taupter/msx-picoverse-public/2350/case/docs/log.md

# Change Log

## PicoVerse 2350 Case v1.0

- Updated the case README to describe the OBJ shell files, STL button file, and version 1.0 case model attribution.
- Updated the packaging Makefile to mirror `2350/case` into the public `2350/case` output, matching the existing 2040 case copy flow.
