taupter/msx-picoverse-public/2040/case/docs/log.md

# Change Log

## PicoVerse 2040 Case v1.41

- Added a case README describing the version 1.41 files, Pakoto case STL files, and Paco Baron attribution.
