taupter/msx-picoverse-public/docs/msx-picoverse-2350-features.md

# MSX PicoVerse 2350 Features

The MSX PicoVerse 2350 is a Raspberry Pi Pico 2350-based MSX-compatible cartridge that offers a variety of features to enhance the MSX experience. Below is a list of its key features:

- **Multi-ROM Support**: The cartridge can store and run multiple MSX ROMs, allowing users to run different games and applications from a single cartridge.
- **Built-in Menu System**: A user-friendly menu system allows users to select and launch ROMs easily.
- **Explorer Firmware**: Unified menu that merges ROMs from flash and microSD in a single list, with MP3/WAV playback from microSD, File Hunter browsing over ESP-01 WiFi, multi-partition microSD browsing, and on-device file deletion for selected SD files.
- **Source Labels (FL/SD)**: Each ROM entry shows whether it comes from flash or microSD.
- **High Compatibility**: Supports a wide range of MSX ROMs, including games and applications for MSX1, MSX2, and MSX2+ systems.
- **Nextor DOS Support**: Compatible with Nextor DOS, enabling advanced file management and storage options. Currently supports Nextor OS 2.1.4 on USB storage and FAT16 microSD partitions up to 4 GB. You can run DSK files using Nextor.
- **Long Name Support**: Supports ROM names up to 60 characters, making it easier to identify games and applications.
- **Support for Various Mappers**: Includes support for multiple ROM mappers, enhancing compatibility with different types of MSX software. Mapper tags supported include: PLA-16, PLA-32, KonSCC, PLN-48, PLN-64, ASC-08, ASC-16, ASC-16X, Konami, NEO-8, NEO-16, and MANBW2.
- **Space Manbow 2 Support**: Dedicated mapper (MANBW2) for Space Manbow 2 ROMs, emulating the AMD AM29F040B flash chip used by the game for save data. Auto-detected for 512 KB Manbow 2 ROMs; save data is volatile (SRAM-backed).
- **openMSX ROM Database**: The LoadROM and MultiROM tools include an embedded SHA-1 database derived from openMSX's `softwaredb.xml`, improving mapper auto-detection accuracy for titles that cannot be reliably identified by heuristic scanning alone.
- **Sunrise IDE Emulation (USB)**: The LoadROM and MultiROM tools support Sunrise IDE emulation via the `-s2` option, embedding the Nextor 2.1.4 Sunrise IDE kernel and bridging USB mass storage (flash drives, USB-to-SD adapters) through the cartridge's USB-C port. The MSX sees a standard Sunrise IDE hard disk. In MultiROM, the Sunrise options can be combined to add multiple SYSTEM entries to the menu.
- **Sunrise IDE Emulation (microSD)**: The `-s1` option provides the same Sunrise IDE emulation but uses the on-board microSD card slot instead of USB. Nextor storage uses FAT16 microSD partitions up to 4 GB. The microSD card is accessed via SPI at 31.25 MHz. Real card identification (OEM, product name, revision) is read from the SD CID register and shown during Nextor boot.
- **Explorer Sunrise Nextor Partition Selection**: Explorer Sunrise Nextor SYSTEM entries can select among compatible FAT16 microSD partitions up to 4 GB. The selected partition label is shown on the ROM detail screen and saved in that ROM's `.PVC` options file. The normal `F2` microSD browser separately supports cycling FAT16, FAT32, and exFAT browsing partitions with `P`.
- **Sunrise IDE + 1MB PSRAM Memory Mapper (USB)**: The `-m2` option combines Sunrise IDE emulation via USB with a 1MB memory mapper (64 × 16KB pages) in an expanded sub-slot architecture. The mapper RAM is backed by external PSRAM on GPIO47 / QMI CS1. Sub-slot 0 serves the Nextor ROM, sub-slot 1 provides the mapper RAM across all four 16KB pages, and mapper page registers (I/O ports FC–FF) are intercepted via PIO1.
- **Sunrise IDE + 1MB PSRAM Memory Mapper (microSD)**: The `-m1` option provides the same mapper architecture as `-m2` but uses the on-board microSD card for storage instead of USB.
- **ESP-01 WiFi Support For Sunrise IDE Modes**: Both the LoadROM and MultiROM tools accept `-w` together with `-s1`, `-m1`, `-s2`, or `-m2`, adding an embedded ESP8266P system ROM and a memory-mapped UART backend for the PicoVerse 2350 ESP-01 header. In MultiROM `-w` is applied to every selected Sunrise IDE entry and is not added to `-c1`/`-c2` Carnivore2 entries. Detailed behaviour is documented in the WiFi guide.
- **Explorer File Hunter Browser**: Press `F3` in Explorer to browse File Hunter through the ESP-01 WiFi module, search online results from the MSX, download ROMs into PSRAM, and save them as `.ROM` files directly in the microSD root.
- **Explorer WiFi Configuration**: Press `F4` in Explorer to enter the WiFi setup flow used by the ESP8266P-compatible WiFi firmware.
- **ROM Loading to PSRAM Mapper via `SROM.COM` (USB)**: The `-c2` option (LoadROM and MultiROM) exposes the cartridge as a Carnivore2-compatible RAM target on top of the 1MB PSRAM mapper, allowing `SROM.COM /D15` to upload ROM files into PSRAM and execute them from RAM while using USB mass storage as the Nextor backend. When combined with `-scc` / `-sccplus`, SROM-uploaded Konami SCC / SCC+ ROMs play through the cartridge's I2S audio path.
- **ROM Loading to PSRAM Mapper via `SROM.COM` (microSD)**: The `-c1` option (LoadROM and MultiROM) provides the same Carnivore2-compatible PSRAM loading workflow as `-c2`, but uses the on-board microSD card as the Nextor backend. SCC / SCC+ emulation is also supported via `-scc` / `-sccplus`.
- **Support for up to 1024 entries (Explorer)**: Per folder view, including ROMs and MP3s; the root view can also include flash entries.
- **Paged ROM List**: The menu loads pages on demand to keep the ROM list responsive with large libraries.
- **Search by Name (Explorer)**: Press `/`, type a query, and press Enter to jump to the first match.
- **microSD Partition Cycle (Explorer)**: Press `P` in the `F2` microSD screen to cycle supported FAT16, FAT32, and exFAT primary/logical partitions. The selected browsing partition is persisted in `/PICOVERSE.PVC`.
- **microSD File Delete (Explorer)**: Press `D` in the `F2` microSD screen to delete the selected file after confirmation. Folders cannot be deleted from Explorer.
- **Search File Hunter (Explorer)**: Press `/` inside File Hunter to run an online File Hunter query and reload the result list.
- **On-device 40/80 Column Toggle**: Press `C` to switch between compact 40-column and wide 80-column menu layouts (when supported by the MSX model).
- **MP3 Player**: MP3 files on microSD appear in the menu and open a player screen with Play/Stop, Pause/Resume, playback status, and elapsed time.
- **ROM Detail Screen**: ROM entries open a details screen with mapper detection/override, cartridge audio profile selection, optional primary PSG DAC mirroring, and WiFi enablement for supported Sunrise Nextor entries before running.
- **SYSTEM ROM Priority**: System ROM entries remain at the top of the list, separate from name sorting.
- **microSD ROM Execution up to 4 MB**: ROM files on the microSD card are streamed into the cartridge's external 8 MB PSRAM (QMI CS1, 52.5 MHz QPI) and executed directly from there. The leading window of the ROM is also mirrored into the 256 KB PSRAM ROM cache for mapper hot-loop access. The size cap per microSD ROM is 4 MB.
- **Easy ROM Management**: Users can easily add, remove, and organize ROMs using a simple tool on their PC.
- **Fast Loading Times**: Utilizes the high-speed capabilities of the Raspberry Pi Pico to ensure quick loading times for games and applications.
- **Firmware Updates**: The cartridge firmware can be updated via USB, allowing users to benefit from new features and improvements over time.
- **Compact Design**: The cartridge is designed to fit seamlessly into MSX systems without adding bulk.
- **SD Card Slot**: Equipped with an SD card slot for easy storage and transfer of ROMs and files.
- **Audio Profile Selection**: Allows users to select mutually exclusive per-ROM cartridge audio profiles: None, SCC, SCC+, external SCC/SCC+, Dual PSG, MSX-MUSIC, or YM2151/SFG when supported by the selected mapper.
- **Primary PSG Mirroring**: Explorer ROM launches include an independent **PSG** Yes/No option. When enabled, the Pico captures primary PSG writes on ports `0xA0`/`0xA1`, generates matching AY/YM audio through `emu2149`, and mixes it into the cartridge I2S DAC output alongside the selected audio profile.
- **SCC/SCC+ Emulation**: When enabled for Konami SCC or Manbow2 mapper ROMs, the cartridge can emulate the SCC and SCC+ sound chips in hardware, providing accurate audio output through an I2S DAC connected to the RP2350. Explorer also offers external SCC/SCC+ profiles for non-SYSTEM ROMs and Sunrise Nextor SYSTEM entries that expect an SCC cartridge in another slot; regular ROMs run the game mapper in subslot 0 and expose a virtual SCC/SCC+ surface in subslot 1, while Sunrise Nextor entries keep storage active and place SCC/SCC+ in a free subslot. The Explorer ROM screen pre-selects **SCC** as the default audio profile when a ROM is detected as Konami SCC (`KonSCC`) or Manbow2 (`MANBW2`). This allows games that use SCC or SCC+ sound to have their full soundtrack without requiring an original SCC cartridge. For details on supported registers and behavior, see the [SCC/SCC+ documentation](docs/msx-picoverse-2350-scc.md).
- **Dual PSG Emulation**: A secondary AY-3-8910 (PSG) engine can be enabled per ROM. In LoadROM this is selected with the `-d` flag; in Explorer it is selected from the ROM screen as **Dual PSG** for regular non-SYSTEM ROMs that are not Konami SCC or Manbow2. The Pico captures `OUT (0x10),A` (register select) and `OUT (0x11),A` (data) on the MSX I/O bus through a dedicated PIO1 write captor and mixes the synthesized output into the same I2S DAC used by the SCC engine. Dual PSG is mutually exclusive with SCC/SCC+ and MSX-MUSIC as a cartridge audio profile, but Explorer's separate **PSG** option can still mirror the primary PSG alongside it. When both are enabled, Explorer routes Dual PSG to left and the mirrored primary PSG to right for stereo separation. For implementation details, see the [Dual PSG documentation](./msx-picoverse-2350-dualpsg.md).
- **MSX-MUSIC Emulation**: A YM2413/MSX-MUSIC engine can be enabled per ROM. In Explorer it is selected from the ROM screen as **MSX-MUSIC** for regular non-SYSTEM ROMs that are not Konami SCC or Manbow2. The firmware captures writes to MSX-MUSIC ports `0x7C` and `0x7D`, routes synthesized audio through I2S, and exposes an FM-PAC-compatible BIOS from a hidden Explorer UF2 flash payload instead of embedding it in the Pico firmware binary. MSX-MUSIC is mutually exclusive with SCC/SCC+ and Dual PSG as a cartridge audio profile, and can be mixed with Explorer's separate primary PSG mirror.
- **YM2151 / Yamaha SFG Emulation**: Explorer offers **YM2151 (SFG05)** and **YM2151 (SFG01)** profiles for supported game ROMs and Sunrise Nextor SYSTEM ROMs. Game ROMs run the selected mapper in expanded subslot 0 and expose the SFG-like YM2151 surface plus the selected SFG BIOS image in subslot 1. Sunrise Nextor SYSTEM launches keep Nextor and mapper RAM in their SYSTEM layout and place the SFG cartridge in a free subslot, using subslot 2 without WiFi or subslot 3 with WiFi. The SFG 64K ROM is stored as a hidden Explorer flash payload; SFG05 uses the first 32K image and SFG01 uses the second 32K image.
