taupter/msx-picoverse-public/images/2026-05-23_17-53.png

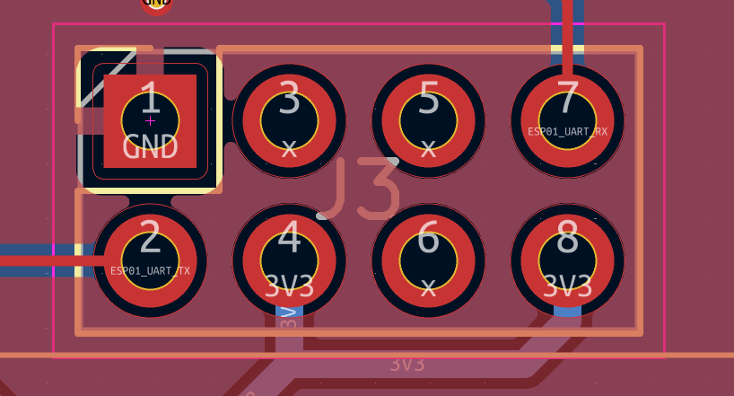
images/2026-05-23_17-53.png
