taupter/msx-picoverse-public/2040/software/loadrom.pio/pico/joystick/tusb_config.h

// MSX PICOVERSE PROJECT
// (c) 2026 Cristiano Goncalves
// The Retro Hacker
//
// tusb_config.h - TinyUSB configuration for standalone USB joystick firmware
//
// Uses HID report protocol (not boot protocol) because gamepads do not
// have a standardised boot protocol.  The firmware parses HID report
// descriptors at enumeration time to locate D-pad, analog stick, and
// button fields.
//
// Also supports XInput (Xbox 360) controllers via a custom class driver
// that claims vendor-specific interfaces (class 0xFF, subclass 0x5D).
//
// This work is licensed under a "Creative Commons Attribution-NonCommercial-ShareAlike 4.0 International
// License". https://creativecommons.org/licenses/by-nc-sa/4.0/

#ifndef _TUSB_CONFIG_H_
#define _TUSB_CONFIG_H_

#ifdef __cplusplus
 extern "C" {
#endif

//--------------------------------------------------------------------
// COMMON CONFIGURATION
//--------------------------------------------------------------------

#ifndef CFG_TUSB_MCU
  #error CFG_TUSB_MCU must be defined
#endif

#define CFG_TUSB_RHPORT0_MODE       OPT_MODE_HOST

#ifndef CFG_TUSB_OS
#define CFG_TUSB_OS                 OPT_OS_NONE
#endif

#ifndef CFG_TUSB_MEM_SECTION
#define CFG_TUSB_MEM_SECTION
#endif

#ifndef CFG_TUSB_MEM_ALIGN
#define CFG_TUSB_MEM_ALIGN          __attribute__ ((aligned(4)))
#endif

//--------------------------------------------------------------------
// HOST CONFIGURATION
//--------------------------------------------------------------------

// Use report protocol — gamepads have no standard boot protocol.
// The firmware parses HID report descriptors to find field offsets.
#define CFG_TUH_HID_DEFAULT_PROTOCOL  HID_PROTOCOL_REPORT

#define CFG_TUH_ENUMERATION_BUFSIZE 512

#define CFG_TUH_HUB                 1
#define CFG_TUH_CDC                 0
#define CFG_TUH_HID                 4
#define CFG_TUH_MIDI                0
#define CFG_TUH_MSC                 0
#define CFG_TUH_VENDOR              0

#define CFG_TUH_DEVICE_MAX          (CFG_TUH_HUB ? 4 : 1)

#define CFG_TUH_HID_EPIN_BUFSIZE    64
#define CFG_TUH_HID_EPOUT_BUFSIZE   64

#ifdef __cplusplus
 }
#endif

#endif /* _TUSB_CONFIG_H_ */
