taupter/msx-picoverse-public/2350/software/explorer.pio/pico/explorer/explorer.c

// MSX PICOVERSE PROJECT
// (c) 2025 Cristiano Goncalves
// The Retro Hacker
//
// explorer.c - PicoVerse 2350 Explorer firmware (ROM loader + SD support)
//
// This work is licensed  under a "Creative Commons Attribution-NonCommercial-ShareAlike 4.0 International
// License". https://creativecommons.org/licenses/by-nc-sa/4.0/

#include <stdio.h>
#include <string.h>
#include <ctype.h>
#include <stdlib.h>
#include <stdarg.h>
#include "ff.h"
#include "diskio.h"
#include "my_rtc.h"
#include "pico/stdlib.h"
#include "pico/multicore.h"
#include "pico/unique_id.h"
#include "hardware/clocks.h"
#include "hardware/dma.h"
#include "hardware/pio.h"
#include "hardware/structs/qmi.h"
#include "hardware/regs/qmi.h"
#include "hardware/structs/xip_ctrl.h"
#include "hardware/sync.h"
#include "hardware/uart.h"
#include "hardware/regs/uart.h"
#include "hardware/irq.h"
#include "hw_config.h"
#include "explorer.h"
#include "mapper_detect.h"
#include "mp3.h"
#include "c2_emu.h"
#include "emu2212.h"
#include "emu2149.h"
#include "emu2413.h"
#include "emu2151.h"
#include "msx_bus.pio.h"
#include "pico/audio_i2s.h"
#include "sunrise_ide.h"
#include "sunrise_sd.h"

// config area and buffer for the ROM data
#define ROM_NAME_MAX    71          // Maximum size of the ROM name on the 80-column detail screen
#define MAX_ROM_RECORDS 1024        // Maximum ROM files supported (flash + SD)
#define MAX_FLASH_RECORDS 128       // Maximum ROM files stored in flash
#define ROM_RECORD_SIZE (ROM_NAME_MAX + 1 + (sizeof(uint32_t) * 2)) // Name + mapper + size + offset
#define MENU_ROM_SIZE   (32u * 1024u) // Full menu ROM size stored before config records
#define CONFIG_AREA_SIZE (16u * 1024u)
#define ROM_SELECT_MENU 0xFEu
#define ROM_SELECT_WIFI_CONFIG 0xFFF0u
#define WIFI_CONFIG_FLASH_OFFSET (MENU_ROM_SIZE + CONFIG_AREA_SIZE)
#define WIFI_CONFIG_ROM_SIZE (8u * 1024u)
#define WIFI_BIOS_FLASH_OFFSET (WIFI_CONFIG_FLASH_OFFSET + WIFI_CONFIG_ROM_SIZE)
#define WIFI_BIOS_ROM_SIZE (16u * 1024u)
#define FMPAC_BIOS_FLASH_OFFSET (WIFI_BIOS_FLASH_OFFSET + WIFI_BIOS_ROM_SIZE)
#define FMPAC_BIOS_ROM_SIZE (64u * 1024u)
#define SFG_BIOS_FLASH_OFFSET (FMPAC_BIOS_FLASH_OFFSET + FMPAC_BIOS_ROM_SIZE)
#define SFG_BIOS_ROM_SIZE (64u * 1024u)
#define WIFI_CONFIG_RETURN_MENU 0xE0u
#define MONITOR_ADDR    (0xBF7F)    // ROM select register just below the menu control window
#define CACHE_SIZE      (256u * 1024u)     // 256KB cache size for ROM data

#define SOURCE_SD_FLAG  0x80 // Flag in the mapper byte indicating the ROM is on SD
#define FOLDER_FLAG     0x40 // Flag in the mapper byte indicating the record is a folder
#define MP3_FLAG        0x20 // Flag in the mapper byte indicating the record is an MP3 file
#define OVERRIDE_FLAG   0x10 // Flag in the mapper byte indicating manual override
#define AUDIO_TYPE_MASK 0x0F // Low bits identify audio subtypes when MP3_FLAG is set
#define AUDIO_TYPE_WAV  0x01 // Audio subtype: PCM WAV file

#define EXPLORER_MP3_DISABLED 0

#define FILES_PER_PAGE  19 // Maximum files per page on the menu
#define CTRL_BASE_ADDR  0xBFF0 // Control registers base address
#define CTRL_COUNT_L    (CTRL_BASE_ADDR + 0) // Control: total record count low byte
#define CTRL_COUNT_H    (CTRL_BASE_ADDR + 1) // Control: total record count high byte
#define CTRL_PAGE       (CTRL_BASE_ADDR + 2) // Control: current page index
#define CTRL_STATUS     (CTRL_BASE_ADDR + 3) // Control: status register
#define CTRL_CMD        (CTRL_BASE_ADDR + 4) // Control: command register
#define CTRL_MATCH_L    (CTRL_BASE_ADDR + 5) // Control: match index low byte
#define CTRL_MATCH_H    (CTRL_BASE_ADDR + 6) // Control: match index high byte
#define CTRL_MAPPER     (CTRL_BASE_ADDR + 7) // Control: mapper value
#define CTRL_ACK        (CTRL_BASE_ADDR + 8) // Control: command ack
#define CTRL_MAGIC      0xA5 // Control: magic value to indicate valid command
#define CTRL_STATUS_SD_MISSING 0x5D // Control: selected source is microSD but no card is available
#define CTRL_QUERY_BASE 0xBFC0 // Control: query string base address
#define CTRL_QUERY_SIZE 32 // Control: query string size
#define CMD_APPLY_FILTER 0x01 // Command: apply filter
#define CMD_FIND_FIRST   0x02 // Command: find first match
#define CMD_ENTER_DIR    0x03 // Command: enter directory
#define CMD_DETECT_MAPPER 0x04 // Command: detect mapper on demand
#define CMD_SET_MAPPER    0x05 // Command: set mapper override
#define CMD_SET_SOURCE    0x06 // Command: switch visible source set
#define CMD_LOAD_OPTIONS  0x07 // Command: load ROM options from microSD .PVC file
#define CMD_SAVE_OPTIONS  0x08 // Command: save ROM options to microSD .PVC file
#define CMD_PREPARE_QUICK_RUN 0x09 // Command: load saved/default launch options for quick-run
#define CMD_CYCLE_SD_PARTITION 0x0A // Command: cycle Explorer microSD browse partition
#define CMD_DELETE_SD_FILE 0x0B // Command: delete selected Explorer microSD file
#define CMD_FH_LIST_PAGE   0x40 // Command: File Hunter list page from menu ROM
#define CMD_FH_DOWNLOAD    0x41 // Command: File Hunter download/save from menu ROM
#define CMD_FH_SEARCH      0x42 // Command: File Hunter search from menu ROM
#define CMD_FH_WIFI_STATUS 0x43 // Command: File Hunter WiFi status from menu ROM
#define CMD_FH_WIFI_CONFIG 0x44 // Command: File Hunter WiFi setup from menu ROM

#define FH_CTRL_BASE    0xBFF0
#define FH_COUNT_L      (FH_CTRL_BASE + 0)
#define FH_COUNT_H      (FH_CTRL_BASE + 1)
#define FH_PAGE         (FH_CTRL_BASE + 2)
#define FH_STATUS       (FH_CTRL_BASE + 3)
#define FH_CMD          (FH_CTRL_BASE + 4)
#define FH_SELECT_L     (FH_CTRL_BASE + 5)
#define FH_SELECT_H     (FH_CTRL_BASE + 6)
#define FH_PROGRESS_L   (FH_CTRL_BASE + 7)
#define FH_PROGRESS_H   (FH_CTRL_BASE + 8)
#define FH_RESULT       (FH_CTRL_BASE + 9)
#define FH_QUERY_BASE   0xBFC0
#define FH_QUERY_SIZE   32
#define FH_STATUS_TEXT_BASE 0xBF80
#define FH_STATUS_TEXT_SIZE 64
#define CTRL_CHIP_ID_BASE (FH_STATUS_TEXT_BASE + FH_STATUS_TEXT_SIZE - 17u) // Control: Pico unique board ID string
#define CTRL_CHIP_ID_SIZE 17u // Control: 16 hex digits plus terminator
#define CTRL_SD_PARTITION_INFO_BASE FH_STATUS_TEXT_BASE
#define CTRL_SD_PARTITION_INFO_SIZE 32u
#define CTRL_VDP_FREQ   0xBFA0 // Control: per-ROM VDP 50/60Hz load read-back (Pico -> MSX)
#define VDP_FREQ_DEFAULT 0u
#define VDP_FREQ_60HZ    1u
#define VDP_FREQ_50HZ    2u
#define FH_DATA_BASE    0xB900
#define FH_RECORD_FLAG_OFFSET ROM_NAME_MAX
#define FH_RECORD_SIZE_OFFSET (FH_RECORD_FLAG_OFFSET + 1u)
#define FH_RECORD_SIZE  (ROM_NAME_MAX + 3u)
#define FH_FILES_PER_PAGE 19
#define FH_MAX_RESULTS 384
#define FH_HTTP_BUFFER_SIZE (256u * 1024u)
#define FH_HTTP_CHUNK_SIZE 2048u
#define FH_HOST "msxpico.file-hunter.com"
#define FH_ENDPOINT "/picoverse.php"
#define FH_DEFAULT_QUERY "1"
#define FH_WIFI_CONNECT_WAIT_US 30000000u
#define FH_STATUS_READY 0xA5
#define FH_STATUS_BUSY  0x5A
#define FH_RESULT_SAVING 0x02
#define FH_RECORD_FLAG_MESSAGE 0x80u
#define FH_CMD_LIST_PAGE 0x01
#define FH_CMD_DOWNLOAD  0x02
#define FH_CMD_EXIT      0x03
#define FH_CMD_SEARCH    0x04
#define FH_CMD_WIFI_STATUS 0x05

#define SOURCE_MODE_ALL   0x00
#define SOURCE_MODE_FLASH 0x01
#define SOURCE_MODE_SD    0x02
#define SOURCE_MODE_FILEHUNTER 0x03

#define CTRL_AUDIO      (CTRL_BASE_ADDR + 9) // Control: audio profile selection
#define CTRL_WIFI_SUPPORT (CTRL_BASE_ADDR + 10) // Control: Sunrise WiFi support (0=No, 1=Yes)
#define CTRL_PSG_EMULATION (CTRL_BASE_ADDR + 11) // Control: primary PSG emulation (0=No, 1=Yes)
#define CTRL_WAVEGAME_ROM (CTRL_BASE_ADDR + 12) // Control: selected SD ROM has WAVEGAME sidecar audio
#define CTRL_SD_PARTITION (CTRL_BASE_ADDR + 13) // Control: selected Sunrise SD partition number
#define CTRL_SD_BROWSE_PARTITION (CTRL_BASE_ADDR + 14) // Control: selected Explorer microSD partition number
#define CTRL_AUDIO_VOLUME (CTRL_BASE_ADDR + 15) // Control: per-ROM audio volume percent

#define AUDIO_PROFILE_NONE       0u
#define AUDIO_PROFILE_SCC        1u
#define AUDIO_PROFILE_SCC_PLUS   2u
#define AUDIO_PROFILE_DUAL_PSG 3u
#define AUDIO_PROFILE_MSX_MUSIC 4u
#define AUDIO_PROFILE_SCC_EXTERNAL 5u
#define AUDIO_PROFILE_SCC_PLUS_EXTERNAL 6u
#define AUDIO_PROFILE_YM2151_SFG05 7u
#define AUDIO_PROFILE_YM2151_SFG01 8u
#define AUDIO_PROFILE_MEGARAM_SCC 9u
#define AUDIO_PROFILE_MEGARAM_SCC_PLUS 10u

#define PSG_SAMPLE_RATE 44100
#define PSG_CLOCK       1789773
#define PSG_VOLUME_SHIFT 2
#define PSG_QUALITY_FAST 0
#define PSG_QUALITY_HIGH 1
#define PSG_PORT_REG    0x10u
#define PSG_PORT_DATA   0x11u
#define MAIN_PSG_PORT_REG  0xA0u
#define MAIN_PSG_PORT_DATA 0xA1u

#define MSX_MUSIC_SAMPLE_RATE 44100
#define MSX_MUSIC_CLOCK       3579545
#define MSX_MUSIC_VOLUME_SHIFT 2
#define MSX_MUSIC_PSG_VOLUME_SHIFT 0
/* Soft-knee limiter for the post-gain FM sample: below the knee the output is
 * a pure linear MSX_MUSIC_VOLUME_SHIFT gain (so normal games are unchanged);
 * above the knee, loud/dense OPLL content is smoothly compressed toward the
 * ceiling instead of hard-clipping (which produced a robotic, low-volume tone
 * on heavy arrangements like Aleste Gaiden). */
#define MSX_MUSIC_LIMIT_KNEE  24000
#define MSX_MUSIC_LIMIT_CEIL  32767
#define MSX_MUSIC_PORT_REG    0x7Cu
#define MSX_MUSIC_PORT_DATA   0x7Du
#define FMPAC_BIOS_SIZE       FMPAC_BIOS_ROM_SIZE
#define SFG_BIOS_SIZE         SFG_BIOS_ROM_SIZE
#define SFG_BIOS_VARIANT_SIZE (32u * 1024u)

#define AUDIO_VOLUME_DEFAULT 100u
#define AUDIO_VOLUME_MAX     200u

#define YM2151_SAMPLE_RATE    44100
#define YM2151_CLOCK          3579545u
#define YM2151_FRAME_DIVIDER  64u
#define YM2151_CYCLES_PER_FRAME 1u
#define YM2151_WRITE_APPLY_CYCLES 0u
#define YM2151_WRITE_SERVICE_BUDGET 4u
#define YM2151_WRITE_QUEUE_SIZE 512u
#define YM2151_WRITE_QUEUE_MASK (YM2151_WRITE_QUEUE_SIZE - 1u)
#define YM2151_PSG_VOLUME_SHIFT 0
#define YM2151_BASE_VOLUME_PERCENT 200u

#define WIFI_MEM_F2_ADDR      0x7F05u
#define WIFI_MEM_CMD_ADDR     0x7F06u
#define WIFI_MEM_DATA_ADDR    0x7F07u
#define WIFI_F2_FORCE_SETUP   0xF1u
#define WIFI_RX_FIFO_SIZE     2080u
#define WIFI_RX_SERVICE_BUDGET 32u
#define WIFI_QUICK_WAIT_US    25000u
#define WIFI_UART_DEFAULT_BAUD 859372u
#define WIFI_STATUS_RX_READY  0x01u
#define WIFI_STATUS_TX_BUSY   0x02u
#define WIFI_STATUS_RX_FULL   0x04u
#define WIFI_STATUS_QUICK_RX  0x08u
#define WIFI_STATUS_UNDERRUN  0x10u
#define WIFI_STATUS_FREE_BITS 0x80u
#define WIFI_UART_INSTANCE    uart1

#define DATA_BASE_ADDR   0xB900 // Data buffer base address
#define DATA_BUFFER_SIZE (FH_STATUS_TEXT_BASE - DATA_BASE_ADDR) // Data buffer size
#define DATA_MAGIC_0     'P' // Data header magic bytes
#define DATA_MAGIC_1     'V' // Data header magic bytes
#define DATA_MAGIC_2     'E' // Data header magic bytes
#define DATA_MAGIC_3     'X' // Data header magic bytes
#define DATA_VERSION     1 // Data header version
#define DATA_HEADER_SIZE 24 // Data header size in bytes
#define DATA_RECORD_TABLE_ENTRY_SIZE 4 // Size of each record table entry
#define DATA_RECORD_PAYLOAD_SIZE 13 // Minimum size of each record payload
#define TLV_NAME_OFFSET  0x01 // Type-Length-Value: Name offset
#define TLV_MAPPER       0x02 // Type-Length-Value: Mapper
#define TLV_SIZE         0x03 // Type-Length-Value: Size

#define PVC_OPTIONS_MAGIC_0 'P'
#define PVC_OPTIONS_MAGIC_1 'V'
#define PVC_OPTIONS_MAGIC_2 'C'
#define PVC_OPTIONS_MAGIC_3 '1'
#define PVC_OPTIONS_LEGACY_SIZE 6u
#define PVC_OPTIONS_MAPPER_SIZE 7u
#define PVC_OPTIONS_PARTITION_SIZE 8u
#define PVC_OPTIONS_VOLUME_SIZE 9u
#define PVC_OPTIONS_SIZE 10u

#define PV_CONFIG_MAGIC_0 'P'
#define PV_CONFIG_MAGIC_1 'V'
#define PV_CONFIG_MAGIC_2 'C'
#define PV_CONFIG_MAGIC_3 'F'
#define PV_CONFIG_SIZE 5u
#define PV_CONFIG_PATH "/PICOVERSE.PVC"


// MP3 control registers
#define MP3_CTRL_BASE      0xBFE0 // MP3 control registers base address
#define MP3_CTRL_CMD       (MP3_CTRL_BASE + 0)
#define MP3_CTRL_STATUS    (MP3_CTRL_BASE + 1)
#define MP3_CTRL_INDEX_L   (MP3_CTRL_BASE + 2)
#define MP3_CTRL_INDEX_H   (MP3_CTRL_BASE + 3)
#define MP3_CTRL_ELAPSED_L (MP3_CTRL_BASE + 4)
#define MP3_CTRL_ELAPSED_H (MP3_CTRL_BASE + 5)
#define MP3_CTRL_TOTAL_L   (MP3_CTRL_BASE + 6)
#define MP3_CTRL_TOTAL_H   (MP3_CTRL_BASE + 7)
#define MP3_CTRL_MODE      (MP3_CTRL_BASE + 8)

// MSX protocol command code for MP3 file selection (local to explorer.c)
#define MP3_CMD_SELECT      0x01

typedef struct {
    PIO pio;
    uint sm_read;
    uint sm_write;
    uint offset_read;
    uint offset_write;
} msx_pio_bus_t;

typedef struct {
    PIO pio_read;
    PIO pio_write;
    uint sm_io_read;
    uint sm_io_write;
    uint offset_io_read;
    uint offset_io_write;
} msx_pio_io_bus_t;

static msx_pio_bus_t msx_bus;
static bool msx_bus_programs_loaded = false;
static msx_pio_io_bus_t msx_io_bus;
static bool msx_io_read_program_loaded = false;
static bool msx_io_write_program_loaded = false;

typedef struct {
    uint16_t rom_index;
    bool rom_selected;
} menu_select_ctx_t;

typedef struct {
    uint8_t *bank_regs;
} bank8_ctx_t;

typedef struct {
    uint16_t *bank_regs;
} bank16_ctx_t;

typedef struct {
    uint8_t page;
    uint8_t control;
    uint8_t sram_key_5ffe;
    uint8_t sram_key_5fff;
    uint8_t sram[8192];
} fmpac_state_t;

// This symbol marks the end of the main program in flash.
// Custom data starts right after it
extern const uint8_t __flash_binary_end[];

// PSRAM-backed buffer to cache ROM data
static uint8_t *rom_sram = NULL;
static uint32_t active_rom_size = 0;
static uint32_t rom_cached_size = 0; // Added for PIO implementation
// Effective cache capacity used by prepare_rom_source(). Some mappers (e.g.
// Manbow2) reduce this so the tail of rom_sram can be repurposed (writable
// flash sector emulation), matching multirom's behaviour.
static uint32_t rom_cache_capacity = CACHE_SIZE;
static uint8_t page_buffer[DATA_BUFFER_SIZE];

// pointer to the custom data
static const uint8_t *flash_rom = (const uint8_t *)&__flash_binary_end;
static const uint8_t *rom_data = (const uint8_t *)&__flash_binary_end;
static bool rom_data_in_ram = false;

static uint8_t wifi_rx_fifo[WIFI_RX_FIFO_SIZE];
static volatile uint16_t wifi_rx_head = 0u;
static volatile uint16_t wifi_rx_tail = 0u;
static volatile uint16_t wifi_rx_count = 0u;
static uint8_t wifi_f2_state = 0xFFu;
static bool wifi_uart_ready = false;
static uint32_t wifi_uart_baud = WIFI_UART_DEFAULT_BAUD;
static uint32_t wifi_tx_busy_deadline_us = 0u;
static bool wifi_rx_underrun = false;

static void debug_trace(const char *fmt, ...)
{
#if EXPLORER_USB_STDIO_DEBUG
    va_list args;
    va_start(args, fmt);
    vprintf(fmt, args);
    va_end(args);
    printf("\r\n");
    fflush(stdout);
#else
    (void)fmt;
#endif
}

static inline void __not_in_flash_func(wifi_reset_fifo)(void)
{
    uint32_t irq_state = save_and_disable_interrupts();
    wifi_rx_head = 0u;
    wifi_rx_tail = 0u;
    wifi_rx_count = 0u;
    wifi_rx_underrun = false;
    restore_interrupts(irq_state);
}

static inline bool __not_in_flash_func(wifi_push_rx_byte_locked)(uint8_t data)
{
    if (wifi_rx_count >= WIFI_RX_FIFO_SIZE) return false;
    wifi_rx_fifo[wifi_rx_head] = data;
    wifi_rx_head = (uint16_t)((wifi_rx_head + 1u) % WIFI_RX_FIFO_SIZE);
    ++wifi_rx_count;
    return true;
}

static inline bool __not_in_flash_func(wifi_push_rx_byte)(uint8_t data)
{
    uint32_t irq_state = save_and_disable_interrupts();
    bool pushed = wifi_push_rx_byte_locked(data);
    restore_interrupts(irq_state);
    return pushed;
}

static inline bool __not_in_flash_func(wifi_pop_rx_byte)(uint8_t *data_out)
{
    uint32_t irq_state = save_and_disable_interrupts();
    if (wifi_rx_count == 0u)
    {
        restore_interrupts(irq_state);
        return false;
    }
    *data_out = wifi_rx_fifo[wifi_rx_tail];
    wifi_rx_tail = (uint16_t)((wifi_rx_tail + 1u) % WIFI_RX_FIFO_SIZE);
    --wifi_rx_count;
    restore_interrupts(irq_state);
    return true;
}

static inline uint16_t __not_in_flash_func(wifi_rx_count_snapshot)(void)
{
    uint32_t irq_state = save_and_disable_interrupts();
    uint16_t count = wifi_rx_count;
    restore_interrupts(irq_state);
    return count;
}

static inline bool __not_in_flash_func(wifi_hw_tx_busy)(void)
{
    return (uart_get_hw(WIFI_UART_INSTANCE)->fr & UART_UARTFR_BUSY_BITS) != 0u;
}

static inline void __not_in_flash_func(wifi_hw_rx_drain)(void)
{
    uint32_t irq_state = save_and_disable_interrupts();
    while (uart_is_readable(WIFI_UART_INSTANCE))
    {
        (void)uart_getc(WIFI_UART_INSTANCE);
    }
    restore_interrupts(irq_state);
}

static inline void __not_in_flash_func(wifi_pio_rx_reset)(void)
{
    wifi_hw_rx_drain();
}

static inline void __not_in_flash_func(wifi_pio_tx_reset)(void)
{
    while (wifi_hw_tx_busy()) { }
    wifi_tx_busy_deadline_us = 0u;
}

static inline void __not_in_flash_func(wifi_service_rx)(void)
{
    uint16_t budget = WIFI_RX_SERVICE_BUDGET;
    uint32_t irq_state;

    if (!wifi_uart_ready) return;
    irq_state = save_and_disable_interrupts();
    while (budget-- != 0u && uart_is_readable(WIFI_UART_INSTANCE))
    {
        if (!wifi_push_rx_byte_locked((uint8_t)uart_getc(WIFI_UART_INSTANCE))) break;
    }
    restore_interrupts(irq_state);
}

static void __not_in_flash_func(wifi_uart_rx_irq)(void)
{
    while (uart_is_readable(WIFI_UART_INSTANCE))
    {
        uint8_t data = (uint8_t)uart_getc(WIFI_UART_INSTANCE);
        (void)wifi_push_rx_byte_locked(data);
    }
}

static inline uint32_t __not_in_flash_func(wifi_uart_frame_time_us)(void)
{
    return (10000000u + (wifi_uart_baud - 1u)) / wifi_uart_baud;
}

static inline void __not_in_flash_func(wifi_uart_init_once)(void)
{
    if (wifi_uart_ready) return;

    (void)uart_init(WIFI_UART_INSTANCE, wifi_uart_baud);
    gpio_set_function(PIN_ESP_UART_TX, GPIO_FUNC_UART_AUX);
    gpio_set_function(PIN_ESP_UART_RX, GPIO_FUNC_UART_AUX);
    uart_set_format(WIFI_UART_INSTANCE, 8, 1, UART_PARITY_NONE);
    uart_set_hw_flow(WIFI_UART_INSTANCE, false, false);
    uart_set_fifo_enabled(WIFI_UART_INSTANCE, true);

    wifi_hw_rx_drain();
    wifi_f2_state = 0xFFu;
    wifi_reset_fifo();
    wifi_tx_busy_deadline_us = 0u;
    wifi_uart_ready = true;

    int uart_irq = (WIFI_UART_INSTANCE == uart0) ? UART0_IRQ : UART1_IRQ;
    irq_set_exclusive_handler(uart_irq, wifi_uart_rx_irq);
    irq_set_enabled(uart_irq, true);
    uart_set_irq_enables(WIFI_UART_INSTANCE, true, false);
}

static inline void __not_in_flash_func(wifi_handle_cmd_write)(uint8_t cmd)
{
    wifi_uart_init_once();
    if (cmd == 20u)
    {
        wifi_reset_fifo();
        wifi_pio_tx_reset();
        wifi_pio_rx_reset();
    }
}

static inline uint8_t __not_in_flash_func(wifi_status_read)(void)
{
    wifi_uart_init_once();
    wifi_service_rx();
    uint8_t status = 0u;
    uint16_t rx_count = wifi_rx_count_snapshot();
    if (rx_count != 0u) status |= WIFI_STATUS_RX_READY;
    if (rx_count >= WIFI_RX_FIFO_SIZE) status |= WIFI_STATUS_RX_FULL;
    if (wifi_hw_tx_busy() || !uart_is_writable(WIFI_UART_INSTANCE) ||
        (int32_t)(time_us_32() - wifi_tx_busy_deadline_us) < 0)
    {
        status |= WIFI_STATUS_TX_BUSY;
    }
    if (wifi_rx_underrun)
    {
        status |= WIFI_STATUS_UNDERRUN;
        wifi_rx_underrun = false;
    }
    return status;
}

static inline uint8_t __not_in_flash_func(wifi_data_read)(void)
{
    wifi_uart_init_once();

    uint8_t data;
    wifi_service_rx();
    if (wifi_pop_rx_byte(&data)) return data;

    uint32_t deadline = time_us_32() + WIFI_QUICK_WAIT_US;
    while ((int32_t)(time_us_32() - deadline) < 0)
    {
        wifi_service_rx();
        if (wifi_pop_rx_byte(&data)) return data;
    }

    wifi_rx_underrun = true;
    return 0xFFu;
}

static inline bool __not_in_flash_func(wifi_handle_mem_write)(uint16_t addr, uint8_t data)
{
    if (addr == WIFI_MEM_F2_ADDR) { wifi_f2_state = data; return true; }
    if (addr == WIFI_MEM_CMD_ADDR) { wifi_handle_cmd_write(data); return true; }
    if (addr == WIFI_MEM_DATA_ADDR)
    {
        wifi_uart_init_once();
        uart_putc_raw(WIFI_UART_INSTANCE, (char)data);
        wifi_tx_busy_deadline_us = time_us_32() + wifi_uart_frame_time_us();
        return true;
    }
    return false;
}

static inline uint8_t __not_in_flash_func(wifi_handle_mem_read)(const uint8_t *wifi_rom_base, uint32_t wifi_rom_size, uint16_t addr)
{
    if (addr == WIFI_MEM_F2_ADDR) return wifi_f2_state;
    if (addr == WIFI_MEM_CMD_ADDR) return wifi_data_read();
    if (addr == WIFI_MEM_DATA_ADDR) return wifi_status_read();
    if (addr >= 0x4000u && addr <= 0x7FFFu)
    {
        uint32_t rel = (uint32_t)(addr - 0x4000u);
        if (rel < wifi_rom_size) return wifi_rom_base[rel];
    }
    return 0xFFu;
}

// External PSRAM region used to buffer SD-loaded ROMs. Defined later
// alongside the PSRAM bring-up code; declared here for use by earlier
// functions such as load_rom_from_sd().
static psram_region_t sd_rom_region;
static psram_region_t rom_cache_region;
static psram_region_t mapper_region;
static psram_region_t c2_rom_region;
static psram_region_t megaram_region;
static psram_region_t mp3_buffer_region;
static psram_region_t fh_list_region;
static psram_region_t fh_download_region;
static bool psram_bring_up_once(void);
static bool psram_prepare_mp3_buffer(void);

uint8_t ctr_val = 0xFF;    
BYTE const pdrv = 0;  // Physical drive number
DSTATUS ds = 1; // Disk status (1 = not initialized)

// Structure to represent a ROM record
// The ROM record will contain the name of the ROM, the mapper code, the size of the ROM and the offset in the flash memory
// Name: ROM_NAME_MAX bytes
// Mapper: 1 byte
// Size: 4 bytes
// Offset: 4 bytes
typedef struct {
    char Name[ROM_NAME_MAX];
    unsigned char Mapper;
    unsigned long Size;
    unsigned long Offset;
} ROMRecord;

ROMRecord records[MAX_ROM_RECORDS]; // Array to store the ROM records

#define SD_PATH_MAX        256
#define SD_PATH_BUFFER_SIZE 19000
#define MIN_ROM_SIZE       8192
#define MAX_ROM_SIZE       (15u * 1024u * 1024u)
#define SD_ROM_MAX_SIZE    (4u * 1024u * 1024u) // PSRAM region capacity for SD-loaded ROMs
#define SD_BROWSE_PARTITION_MAX 20u
#define MP3_PSRAM_BUFFER_SIZE 65536u
#define MAPPER_SUNRISE_USB        10
#define MAPPER_SUNRISE_MAPPER_USB 11
#define MAPPER_SYSTEM             MAPPER_SUNRISE_USB
#define MAPPER_SUNRISE_SD         15
#define MAPPER_SUNRISE_MAPPER_SD  16
#define MAPPER_C2_SD              17
#define MAPPER_C2_USB             18
#define MAPPER_MEGARAM_SD         19
#define MAPPER_MEGARAM_USB        20
#define MAPPER_MEGARAM            21

static const char *MAPPER_DESCRIPTIONS[] = {
    "PLA-16", "PLA-32", "KonSCC", "PLN-48", "ASC-08",
    "ASC-16", "Konami", "NEO-8", "NEO-16", "SYSTEM",
    "SYSTEM", "ASC16X", "PLN-64", "MANBW2"
};

#define MAPPER_DESCRIPTION_COUNT (sizeof(MAPPER_DESCRIPTIONS) / sizeof(MAPPER_DESCRIPTIONS[0]))

static char sd_path_buffer[SD_PATH_BUFFER_SIZE];
static uint16_t sd_path_offsets[MAX_ROM_RECORDS];
static uint16_t sd_path_buffer_used = 0;
static uint16_t sd_record_count = 0;
static bool sd_mounted = false;
static uint8_t sd_mounted_partition = 0;
static uint8_t sd_browse_partition = 0;
static bool sd_config_loaded = false;
static sd_card_t *sd_card = NULL;
static uint16_t total_record_count = 0;
static uint16_t full_record_count = 0;
static uint8_t current_page = 0;
static uint16_t filtered_indices[MAX_ROM_RECORDS];
static char filter_query[CTRL_QUERY_SIZE];
static volatile uint8_t ctrl_cmd_state = 0;
static volatile uint8_t ctrl_mapper_value = 0;
static volatile uint8_t ctrl_ack_value = 0;
static uint16_t match_index = 0xFFFF;
static ROMRecord flash_records[MAX_FLASH_RECORDS];
static uint16_t flash_record_count = 0;
static char sd_current_path[SD_PATH_MAX] = "/";
static uint8_t browse_source_mode = SOURCE_MODE_FLASH;
static uint8_t ctrl_status_value = CTRL_MAGIC;
static volatile bool refresh_requested = false;
static volatile bool refresh_in_progress = false;
static bool refresh_worker_started = false;
static volatile bool detect_mapper_pending = false;

// Chunked directory scan state machine (yields back to MP3 loop between chunks)
#define REFRESH_CHUNK_SIZE 8
typedef enum {
    REFRESH_IDLE = 0,
    REFRESH_INIT,
    REFRESH_SCAN_FOLDERS,
    REFRESH_SORT_FOLDERS,
    REFRESH_SCAN_FILES,
    REFRESH_FINALIZE
} refresh_state_t;
static refresh_state_t refresh_state = REFRESH_IDLE;
static DIR refresh_dir;
static uint16_t refresh_record_index = 0;
static uint16_t refresh_folder_count = 0;
static bool refresh_has_parent = false;
static volatile uint16_t detect_mapper_index = 0;
static volatile uint16_t mp3_selected_index = 0;
static volatile bool mp3_pending_select = false;
static volatile uint16_t mp3_pending_index = 0;
static volatile uint8_t mp3_pending_cmd = 0;
static volatile uint8_t mp3_play_mode = MP3_PLAY_MODE_SINGLE;
static uint16_t mp3_playing_filtered_index = 0xFFFF;
static volatile uint8_t ctrl_audio_selection = AUDIO_PROFILE_NONE;
static volatile uint8_t ctrl_wifi_support = 0; // 0=disabled, 1=enabled for Sunrise Nextor launches
static volatile uint8_t ctrl_psg_emulation = 0; // 0=disabled, 1=primary PSG over I2S
static volatile uint8_t ctrl_wavegame_rom = 0; // 0=normal ROM, 1=WAVEGAME sidecars detected
static volatile uint8_t ctrl_sd_partition = 0; // 0=auto/default, 1-4=MBR primary partition
static volatile uint8_t ctrl_audio_volume = AUDIO_VOLUME_DEFAULT; // per-ROM audio volume percent
static volatile uint8_t ctrl_vdp_frequency = VDP_FREQ_DEFAULT; // per-ROM VDP 50/60Hz option (0=default,1=60,2=50)
static volatile uint8_t vdp_freq_launch = VDP_FREQ_DEFAULT; // 50/60Hz to inject into the launched game's INIT (regular game mappers only)
static uint8_t ctrl_sd_partition_info[CTRL_SD_PARTITION_INFO_SIZE];
static char pico_chip_id[CTRL_CHIP_ID_SIZE] = "0000000000000000";
static bool wavegame_active = false;
static bool wavegame_psg_mirror_active = false;
static char wavegame_dir[SD_PATH_MAX];
static bool wavegame_defer_next = false;
static bool wavegame_deferred_valid = false;
static uint8_t wavegame_deferred_data = 0;

static uint8_t fh_page_index = 0;
static uint8_t fh_status = FH_STATUS_READY;
static uint8_t fh_result = 0;
static uint16_t fh_progress_percent = 0;
static uint8_t fh_query[FH_QUERY_SIZE];
static uint16_t fh_selected_index = 0;
static char fh_wifi_status_text[FH_STATUS_TEXT_SIZE];
static uint8_t fh_tcp_last_error = 0;
static uint32_t fh_download_size = 0;
static char fh_download_name[ROM_NAME_MAX + 1];

#define FH_SAVE_IDLE 0u
#define FH_SAVE_RUNNING 1u
#define FH_SAVE_DONE 2u
#define FH_SAVE_FAILED 3u

static uint8_t fh_sd_save_chunk[1024];
static volatile uint8_t fh_save_state = FH_SAVE_IDLE;
static FIL fh_save_file;
static uint32_t fh_save_offset = 0;
static bool fh_save_file_open = false;
static bool fh_save_close_pending = false;
static FILINFO fh_download_timestamp;
static volatile bool fh_menu_window_active = false;
static volatile bool fh_service_menu_window = false;

typedef struct {
    char name[ROM_NAME_MAX + 1];
    uint16_t size_kb;
} fh_catalog_record_t;

static fh_catalog_record_t fh_catalog[FH_MAX_RESULTS];
static uint16_t fh_catalog_count = 0;
static bool fh_catalog_loaded = false;
static bool fh_catalog_message = false;
static bool fh_network_verified = false;
static uint8_t fh_tcp_buffer[FH_HTTP_CHUNK_SIZE + 2u];
static char fh_active_query[FH_QUERY_SIZE];

// SCC emulation state + I2S audio
#define SCC_VOLUME_SHIFT 2  // Left-shift SCC output for volume boost (4x)
#define SCC_AUDIO_BUFFER_SAMPLES 256
static SCC scc_instance;
static struct audio_buffer_pool *scc_audio_pool;
static bool scc_audio_started = false;
static struct audio_buffer_pool *rom_audio_handoff_pool;

static PSG psg_instance;
static spin_lock_t *dual_psg_lock = NULL;
static struct audio_buffer_pool *dual_psg_audio_pool;
static bool dual_psg_ready = false;
static bool dual_psg_audio_started = false;
static bool dual_psg_core1_services_io = true;

static PSG main_psg_instance;
static spin_lock_t *main_psg_lock = NULL;
static struct audio_buffer_pool *main_psg_audio_pool;
static bool main_psg_ready = false;
static bool main_psg_audio_started = false;
static bool main_psg_core1_services_io = true;

// Lock-free single-producer/single-consumer ring used when core0 owns the MSX
// I/O write FIFO (Sunrise mapper mode). core0 pushes primary-PSG port writes
// here without taking main_psg_lock so it can never stall and drop the mapper
// segment-register writes (0xFC-0xFF) that share the lossy I/O capture FIFO.
// core1 drains the ring and applies the PSG writes while producing audio.
#define MAIN_PSG_WRITE_RING_SIZE 256u
#define MAIN_PSG_WRITE_RING_MASK (MAIN_PSG_WRITE_RING_SIZE - 1u)
static volatile uint16_t main_psg_write_ring[MAIN_PSG_WRITE_RING_SIZE];
static volatile uint32_t main_psg_write_ring_head; // written by producer (core0)
static volatile uint32_t main_psg_write_ring_tail; // written by consumer (core1)

// Same decoupling for the secondary (Dual PSG) and MSX-MUSIC (YM2413) audio
// register writes: in Sunrise mapper mode core0 must never block on an audio
// spinlock while it owns the lossy MSX I/O write FIFO, otherwise queued mapper
// segment writes (0xFC-0xFF) get dropped. core0 enqueues these chip writes and
// core1 applies them next to audio generation.
#define DUAL_PSG_WRITE_RING_SIZE 256u
#define DUAL_PSG_WRITE_RING_MASK (DUAL_PSG_WRITE_RING_SIZE - 1u)
static volatile uint16_t dual_psg_write_ring[DUAL_PSG_WRITE_RING_SIZE];
static volatile uint32_t dual_psg_write_ring_head; // written by producer (core0)
static volatile uint32_t dual_psg_write_ring_tail; // written by consumer (core1)

#define MSX_MUSIC_WRITE_RING_SIZE 256u
#define MSX_MUSIC_WRITE_RING_MASK (MSX_MUSIC_WRITE_RING_SIZE - 1u)
static volatile uint16_t msx_music_write_ring[MSX_MUSIC_WRITE_RING_SIZE];
static volatile uint32_t msx_music_write_ring_head; // written by producer (core0)
static volatile uint32_t msx_music_write_ring_tail; // written by consumer (core1)

typedef enum {
    SYSTEM_AUDIO_PROFILE_NONE = 0,
    SYSTEM_AUDIO_PROFILE_MAIN_PSG,
    SYSTEM_AUDIO_PROFILE_DUAL_PSG,
    SYSTEM_AUDIO_PROFILE_MSX_MUSIC,
    SYSTEM_AUDIO_PROFILE_YM2151_SFG05,
    SYSTEM_AUDIO_PROFILE_YM2151_SFG01,
    SYSTEM_AUDIO_PROFILE_SCC_EXTERNAL,
    SYSTEM_AUDIO_PROFILE_SCC_PLUS_EXTERNAL,
} system_audio_profile_t;

static system_audio_profile_t system_audio_profile = SYSTEM_AUDIO_PROFILE_NONE;

static OPLL *msx_music_instance = NULL;
static spin_lock_t *msx_music_lock = NULL;
static struct audio_buffer_pool *msx_music_audio_pool;
static bool msx_music_ready = false;
static bool msx_music_audio_started = false;
static bool msx_music_core1_services_io = true;

typedef enum {
    YM2151_SFG05 = 0,
    YM2151_SFG01 = 1,
} ym2151_sfg_variant_t;

static opm_t ym2151_instance;
static spin_lock_t *ym2151_lock = NULL;
static struct audio_buffer_pool *ym2151_audio_pool;
static bool ym2151_ready = false;
static bool ym2151_audio_started = false;
static uint32_t ym2151_clock_accum = 0;
static int32_t ym2151_last_output[2] = {0, 0};
static volatile uint8_t ym2151_status_latch = 0;
static uint8_t ym2151_address_latch = 0;
static uint8_t ym2151_write_queue_reg[YM2151_WRITE_QUEUE_SIZE];
static uint8_t ym2151_write_queue_data[YM2151_WRITE_QUEUE_SIZE];
static uint16_t ym2151_write_queue_head = 0;
static uint16_t ym2151_write_queue_tail = 0;
static bool ym2151_write_queue_overflow = false;
static uint8_t ym2151_irq_vector = 0xFFu;
static uint8_t ym2151_midi_irq_vector = 0xFFu;
static uint8_t ym2151_midi_status = 0x03u;

static void msx_music_init(void);
static void msx_music_audio_init(void);
static inline void __not_in_flash_func(msx_music_write_io)(uint8_t port, uint8_t data);
static void i2s_audio_init_scc(void);
static void scc_audio_init_for_type(uint32_t scc_type);
static inline void __not_in_flash_func(scc_audio_service_buffer)(void);
static inline void __not_in_flash_func(msx_music_service_io)(void);
static inline void __not_in_flash_func(msx_music_write_stereo_sample)(int16_t *samples, int index);
static inline void __not_in_flash_func(msx_music_audio_service_buffer)(void);
static void ym2151_init(ym2151_sfg_variant_t variant);
static void ym2151_audio_init(void);
static inline void __not_in_flash_func(ym2151_audio_service_buffer)(bool service_psg_io);
static void start_ym2151_audio_output(void);
static inline bool __not_in_flash_func(pio_try_get_io_write)(uint16_t *addr_out, uint8_t *data_out);
static inline bool __not_in_flash_func(external_scc_read)(uint16_t addr, uint8_t *data);
static inline bool __not_in_flash_func(megaram_scc_audio_selected)(void);
static inline uint32_t __not_in_flash_func(megaram_scc_type_selected)(void);
static inline bool __not_in_flash_func(megaram_scc_write)(uint16_t addr, uint8_t data);
static inline bool __not_in_flash_func(megaram_scc_read)(uint16_t addr, uint8_t *data);
static inline void __not_in_flash_func(sfg_write)(uint16_t addr, uint8_t data);
static inline bool __not_in_flash_func(sfg_read)(const uint8_t *bios_base, uint16_t addr, uint8_t *data);

static struct audio_buffer_pool *claim_rom_audio_handoff_pool(void)
{
    struct audio_buffer_pool *pool = rom_audio_handoff_pool;
    rom_audio_handoff_pool = NULL;
    debug_trace("DBG claim_pool pool=%p", (void *)pool);
    if (pool)
    {
        debug_trace("DBG claim_pool i2s off/on");
        audio_i2s_set_enabled(false);
        audio_i2s_set_enabled(true);
        gpio_put(I2S_MUTE_PIN, 0);
    }
    return pool;
}

typedef enum {
    AUDIO_MODE_NONE = 0,
    AUDIO_MODE_SCC,
    AUDIO_MODE_SCC_PLUS,
    AUDIO_MODE_SCC_EXTERNAL,
    AUDIO_MODE_SCC_PLUS_EXTERNAL,
    AUDIO_MODE_MEGARAM_SCC,
    AUDIO_MODE_MEGARAM_SCC_PLUS,
    AUDIO_MODE_DUAL_PSG,
    AUDIO_MODE_MSX_MUSIC,
    AUDIO_MODE_YM2151_SFG05,
    AUDIO_MODE_YM2151_SFG01,
} audio_mode_t;

static const char *EXCLUDED_SD_FOLDERS[] = {
    "System Volume Information"
};
static const size_t EXCLUDED_SD_FOLDER_COUNT = sizeof(EXCLUDED_SD_FOLDERS) / sizeof(EXCLUDED_SD_FOLDERS[0]);

static void write_u32_le(uint8_t *ptr, uint32_t value);
static void write_u16_le(uint8_t *ptr, uint16_t value);
static void build_page_buffer(uint8_t page_index);
static void refresh_records_for_current_path(void);
static bool sd_mount_card(void);
static void sd_unmount_card(void);
static void cancel_refresh_work(void);
static void process_cycle_sd_partition_request(void);
static void process_delete_sd_file_request(void);
static void process_detect_mapper_request(uint16_t filtered_index);
static void quiesce_mp3_core1_before_sd_work(void);

static bool is_system_mapper(uint8_t mapper) {
    return mapper == MAPPER_SUNRISE_USB ||
           mapper == MAPPER_SUNRISE_MAPPER_USB ||
           mapper == MAPPER_SUNRISE_SD ||
           mapper == MAPPER_SUNRISE_MAPPER_SD ||
           mapper == MAPPER_C2_SD ||
           mapper == MAPPER_C2_USB ||
           mapper == MAPPER_MEGARAM_SD ||
           mapper == MAPPER_MEGARAM_USB ||
           mapper == MAPPER_MEGARAM;
}

static bool is_sunrise_sd_mapper(uint8_t mapper) {
    return mapper == MAPPER_SUNRISE_SD || mapper == MAPPER_SUNRISE_MAPPER_SD ||
           mapper == MAPPER_C2_SD || mapper == MAPPER_MEGARAM_SD;
}

static bool is_megaram_mapper(uint8_t mapper) {
    return mapper == MAPPER_MEGARAM_SD || mapper == MAPPER_MEGARAM_USB || mapper == MAPPER_MEGARAM;
}

static bool is_audio_system_mapper(uint8_t mapper) {
    return mapper == 9u || is_system_mapper(mapper);
}

static bool mapper_supports_scc_audio(uint8_t mapper) {
    return mapper == 3u || mapper == 14u;
}

static audio_mode_t resolve_audio_mode(uint8_t mapper, uint8_t requested_profile) {
    if (is_system_mapper(mapper)) {
        if (is_megaram_mapper(mapper)) {
            if (requested_profile == AUDIO_PROFILE_MEGARAM_SCC_PLUS)
                return AUDIO_MODE_MEGARAM_SCC_PLUS;
            if (requested_profile == AUDIO_PROFILE_MEGARAM_SCC)
                return AUDIO_MODE_MEGARAM_SCC;
            return AUDIO_MODE_NONE;
        }
        if (requested_profile == AUDIO_PROFILE_SCC_PLUS_EXTERNAL)
            return AUDIO_MODE_SCC_PLUS_EXTERNAL;
        if (requested_profile == AUDIO_PROFILE_SCC_EXTERNAL)
            return AUDIO_MODE_SCC_EXTERNAL;
        if (requested_profile == AUDIO_PROFILE_DUAL_PSG)
            return AUDIO_MODE_DUAL_PSG;
        if (requested_profile == AUDIO_PROFILE_MSX_MUSIC &&
            mapper != MAPPER_SUNRISE_MAPPER_USB && mapper != MAPPER_SUNRISE_MAPPER_SD &&
            mapper != MAPPER_C2_SD && mapper != MAPPER_C2_USB &&
            mapper != MAPPER_MEGARAM_SD && mapper != MAPPER_MEGARAM_USB)
            return AUDIO_MODE_MSX_MUSIC; // YM2413/FM-PAC only for non-mapper Sunrise Nextor options
        if (requested_profile == AUDIO_PROFILE_YM2151_SFG05)
            return AUDIO_MODE_YM2151_SFG05;
        if (requested_profile == AUDIO_PROFILE_YM2151_SFG01)
            return AUDIO_MODE_YM2151_SFG01;
        return AUDIO_MODE_NONE;
    }
    if (requested_profile == AUDIO_PROFILE_SCC_PLUS_EXTERNAL) {
        return AUDIO_MODE_SCC_PLUS_EXTERNAL;
    }
    if (requested_profile == AUDIO_PROFILE_SCC_EXTERNAL) {
        return AUDIO_MODE_SCC_EXTERNAL;
    }
    if (requested_profile == AUDIO_PROFILE_YM2151_SFG05) {
        return AUDIO_MODE_YM2151_SFG05;
    }
    if (requested_profile == AUDIO_PROFILE_YM2151_SFG01) {
        return AUDIO_MODE_YM2151_SFG01;
    }
    if (is_audio_system_mapper(mapper)) {
        return AUDIO_MODE_NONE;
    }
    if (requested_profile == AUDIO_PROFILE_MSX_MUSIC) {
        return AUDIO_MODE_MSX_MUSIC;
    }
    if (mapper_supports_scc_audio(mapper)) {
        if (requested_profile == AUDIO_PROFILE_SCC_PLUS) {
            return AUDIO_MODE_SCC_PLUS;
        }
        if (requested_profile == AUDIO_PROFILE_SCC) {
            return AUDIO_MODE_SCC;
        }
        return AUDIO_MODE_NONE;
    }
    if (requested_profile == AUDIO_PROFILE_DUAL_PSG) {
        return AUDIO_MODE_DUAL_PSG;
    }
    return AUDIO_MODE_NONE;
}

static uint8_t mapper_code_from_record_byte(uint8_t mapper) {
    return (uint8_t)(mapper & ~(SOURCE_SD_FLAG | FOLDER_FLAG | MP3_FLAG));
}

static int compare_record_names(const ROMRecord *a, const ROMRecord *b) {
    return strncmp(a->Name, b->Name, ROM_NAME_MAX);
}

static bool is_system_record(const ROMRecord *record) {
    return is_system_mapper(mapper_code_from_record_byte(record->Mapper));
}

static bool is_folder_record(const ROMRecord *record) {
    return (record->Mapper & FOLDER_FLAG) != 0;
}

static bool record_matches_source_mode(const ROMRecord *record) {
    switch (browse_source_mode) {
        case SOURCE_MODE_FLASH:
            return !is_folder_record(record) && ((record->Mapper & SOURCE_SD_FLAG) == 0);
        case SOURCE_MODE_SD:
            return is_folder_record(record) || ((record->Mapper & SOURCE_SD_FLAG) != 0);
        default:
            return true;
    }
}

static size_t trim_name_copy(char *dest, const char *src) {
    size_t len = 0;
    for (size_t i = 0; i < ROM_NAME_MAX; i++) {
        dest[i] = src[i];
    }
    dest[ROM_NAME_MAX] = '\0';
    len = ROM_NAME_MAX;
    while (len > 0 && dest[len - 1] == ' ') {
        dest[len - 1] = '\0';
        len--;
    }
    return len;
}

static bool contains_ignore_case(const char *text, const char *query) {
    if (!query || query[0] == '\0') {
        return true;
    }
    size_t text_len = strlen(text);
    size_t query_len = strlen(query);
    if (query_len == 0 || query_len > text_len) {
        return false;
    }
    for (size_t i = 0; i + query_len <= text_len; i++) {
        size_t j = 0;
        while (j < query_len) {
            char a = text[i + j];
            char b = query[j];
            if (toupper((unsigned char)a) != toupper((unsigned char)b)) {
                break;
            }
            j++;
        }
        if (j == query_len) {
            return true;
        }
    }
    return false;
}

static void apply_filter(void) {
    total_record_count = 0;
    if (filter_query[0] == '\0') {
        for (uint16_t i = 0; i < full_record_count; i++) {
            if (record_matches_source_mode(&records[i])) {
                filtered_indices[total_record_count++] = i;
            }
        }
        return;
    }

    char name_buf[ROM_NAME_MAX + 1];
    for (uint16_t i = 0; i < full_record_count; i++) {
        if (!record_matches_source_mode(&records[i])) {
            continue;
        }
        trim_name_copy(name_buf, records[i].Name);
        if (contains_ignore_case(name_buf, filter_query)) {
            filtered_indices[total_record_count++] = i;
        }
    }
}

static void find_first_match(void) {
    match_index = 0xFFFF;
    if (filter_query[0] == '\0') {
        return;
    }

    char name_buf[ROM_NAME_MAX + 1];
    for (uint16_t i = 0; i < total_record_count; i++) {
        uint16_t record_index = filtered_indices[i];
        if (record_index >= full_record_count) {
            continue;
        }
        trim_name_copy(name_buf, records[record_index].Name);
        if (contains_ignore_case(name_buf, filter_query)) {
            match_index = i;
            return;
        }
    }
}

static void swap_records(uint16_t a, uint16_t b) {
    if (a == b) {
        return;
    }
    ROMRecord temp = records[a];
    records[a] = records[b];
    records[b] = temp;
    uint16_t path_temp = sd_path_offsets[a];
    sd_path_offsets[a] = sd_path_offsets[b];
    sd_path_offsets[b] = path_temp;
}

static void sort_records_range(uint16_t start, uint16_t count) {
    if (count < 2) {
        return;
    }
    uint16_t end = (uint16_t)(start + count);
    for (uint16_t i = start; i + 1 < end; i++) {
        for (uint16_t j = i + 1; j < end; j++) {
            if (compare_record_names(&records[i], &records[j]) > 0) {
                swap_records(i, j);
            }
        }
    }
}

static void write_config_area(uint8_t *config_area, const ROMRecord *list, uint16_t count) {
    for (uint16_t i = 0; i < count; i++) {
        uint8_t *entry = config_area + (i * ROM_RECORD_SIZE);
        memset(entry, 0xFF, ROM_RECORD_SIZE);
        memset(entry, ' ', ROM_NAME_MAX);
        size_t name_len = strlen(list[i].Name);
        if (name_len > ROM_NAME_MAX) {
            name_len = ROM_NAME_MAX;
        }
        memcpy(entry, list[i].Name, name_len);
        entry[ROM_NAME_MAX] = list[i].Mapper;
        write_u32_le(entry + ROM_NAME_MAX + 1, (uint32_t)list[i].Size);
        write_u32_le(entry + ROM_NAME_MAX + 1 + sizeof(uint32_t), (uint32_t)list[i].Offset);
    }

    if (count < MAX_ROM_RECORDS) {
        memset(config_area + (count * ROM_RECORD_SIZE), 0xFF,
               (MAX_ROM_RECORDS - count) * ROM_RECORD_SIZE);
    }
}

static void build_page_buffer(uint8_t page_index) {
    uint8_t *buffer = page_buffer;
    const uint16_t buffer_size = DATA_BUFFER_SIZE;
    uint16_t start_index = (uint16_t)page_index * FILES_PER_PAGE;
    uint16_t record_count = 0;

    if (start_index < total_record_count) {
        uint16_t remaining = (uint16_t)(total_record_count - start_index);
        record_count = (remaining > FILES_PER_PAGE) ? FILES_PER_PAGE : remaining;
    }

    memset(buffer, 0xFF, buffer_size);

    uint16_t table_offset = DATA_HEADER_SIZE;
    uint16_t table_size = (uint16_t)(record_count * DATA_RECORD_TABLE_ENTRY_SIZE);
    uint16_t payload_size = (uint16_t)(record_count * DATA_RECORD_PAYLOAD_SIZE);
    uint16_t string_pool_offset = (uint16_t)(table_offset + table_size);
    uint16_t max_string_pool = 0;
    if ((uint32_t)string_pool_offset + payload_size <= buffer_size) {
        max_string_pool = (uint16_t)(buffer_size - (string_pool_offset + payload_size));
    }

    uint16_t name_offsets[FILES_PER_PAGE];
    uint16_t string_cursor = 0;
    uint16_t max_name_bytes = record_count ? (uint16_t)(max_string_pool / record_count) : 0;
    for (uint16_t i = 0; i < record_count; i++) {
        uint16_t filtered_index = (uint16_t)(start_index + i);
        uint16_t record_index = filtered_indices[filtered_index];
        char name_buf[ROM_NAME_MAX + 1];
        size_t name_len = trim_name_copy(name_buf, records[record_index].Name);
        if (max_name_bytes != 0u && name_len + 1u > max_name_bytes) {
            name_len = max_name_bytes - 1u;
            name_buf[name_len] = '\0';
        }
        if (name_len + 1 <= (size_t)(max_string_pool - string_cursor)) {
            name_offsets[i] = string_cursor;
            memcpy(buffer + string_pool_offset + string_cursor, name_buf, name_len);
            buffer[string_pool_offset + string_cursor + name_len] = '\0';
            string_cursor = (uint16_t)(string_cursor + name_len + 1);
        } else {
            name_offsets[i] = 0xFFFF;
        }
    }

    uint16_t string_pool_size = string_cursor;
    uint16_t payload_offset = (uint16_t)(string_pool_offset + string_pool_size);
    uint16_t payload_cursor = 0;

    for (uint16_t i = 0; i < record_count; i++) {
        uint16_t filtered_index = (uint16_t)(start_index + i);
        uint16_t record_index = filtered_indices[filtered_index];
        uint8_t *entry = buffer + table_offset + (i * DATA_RECORD_TABLE_ENTRY_SIZE);
        uint16_t record_offset = (uint16_t)(payload_offset + payload_cursor);
        uint16_t record_length = DATA_RECORD_PAYLOAD_SIZE;

        write_u16_le(entry, record_offset);
        write_u16_le(entry + 2, record_length);

        uint8_t *rec = buffer + record_offset;
        rec[0] = TLV_NAME_OFFSET;
        rec[1] = 2;
        write_u16_le(rec + 2, name_offsets[i]);
        rec[4] = TLV_MAPPER;
        rec[5] = 1;
        rec[6] = records[record_index].Mapper;
        rec[7] = TLV_SIZE;
        rec[8] = 4;
        write_u32_le(rec + 9, (uint32_t)records[record_index].Size);

        payload_cursor = (uint16_t)(payload_cursor + record_length);
    }

    buffer[0] = DATA_MAGIC_0;
    buffer[1] = DATA_MAGIC_1;
    buffer[2] = DATA_MAGIC_2;
    buffer[3] = DATA_MAGIC_3;
    buffer[4] = DATA_VERSION;
    buffer[5] = 0;
    write_u16_le(buffer + 6, DATA_HEADER_SIZE);
    write_u16_le(buffer + 8, total_record_count);
    write_u16_le(buffer + 10, page_index);
    write_u16_le(buffer + 12, record_count);
    write_u16_le(buffer + 14, table_offset);
    write_u16_le(buffer + 16, table_size);
    write_u16_le(buffer + 18, string_pool_offset);
    write_u16_le(buffer + 20, string_pool_size);
    write_u16_le(buffer + 22, payload_offset);
}

static bool equals_ignore_case(const char *a, const char *b) {
    if (!a || !b) {
        return false;
    }
    while (*a && *b) {
        if (toupper((unsigned char)*a) != toupper((unsigned char)*b)) {
            return false;
        }
        ++a;
        ++b;
    }
    return *a == '\0' && *b == '\0';
}

static bool is_excluded_folder(const char *name) {
    if (!name || name[0] == '\0') {
        return true;
    }
    if (equals_ignore_case(name, ".") || equals_ignore_case(name, "..")) {
        return true;
    }
    for (size_t i = 0; i < EXCLUDED_SD_FOLDER_COUNT; i++) {
        if (equals_ignore_case(name, EXCLUDED_SD_FOLDERS[i])) {
            return true;
        }
    }
    return false;
}

static bool is_root_path(const char *path) {
    if (!path || path[0] == '\0') {
        return true;
    }
    if (path[0] == '/' && path[1] == '\0') {
        return true;
    }
    return false;
}

static void set_root_path(void) {
    sd_current_path[0] = '/';
    sd_current_path[1] = '\0';
}

static void go_up_one_level(void) {
    if (is_root_path(sd_current_path)) {
        set_root_path();
        return;
    }

    size_t len = strlen(sd_current_path);
    if (len == 0) {
        set_root_path();
        return;
    }

    while (len > 1 && sd_current_path[len - 1] == '/') {
        sd_current_path[len - 1] = '\0';
        len--;
    }

    char *slash = strrchr(sd_current_path, '/');
    if (!slash || slash == sd_current_path) {
        set_root_path();
    } else {
        *slash = '\0';
    }
}

static void append_folder_to_path(const char *folder) {
    if (!folder || folder[0] == '\0') {
        return;
    }
    if (equals_ignore_case(folder, "..")) {
        go_up_one_level();
        return;
    }

    size_t base_len = strlen(sd_current_path);
    size_t folder_len = strlen(folder);
    if (base_len + folder_len + 2 >= sizeof(sd_current_path)) {
        return;
    }

    if (!is_root_path(sd_current_path)) {
        sd_current_path[base_len] = '/';
        base_len++;
    }
    memcpy(sd_current_path + base_len, folder, folder_len + 1);
}

static void write_u32_le(uint8_t *ptr, uint32_t value) {
    ptr[0] = (uint8_t)(value & 0xFFu);
    ptr[1] = (uint8_t)((value >> 8) & 0xFFu);
    ptr[2] = (uint8_t)((value >> 16) & 0xFFu);
    ptr[3] = (uint8_t)((value >> 24) & 0xFFu);
}

static void write_u16_le(uint8_t *ptr, uint16_t value) {
    ptr[0] = (uint8_t)(value & 0xFFu);
    ptr[1] = (uint8_t)((value >> 8) & 0xFFu);
}

static const char *basename_from_path(const char *path) {
    if (!path) {
        return "";
    }
    const char *slash = strrchr(path, '/');
    return slash ? (slash + 1) : path;
}

static uint8_t mapper_number_from_filename(const char *filename) {
    char name_copy[SD_PATH_MAX];
    strncpy(name_copy, filename, sizeof(name_copy));
    name_copy[sizeof(name_copy) - 1] = '\0';

    char *dot = strrchr(name_copy, '.');
    if (dot) {
        *dot = '\0';
    }

    size_t name_len = strlen(name_copy);
    for (size_t i = 0; i + 1 < MAPPER_DESCRIPTION_COUNT; ++i) {
        const char *tag = MAPPER_DESCRIPTIONS[i];
        size_t tag_len = strlen(tag);
        if (name_len > tag_len + 1 && name_copy[name_len - tag_len - 1] == '.') {
            if (equals_ignore_case(name_copy + name_len - tag_len, tag)) {
                return (uint8_t)(i + 1);
            }
        }
    }
    return 0;
}

static void build_display_name(const char *filename, char *out, size_t out_size) {
    char name_copy[SD_PATH_MAX];
    strncpy(name_copy, filename, sizeof(name_copy));
    name_copy[sizeof(name_copy) - 1] = '\0';

    char *dot = strrchr(name_copy, '.');
    if (dot) {
        *dot = '\0';
    }

    size_t name_len = strlen(name_copy);
    for (size_t i = 0; i + 1 < MAPPER_DESCRIPTION_COUNT; ++i) {
        const char *tag = MAPPER_DESCRIPTIONS[i];
        size_t tag_len = strlen(tag);
        if (name_len > tag_len + 1 && name_copy[name_len - tag_len - 1] == '.') {
            if (equals_ignore_case(name_copy + name_len - tag_len, tag)) {
                name_copy[name_len - tag_len - 1] = '\0';
                break;
            }
        }
    }

    strncpy(out, name_copy, out_size);
    out[out_size - 1] = '\0';
}

static bool has_rom_extension(const char *filename) {
    const char *dot = strrchr(filename, '.');
    if (!dot || dot[1] == '\0') {
        return false;
    }
    return equals_ignore_case(dot + 1, "ROM");
}

static bool has_mp3_extension(const char *filename) {
    const char *dot = strrchr(filename, '.');
    if (!dot || dot[1] == '\0') {
        return false;
    }
    return equals_ignore_case(dot + 1, "MP3");
}

static bool has_wav_extension(const char *filename) {
    const char *dot = strrchr(filename, '.');
    if (!dot || dot[1] == '\0') {
        return false;
    }
    return equals_ignore_case(dot + 1, "WAV");
}

static bool build_pvc_options_path(uint16_t record_index, char *out, size_t out_size) {
    if (!out || out_size == 0 || record_index >= full_record_count) {
        return false;
    }
    ROMRecord *rec = &records[record_index];
    if ((rec->Mapper & (FOLDER_FLAG | MP3_FLAG)) != 0) {
        return false;
    }

    if (mapper_code_from_record_byte(rec->Mapper) == MAPPER_MEGARAM) {
        int written = snprintf(out, out_size, "/%s.flash.PVC", rec->Name);
        return written > 0 && (size_t)written < out_size;
    }

    if ((rec->Mapper & SOURCE_SD_FLAG) != 0) {
        if (sd_path_offsets[record_index] == 0xFFFF) {
            return false;
        }
        const char *rom_path = sd_path_buffer + sd_path_offsets[record_index];
        size_t len = strlen(rom_path);
        if (len + 1 > out_size) {
            return false;
        }
        memcpy(out, rom_path, len + 1);
        char *slash = strrchr(out, '/');
        char *dot = strrchr(out, '.');
        if (!dot || (slash && dot < slash)) {
            dot = out + len;
        }
        if ((size_t)(dot - out) + 5u > out_size) {
            return false;
        }
        memcpy(dot, ".PVC", 5u);
        return true;
    }

    int written = snprintf(out, out_size, "/%s.flash.PVC", rec->Name);
    return written > 0 && (size_t)written < out_size;
}

static uint16_t query_filtered_index(void) {
    return (uint16_t)((uint8_t)filter_query[0]) |
           (uint16_t)(((uint8_t)filter_query[1]) << 8);
}

static void process_enter_dir_request(void) {
    filter_query[CTRL_QUERY_SIZE - 1] = '\0';
    if ((uint8_t)filter_query[2] == CTRL_MAGIC) {
        uint16_t filtered_index = query_filtered_index();
        if (filtered_index < total_record_count) {
            uint16_t record_index = filtered_indices[filtered_index];
            if (record_index < full_record_count && (records[record_index].Mapper & FOLDER_FLAG)) {
                append_folder_to_path(records[record_index].Name);
            }
        }
    } else if (filter_query[0] == '\0') {
        go_up_one_level();
    } else {
        append_folder_to_path(filter_query);
    }
    refresh_requested = true;
}

static void cancel_refresh_work(void) {
    if (refresh_state == REFRESH_SCAN_FOLDERS || refresh_state == REFRESH_SCAN_FILES) {
        f_closedir(&refresh_dir);
    }
    refresh_state = REFRESH_IDLE;
    refresh_in_progress = false;
    refresh_requested = false;
}

static bool wavegame_assets_detected_for_record(uint16_t record_index);

static void set_sunrise_partition_text(const char *text) {
    size_t len = text ? strlen(text) : 0;
    if (len > CTRL_SD_PARTITION_INFO_SIZE - 3u) {
        len = CTRL_SD_PARTITION_INFO_SIZE - 3u;
    }
    memset(ctrl_sd_partition_info + 2, 0, CTRL_SD_PARTITION_INFO_SIZE - 2u);
    if (len) memcpy(ctrl_sd_partition_info + 2, text, len);
}

static void update_sunrise_partition_text(const sunrise_sd_partition_t *parts, uint8_t part_count) {
    if (part_count == 0) {
        set_sunrise_partition_text("NO FAT16 PARTITION AVAILABLE");
        return;
    }
    for (uint8_t i = 0; i < part_count; i++) {
        if (parts[i].number == ctrl_sd_partition) {
            if (parts[i].label[0]) {
                set_sunrise_partition_text(parts[i].label);
            } else {
                char fallback[16];
                snprintf(fallback, sizeof(fallback), "PARTITION%u", parts[i].number);
                set_sunrise_partition_text(fallback);
            }
            return;
        }
    }
    set_sunrise_partition_text("PARTITION");
}

static bool read_mounted_partition_free_mb(uint8_t selected_partition, uint32_t *free_mb) {
    if (!free_mb || !sd_mounted || sd_mounted_partition != selected_partition) {
        return false;
    }

    DWORD free_clusters = 0;
    FATFS *fatfs = NULL;
    if (f_getfree("", &free_clusters, &fatfs) != FR_OK || !fatfs || fatfs->csize == 0) {
        return false;
    }

    uint64_t mb = ((uint64_t)free_clusters * (uint64_t)fatfs->csize) / 2048u;
    *free_mb = (mb > UINT32_MAX) ? UINT32_MAX : (uint32_t)mb;
    return true;
}

static void set_browse_partition_status_text(const char *label, uint8_t selected_partition) {
    uint32_t free_mb = 0;
    if (!read_mounted_partition_free_mb(selected_partition, &free_mb)) {
        set_sunrise_partition_text(label);
        return;
    }

    char suffix[24];
    char text[CTRL_SD_PARTITION_INFO_SIZE - 2u];
    snprintf(suffix, sizeof(suffix), " (%luMB FREE)", (unsigned long)free_mb);

    size_t max_len = CTRL_SD_PARTITION_INFO_SIZE - 3u;
    size_t label_len = strlen(label);
    size_t suffix_len = strlen(suffix);
    if (suffix_len < max_len && label_len > max_len - suffix_len) {
        label_len = max_len - suffix_len;
    }

    memcpy(text, label, label_len);
    memcpy(text + label_len, suffix, suffix_len + 1u);
    set_sunrise_partition_text(text);
}

static void update_browse_partition_text(const sunrise_sd_partition_t *parts, uint8_t part_count, uint8_t selected_partition) {
    if (part_count == 0) {
        set_sunrise_partition_text("");
        return;
    }
    for (uint8_t i = 0; i < part_count; i++) {
        if (parts[i].number == selected_partition) {
            if (parts[i].label[0]) {
                set_browse_partition_status_text(parts[i].label, selected_partition);
            } else {
                char fallback[16];
                snprintf(fallback, sizeof(fallback), "PARTITION%u", parts[i].number);
                set_browse_partition_status_text(fallback, selected_partition);
            }
            return;
        }
    }
    set_sunrise_partition_text("PARTITION");
}

static void refresh_browse_partition_text(void) {
    sunrise_sd_partition_t parts[SD_BROWSE_PARTITION_MAX];
    uint8_t count = sunrise_sd_list_supported_partitions(parts, SD_BROWSE_PARTITION_MAX);
    if (count) {
        update_browse_partition_text(parts, count, sd_browse_partition ? sd_browse_partition : sd_mounted_partition);
    }
}

static void refresh_sunrise_partition_info(uint8_t selected_partition) {
    memset(ctrl_sd_partition_info, 0, sizeof(ctrl_sd_partition_info));
    ctrl_sd_partition = 0;

    sunrise_sd_partition_t parts[4];
    uint8_t part_count = sunrise_sd_list_fat16_partitions(parts, 4);
    ctrl_sd_partition_info[0] = part_count;

    for (uint8_t i = 0; i < part_count; i++) {
        ctrl_sd_partition_info[1] |= (uint8_t)(1u << (parts[i].number - 1u));
        if (selected_partition == parts[i].number) {
            ctrl_sd_partition = selected_partition;
        }
    }

    if (ctrl_sd_partition == 0 && part_count != 0) {
        ctrl_sd_partition = parts[0].number;
    }
    update_sunrise_partition_text(parts, part_count);
}

static void process_load_options_request(void) {
    ctrl_ack_value = 0;
    ctrl_mapper_value = 0;
    ctrl_wavegame_rom = 0;
    ctrl_audio_selection = AUDIO_PROFILE_NONE;
    ctrl_psg_emulation = 1;
    ctrl_sd_partition = 0;
    ctrl_audio_volume = AUDIO_VOLUME_DEFAULT;
    ctrl_vdp_frequency = VDP_FREQ_DEFAULT;
    memset(ctrl_sd_partition_info, 0, sizeof(ctrl_sd_partition_info));
    quiesce_mp3_core1_before_sd_work();
    if (!sd_mount_card()) {
        return;
    }

    uint16_t index = query_filtered_index();
    if (index >= total_record_count) {
        return;
    }
    uint16_t record_index = filtered_indices[index];
    ROMRecord *rec = &records[record_index];
    bool sunrise_sd_options = is_sunrise_sd_mapper(mapper_code_from_record_byte(rec->Mapper));
    ctrl_wavegame_rom = wavegame_assets_detected_for_record(record_index) ? 1u : 0u;
    if (sunrise_sd_options) {
        refresh_sunrise_partition_info(0);
    }
    char path[SD_PATH_MAX];
    if (!build_pvc_options_path(record_index, path, sizeof(path))) {
        if (sunrise_sd_options) {
            ctrl_ack_value = 1;
        }
        return;
    }

    FIL fil;
    if (f_open(&fil, path, FA_READ) != FR_OK) {
        if (sunrise_sd_options) {
            ctrl_ack_value = 1;
        }
        return;
    }
    uint8_t data[PVC_OPTIONS_SIZE];
    UINT br = 0;
    FRESULT fr = f_read(&fil, data, sizeof(data), &br);
    f_close(&fil);
    if (fr != FR_OK || br < PVC_OPTIONS_LEGACY_SIZE) {
        return;
    }
    if (data[0] != PVC_OPTIONS_MAGIC_0 || data[1] != PVC_OPTIONS_MAGIC_1 ||
        data[2] != PVC_OPTIONS_MAGIC_2 || data[3] != PVC_OPTIONS_MAGIC_3) {
        return;
    }

    ctrl_audio_selection = data[4];
    ctrl_psg_emulation = data[5] ? 1u : 0u;
    if (ctrl_wavegame_rom) {
        ctrl_audio_selection = AUDIO_PROFILE_NONE;
    }
    if (br >= PVC_OPTIONS_MAPPER_SIZE && data[6] != 0 && !is_system_mapper(data[6]) && data[6] < MAPPER_DESCRIPTION_COUNT) {
        uint8_t flags = rec->Mapper & (SOURCE_SD_FLAG | FOLDER_FLAG | MP3_FLAG);
        if ((flags & (FOLDER_FLAG | MP3_FLAG)) == 0) {
            rec->Mapper = (uint8_t)(flags | data[6]);
            ctrl_mapper_value = data[6];
        }
    }
    if (sunrise_sd_options && br >= PVC_OPTIONS_PARTITION_SIZE) {
        refresh_sunrise_partition_info(data[7]);
    }
    if (br >= PVC_OPTIONS_VOLUME_SIZE) {
        ctrl_audio_volume = data[8] <= AUDIO_VOLUME_MAX ? data[8] : AUDIO_VOLUME_DEFAULT;
    }
    if (br >= PVC_OPTIONS_SIZE) {
        ctrl_vdp_frequency = data[9] <= VDP_FREQ_50HZ ? data[9] : VDP_FREQ_DEFAULT;
    }
    ctrl_ack_value = 1;
}

static void process_save_options_request(void) {
    ctrl_ack_value = 0;
    quiesce_mp3_core1_before_sd_work();
    if (!sd_mount_card()) {
        return;
    }

    uint16_t index = query_filtered_index();
    if (index >= total_record_count) {
        return;
    }
    uint16_t record_index = filtered_indices[index];
    uint8_t audio_selection = wavegame_assets_detected_for_record(record_index) ? AUDIO_PROFILE_NONE : (uint8_t)filter_query[2];
    uint8_t sd_partition = (uint8_t)filter_query[5];
    uint8_t audio_volume = (uint8_t)filter_query[6];
    if (audio_volume > AUDIO_VOLUME_MAX) {
        audio_volume = AUDIO_VOLUME_DEFAULT;
    }
    uint8_t vdp_frequency = (uint8_t)filter_query[7];
    if (vdp_frequency > VDP_FREQ_50HZ) {
        vdp_frequency = VDP_FREQ_DEFAULT;
    }
    char path[SD_PATH_MAX];
    if (!build_pvc_options_path(record_index, path, sizeof(path))) {
        return;
    }

    FIL fil;
    if (f_open(&fil, path, FA_CREATE_ALWAYS | FA_WRITE) != FR_OK) {
        return;
    }
    uint8_t data[PVC_OPTIONS_SIZE] = {
        PVC_OPTIONS_MAGIC_0, PVC_OPTIONS_MAGIC_1, PVC_OPTIONS_MAGIC_2, PVC_OPTIONS_MAGIC_3,
        audio_selection, (uint8_t)(filter_query[3] ? 1u : 0u), (uint8_t)filter_query[4], sd_partition,
        audio_volume, vdp_frequency
    };
    UINT written = 0;
    FRESULT fr = f_write(&fil, data, sizeof(data), &written);
    FRESULT close_fr = f_close(&fil);
    if (fr == FR_OK && close_fr == FR_OK && written == sizeof(data)) {
        ctrl_audio_selection = data[4];
        ctrl_psg_emulation = data[5];
        ctrl_mapper_value = data[6];
        ctrl_sd_partition = data[7];
        ctrl_audio_volume = data[8];
        ctrl_vdp_frequency = data[9];
        ctrl_ack_value = 1;
    }
}

static void process_prepare_quick_run_request(void) {
    uint16_t index = query_filtered_index();
    ctrl_ack_value = 0;
    ctrl_mapper_value = 0;
    ctrl_audio_selection = AUDIO_PROFILE_NONE;
    ctrl_psg_emulation = 1;
    ctrl_wifi_support = 0;
    ctrl_wavegame_rom = 0;
    ctrl_audio_volume = AUDIO_VOLUME_DEFAULT;
    ctrl_vdp_frequency = VDP_FREQ_DEFAULT;

    if (index >= total_record_count) {
        return;
    }

    uint16_t record_index = filtered_indices[index];
    if (record_index >= full_record_count) {
        return;
    }

    ROMRecord *rec = &records[record_index];
    uint8_t mapper = mapper_code_from_record_byte(rec->Mapper);
    if (mapper_supports_scc_audio(mapper)) {
        ctrl_audio_selection = AUDIO_PROFILE_SCC;
    }

    process_load_options_request();
    bool options_loaded = (ctrl_ack_value != 0);

    mapper = mapper_code_from_record_byte(rec->Mapper);
    if (mapper == 0) {
        process_detect_mapper_request(index);
        mapper = ctrl_mapper_value;
    } else {
        ctrl_mapper_value = mapper;
    }

    if (!options_loaded) {
        ctrl_audio_selection = mapper_supports_scc_audio(mapper) ? AUDIO_PROFILE_SCC : AUDIO_PROFILE_NONE;
        ctrl_psg_emulation = 1;
    }
    ctrl_wifi_support = 0;
    ctrl_ack_value = 1;
}

// FatFS-backed reader callback for the shared streaming detector.
typedef struct {
    FIL *fil;
    uint32_t cur_offset; // current file pointer (best-effort cache to avoid redundant f_lseek)
    bool failed;
} fatfs_reader_ctx_t;

static uint32_t fatfs_reader_cb(void *user, uint32_t offset, void *buf, uint32_t len) {
    fatfs_reader_ctx_t *ctx = (fatfs_reader_ctx_t *)user;
    if (ctx->failed || !ctx->fil) {
        return 0;
    }
    if (offset != ctx->cur_offset) {
        if (f_lseek(ctx->fil, offset) != FR_OK) {
            ctx->failed = true;
            return 0;
        }
        ctx->cur_offset = offset;
    }
    UINT br = 0;
    if (f_read(ctx->fil, buf, (UINT)len, &br) != FR_OK) {
        ctx->failed = true;
        return 0;
    }
    ctx->cur_offset += br;
    return (uint32_t)br;
}

// Stream a ROM file from the SD card through the shared mapper detector.
// Uses the same SHA1 + heuristic algorithm as the PC tool so that the firmware
// produces identical mapper guesses for ROMs executed straight from microSD.
static uint8_t detect_rom_type_from_file(const char *path, uint32_t size) {
    if (size > MAX_ROM_SIZE || size < MIN_ROM_SIZE) {
        return 0;
    }

    FIL fil;
    FRESULT fr = f_open(&fil, path, FA_READ);
    if (fr != FR_OK) {
        return 0;
    }

    fatfs_reader_ctx_t ctx = { .fil = &fil, .cur_offset = 0, .failed = false };
    uint8_t mapper = mapper_detect_stream(size, fatfs_reader_cb, &ctx);
    f_close(&fil);
    if (ctx.failed) {
        return 0;
    }
    return mapper;
}

static bool sd_prepare_card(void) {
    if (!sd_init_driver()) return false;
    sd_card = sd_get_by_num(0);
    if (!sd_card) return false;
    return disk_initialize(pdrv) == 0;
}

static bool sd_partition_supported(const sunrise_sd_partition_t *parts, uint8_t count, uint8_t number) {
    for (uint8_t i = 0; i < count; i++) {
        if (parts[i].number == number) return true;
    }
    return false;
}

static int sd_find_partition_index(const sunrise_sd_partition_t *parts, uint8_t count, uint8_t number) {
    for (uint8_t i = 0; i < count; i++) {
        if (parts[i].number == number) return (int)i;
    }
    return -1;
}

static void sd_unmount_card(void) {
    if (sd_mounted) {
        f_mount(NULL, "", 0);
    }
    sd_mounted = false;
    sd_mounted_partition = 0;
    disk_set_partition_window(0, 0);
}

static bool sd_mount_partition(const sunrise_sd_partition_t *parts, uint8_t count, uint8_t number) {
    int index = sd_find_partition_index(parts, count, number);
    if (index < 0) return false;

    sd_unmount_card();
    disk_set_partition_window((LBA_t)parts[index].start_lba, (LBA_t)parts[index].sector_count);
    FRESULT fr = f_mount(&sd_card->state.fatfs, "", 1);
    if (fr != FR_OK) {
        sd_unmount_card();
        return false;
    }
    sd_mounted = true;
    sd_mounted_partition = parts[index].number;
    return true;
}

static uint8_t sd_load_saved_browse_partition(const sunrise_sd_partition_t *parts, uint8_t count) {
    uint8_t selected = count ? parts[0].number : 0;
    if (!count || !sd_mount_partition(parts, count, parts[0].number)) return selected;

    FIL fil;
    if (f_open(&fil, PV_CONFIG_PATH, FA_READ) == FR_OK) {
        uint8_t data[PV_CONFIG_SIZE];
        UINT br = 0;
        if (f_read(&fil, data, sizeof(data), &br) == FR_OK && br == sizeof(data) &&
            data[0] == PV_CONFIG_MAGIC_0 && data[1] == PV_CONFIG_MAGIC_1 &&
            data[2] == PV_CONFIG_MAGIC_2 && data[3] == PV_CONFIG_MAGIC_3 &&
            sd_partition_supported(parts, count, data[4])) {
            selected = data[4];
        }
        f_close(&fil);
    }
    sd_unmount_card();
    return selected;
}

static void sd_save_browse_partition(uint8_t selected) {
    sunrise_sd_partition_t parts[SD_BROWSE_PARTITION_MAX];
    uint8_t count = sunrise_sd_list_supported_partitions(parts, SD_BROWSE_PARTITION_MAX);
    if (!count || !sd_mount_partition(parts, count, parts[0].number)) return;

    FIL fil;
    if (f_open(&fil, PV_CONFIG_PATH, FA_CREATE_ALWAYS | FA_WRITE) == FR_OK) {
        uint8_t data[PV_CONFIG_SIZE] = {
            PV_CONFIG_MAGIC_0, PV_CONFIG_MAGIC_1, PV_CONFIG_MAGIC_2, PV_CONFIG_MAGIC_3, selected
        };
        UINT written = 0;
        (void)f_write(&fil, data, sizeof(data), &written);
        f_close(&fil);
    }
    sd_unmount_card();
}

static bool sd_mount_card(void) {
    if (sd_mounted) {
        refresh_browse_partition_text();
        return true;
    }
    if (!sd_prepare_card()) return false;

    sunrise_sd_partition_t parts[SD_BROWSE_PARTITION_MAX];
    uint8_t count = sunrise_sd_list_supported_partitions(parts, SD_BROWSE_PARTITION_MAX);
    if (!count) return false;

    if (!sd_config_loaded) {
        sd_browse_partition = sd_load_saved_browse_partition(parts, count);
        sd_config_loaded = true;
    }
    if (!sd_partition_supported(parts, count, sd_browse_partition)) {
        sd_browse_partition = parts[0].number;
    }
    if (!sd_mount_partition(parts, count, sd_browse_partition)) return false;
    sd_browse_partition = sd_mounted_partition;
    update_browse_partition_text(parts, count, sd_browse_partition);
    return true;
}

static void process_cycle_sd_partition_request(void) {
    ctrl_ack_value = 0;
    cancel_refresh_work();
    if (!sd_prepare_card()) return;

    sunrise_sd_partition_t parts[SD_BROWSE_PARTITION_MAX];
    uint8_t count = sunrise_sd_list_supported_partitions(parts, SD_BROWSE_PARTITION_MAX);
    if (!count) return;

    int index = sd_find_partition_index(parts, count, sd_browse_partition ? sd_browse_partition : sd_mounted_partition);
    index++;
    if ((uint8_t)index >= count) index = 0;

    sd_browse_partition = parts[index].number;
    sd_save_browse_partition(sd_browse_partition);
    sd_unmount_card();
    (void)sd_mount_card();
    set_root_path();
    browse_source_mode = SOURCE_MODE_SD;
    fh_menu_window_active = false;
    memset(filter_query, 0, sizeof(filter_query));
    refresh_requested = true;
    ctrl_ack_value = 1;
}

static void process_delete_sd_file_request(void) {
    ctrl_ack_value = 0;
    cancel_refresh_work();
    if (!sd_mount_card()) {
        ctrl_cmd_state = 0;
        return;
    }

    uint16_t index = query_filtered_index();
    if (index >= total_record_count) {
        ctrl_cmd_state = 0;
        return;
    }

    uint16_t record_index = filtered_indices[index];
    if (record_index >= full_record_count || sd_path_offsets[record_index] == 0xFFFF) {
        ctrl_cmd_state = 0;
        return;
    }

    ROMRecord *rec = &records[record_index];
    if ((rec->Mapper & SOURCE_SD_FLAG) == 0 || (rec->Mapper & FOLDER_FLAG) != 0) {
        ctrl_cmd_state = 0;
        return;
    }

    char pvc_path[SD_PATH_MAX];
    bool has_pvc_path = build_pvc_options_path(record_index, pvc_path, sizeof(pvc_path));
    if (f_unlink(sd_path_buffer + sd_path_offsets[record_index]) == FR_OK) {
        refresh_requested = true;
        FRESULT pvc_result = has_pvc_path ? f_unlink(pvc_path) : FR_NO_FILE;
        if (pvc_result == FR_OK || pvc_result == FR_NO_FILE || pvc_result == FR_NO_PATH) {
            ctrl_ack_value = 1;
        } else {
            ctrl_cmd_state = 0;
        }
    } else {
        ctrl_cmd_state = 0;
    }
}

static bool sd_is_mounted(void) {
    return sd_mounted && sd_card != NULL;
}

static uint16_t add_folder_record(uint16_t record_index, const char *name) {
    if (record_index >= MAX_ROM_RECORDS) {
        return record_index;
    }
    memset(records[record_index].Name, 0, sizeof(records[record_index].Name));
    strncpy(records[record_index].Name, name, sizeof(records[record_index].Name) - 1);
    records[record_index].Mapper = (unsigned char)(FOLDER_FLAG | SOURCE_SD_FLAG);
    records[record_index].Size = 0;
    records[record_index].Offset = 0;
    sd_path_offsets[record_index] = 0xFFFF;
    return (uint16_t)(record_index + 1);
}

static bool wavegame_asset_exists_in_dir(const char *dir, const char *name) {
    char path[SD_PATH_MAX];
    int written;
    if (!dir || !name || dir[0] == '\0') {
        return false;
    }
    if (strcmp(dir, "/") == 0) {
        written = snprintf(path, sizeof(path), "/%s", name);
    } else {
        written = snprintf(path, sizeof(path), "%s/%s", dir, name);
    }
    if (written <= 0 || (size_t)written >= sizeof(path)) {
        return false;
    }
    FILINFO info;
    return f_stat(path, &info) == FR_OK && !(info.fattrib & AM_DIR) && info.fsize > 0;
}

static bool wavegame_assets_detected_for_record(uint16_t record_index) {
    if (record_index >= full_record_count || sd_path_offsets[record_index] == 0xFFFF) {
        return false;
    }
    ROMRecord const *rec = &records[record_index];
    uint8_t flags = rec->Mapper & (SOURCE_SD_FLAG | FOLDER_FLAG | MP3_FLAG);
    if (!(flags & SOURCE_SD_FLAG) || (flags & (FOLDER_FLAG | MP3_FLAG)) || is_system_record(rec)) {
        return false;
    }

    char dir[SD_PATH_MAX];
    const char *rom_path = sd_path_buffer + sd_path_offsets[record_index];
    size_t len = strlen(rom_path);
    if (len == 0 || len >= sizeof(dir)) {
        return false;
    }
    memcpy(dir, rom_path, len + 1);
    char *slash = strrchr(dir, '/');
    if (!slash) {
        return false;
    }
    if (slash == dir) {
        slash[1] = '\0';
    } else {
        *slash = '\0';
    }

    if (wavegame_asset_exists_in_dir(dir, "multi.wav") || wavegame_asset_exists_in_dir(dir, "pause.wav")) {
        return true;
    }
    for (uint8_t i = 0; i < 64; i++) {
        char name[7];
        snprintf(name, sizeof(name), "%02u.wav", (unsigned)i);
        if (wavegame_asset_exists_in_dir(dir, name)) {
            return true;
        }
    }
    return false;
}

static uint16_t add_sd_rom_record(uint16_t record_index, const char *path, const char *filename, uint32_t size, uint8_t mapper) {
    if (record_index >= MAX_ROM_RECORDS) {
        return record_index;
    }
    size_t path_len = strlen(path);
    if (sd_path_buffer_used + path_len + 1 > SD_PATH_BUFFER_SIZE) {
        return record_index;
    }
    sd_path_offsets[record_index] = sd_path_buffer_used;
    memcpy(sd_path_buffer + sd_path_buffer_used, path, path_len + 1);
    sd_path_buffer_used = (uint16_t)(sd_path_buffer_used + path_len + 1);

    char display_name[ROM_NAME_MAX + 1];
    build_display_name(filename, display_name, sizeof(display_name));

    memset(records[record_index].Name, 0, sizeof(records[record_index].Name));
    strncpy(records[record_index].Name, display_name, sizeof(records[record_index].Name) - 1);
    records[record_index].Mapper = (unsigned char)(mapper | SOURCE_SD_FLAG);
    records[record_index].Size = (unsigned long)size;
    records[record_index].Offset = (unsigned long)record_index;
    return (uint16_t)(record_index + 1);
}

static uint16_t add_sd_mp3_record(uint16_t record_index, const char *path, const char *filename, uint32_t size, bool is_wav) {
    if (record_index >= MAX_ROM_RECORDS) {
        return record_index;
    }
    size_t path_len = strlen(path);
    if (sd_path_buffer_used + path_len + 1 > SD_PATH_BUFFER_SIZE) {
        return record_index;
    }
    sd_path_offsets[record_index] = sd_path_buffer_used;
    memcpy(sd_path_buffer + sd_path_buffer_used, path, path_len + 1);
    sd_path_buffer_used = (uint16_t)(sd_path_buffer_used + path_len + 1);

    char display_name[ROM_NAME_MAX + 1];
    build_display_name(filename, display_name, sizeof(display_name));

    memset(records[record_index].Name, 0, sizeof(records[record_index].Name));
    strncpy(records[record_index].Name, display_name, sizeof(records[record_index].Name) - 1);
    records[record_index].Mapper = (unsigned char)(MP3_FLAG | SOURCE_SD_FLAG | (is_wav ? AUDIO_TYPE_WAV : 0u));
    records[record_index].Size = (unsigned long)size;
    records[record_index].Offset = (unsigned long)record_index;
    return (uint16_t)(record_index + 1);
}

static void refresh_records_for_current_path(void) {
    sd_record_count = 0;
    sd_path_buffer_used = 0;
    for (uint16_t i = 0; i < MAX_ROM_RECORDS; i++) {
        sd_path_offsets[i] = 0xFFFF;
    }

    uint16_t record_index = 0;
    bool has_parent = !is_root_path(sd_current_path);

    if (has_parent) {
        record_index = add_folder_record(record_index, "..");
    }

    uint16_t folder_count = record_index;
    if (sd_mount_card()) {
        DIR dir;
        FILINFO fno;
        FRESULT fr = f_opendir(&dir, sd_current_path);
        if (fr == FR_OK) {
            while (record_index < MAX_ROM_RECORDS) {
                fr = f_readdir(&dir, &fno);
                if (fr != FR_OK || fno.fname[0] == '\0') {
                    break;
                }
                if (!(fno.fattrib & AM_DIR)) {
                    continue;
                }
                if (is_excluded_folder(fno.fname)) {
                    continue;
                }
                record_index = add_folder_record(record_index, fno.fname);
            }
        }
        f_closedir(&dir);

        folder_count = record_index;
        uint16_t folder_sort_start = has_parent ? 1u : 0u;
        if (folder_count > folder_sort_start) {
            sort_records_range(folder_sort_start, (uint16_t)(folder_count - folder_sort_start));
        }

        fr = f_opendir(&dir, sd_current_path);
        if (fr == FR_OK) {
            while (record_index < MAX_ROM_RECORDS) {
                fr = f_readdir(&dir, &fno);
                if (fr != FR_OK || fno.fname[0] == '\0') {
                    break;
                }
                if (fno.fattrib & AM_DIR) {
                    continue;
                }
                bool is_mp3 = has_mp3_extension(fno.fname);
                bool is_wav = has_wav_extension(fno.fname);
                bool is_rom = has_rom_extension(fno.fname);
#if EXPLORER_MP3_DISABLED
                // MP3 player temporarily disabled — skip MP3 entries.
                if (is_mp3 || is_wav) continue;
#endif

                if (!is_mp3 && !is_wav && !is_rom) {
                    continue;
                }

                char path[SD_PATH_MAX];
                int written;
                if (is_root_path(sd_current_path)) {
                    written = snprintf(path, sizeof(path), "/%s", fno.fname);
                } else {
                    written = snprintf(path, sizeof(path), "%s/%s", sd_current_path, fno.fname);
                }
                if (written <= 0 || (size_t)written >= sizeof(path)) {
                    continue;
                }

                if (is_mp3 || is_wav) {
                    if (fno.fsize == 0) {
                        continue;
                    }
                    record_index = add_sd_mp3_record(record_index, path, fno.fname, (uint32_t)fno.fsize, is_wav);
                    sd_record_count++;
                    continue;
                }

                if (fno.fsize < MIN_ROM_SIZE || fno.fsize > MAX_ROM_SIZE) {
                    continue;
                }
                if (fno.fsize > SD_ROM_MAX_SIZE) {
                    continue;
                }

                uint8_t mapper = mapper_number_from_filename(fno.fname);
                record_index = add_sd_rom_record(record_index, path, fno.fname, (uint32_t)fno.fsize, mapper);
                sd_record_count++;
            }
        }
        f_closedir(&dir);
    }

    if (is_root_path(sd_current_path) && flash_record_count > 0) {
        for (uint16_t i = 0; i < flash_record_count && record_index < MAX_ROM_RECORDS; i++) {
            records[record_index] = flash_records[i];
            sd_path_offsets[record_index] = 0xFFFF;
            record_index++;
        }
    }

    uint16_t rom_count = (uint16_t)(record_index - folder_count);
    if (rom_count > 1) {
        uint16_t system_insert = folder_count;
        for (uint16_t i = folder_count; i < record_index; i++) {
            if (is_system_record(&records[i])) {
                swap_records(i, system_insert);
                system_insert++;
            }
        }

        uint16_t system_count = (uint16_t)(system_insert - folder_count);
        uint16_t non_system_count = (uint16_t)(record_index - system_insert);
        if (non_system_count > 1) {
            sort_records_range(system_insert, non_system_count);
        }
    }

    full_record_count = record_index;
    memset(filter_query, 0, sizeof(filter_query));
    apply_filter();
    current_page = 0;
    build_page_buffer(current_page);
}

// Chunked version of refresh_records_for_current_path.
// Processes up to REFRESH_CHUNK_SIZE SD reads per call, then returns false
// to yield back to the MP3 decode loop. Returns true when done (or idle).
static bool refresh_records_chunked(void) {
    FILINFO fno;
    FRESULT fr;

    switch (refresh_state) {
    case REFRESH_IDLE:
        return true;

    case REFRESH_INIT:
        sd_record_count = 0;
        sd_path_buffer_used = 0;
        for (uint16_t i = 0; i < MAX_ROM_RECORDS; i++) {
            sd_path_offsets[i] = 0xFFFF;
        }
        refresh_record_index = 0;
        refresh_has_parent = !is_root_path(sd_current_path);
        if (refresh_has_parent) {
            refresh_record_index = add_folder_record(refresh_record_index, "..");
        }
        refresh_folder_count = refresh_record_index;
        ctrl_status_value = CTRL_MAGIC;
        if (browse_source_mode == SOURCE_MODE_FLASH) {
            refresh_state = REFRESH_FINALIZE;
            return false;
        }
        if (!sd_mount_card()) {
            if (browse_source_mode == SOURCE_MODE_SD) {
                ctrl_status_value = CTRL_STATUS_SD_MISSING;
            }
            refresh_state = REFRESH_FINALIZE;
            return false;
        }
        fr = f_opendir(&refresh_dir, sd_current_path);
        if (fr != FR_OK) {
            if (browse_source_mode == SOURCE_MODE_SD) {
                ctrl_status_value = CTRL_STATUS_SD_MISSING;
            }
            refresh_state = REFRESH_FINALIZE;
            return false;
        }
        refresh_state = REFRESH_SCAN_FOLDERS;
        return false;

    case REFRESH_SCAN_FOLDERS: {
        int reads = 0;
        while (reads < REFRESH_CHUNK_SIZE && refresh_record_index < MAX_ROM_RECORDS) {
            fr = f_readdir(&refresh_dir, &fno);
            reads++;
            if (fr != FR_OK || fno.fname[0] == '\0') {
                f_closedir(&refresh_dir);
                refresh_state = REFRESH_SORT_FOLDERS;
                return false;
            }
            if (!(fno.fattrib & AM_DIR)) continue;
            if (is_excluded_folder(fno.fname)) continue;
            refresh_record_index = add_folder_record(refresh_record_index, fno.fname);
        }
        if (refresh_record_index >= MAX_ROM_RECORDS) {
            f_closedir(&refresh_dir);
            refresh_state = REFRESH_SORT_FOLDERS;
        }
        return false;
    }

    case REFRESH_SORT_FOLDERS: {
        refresh_folder_count = refresh_record_index;
        uint16_t folder_sort_start = refresh_has_parent ? 1u : 0u;
        if (refresh_folder_count > folder_sort_start) {
            sort_records_range(folder_sort_start, (uint16_t)(refresh_folder_count - folder_sort_start));
        }
        fr = f_opendir(&refresh_dir, sd_current_path);
        if (fr != FR_OK) {
            refresh_state = REFRESH_FINALIZE;
            return false;
        }
        refresh_state = REFRESH_SCAN_FILES;
        return false;
    }

    case REFRESH_SCAN_FILES: {
        int reads = 0;
        while (reads < REFRESH_CHUNK_SIZE && refresh_record_index < MAX_ROM_RECORDS) {
            fr = f_readdir(&refresh_dir, &fno);
            reads++;
            if (fr != FR_OK || fno.fname[0] == '\0') {
                f_closedir(&refresh_dir);
                refresh_state = REFRESH_FINALIZE;
                return false;
            }
            if (fno.fattrib & AM_DIR) continue;
            bool is_mp3 = has_mp3_extension(fno.fname);
            bool is_wav = has_wav_extension(fno.fname);
            bool is_rom = has_rom_extension(fno.fname);
#if EXPLORER_MP3_DISABLED
            // MP3 player temporarily disabled — skip MP3 entries.
            if (is_mp3 || is_wav) continue;
#endif
            if (!is_mp3 && !is_wav && !is_rom) continue;

            char path[SD_PATH_MAX];
            int written;
            if (is_root_path(sd_current_path)) {
                written = snprintf(path, sizeof(path), "/%s", fno.fname);
            } else {
                written = snprintf(path, sizeof(path), "%s/%s", sd_current_path, fno.fname);
            }
            if (written <= 0 || (size_t)written >= sizeof(path)) {
                continue;
            }

            if (is_mp3 || is_wav) {
                if (fno.fsize == 0) continue;
                refresh_record_index = add_sd_mp3_record(refresh_record_index, path, fno.fname, (uint32_t)fno.fsize, is_wav);
                sd_record_count++;
                continue;
            }

            if (fno.fsize < MIN_ROM_SIZE || fno.fsize > MAX_ROM_SIZE) continue;
            if (fno.fsize > SD_ROM_MAX_SIZE) continue;

            uint8_t mapper = mapper_number_from_filename(fno.fname);
            refresh_record_index = add_sd_rom_record(refresh_record_index, path, fno.fname, (uint32_t)fno.fsize, mapper);
            sd_record_count++;
        }
        if (refresh_record_index >= MAX_ROM_RECORDS) {
            f_closedir(&refresh_dir);
            refresh_state = REFRESH_FINALIZE;
        }
        return false;
    }

    case REFRESH_FINALIZE: {
        if (is_root_path(sd_current_path) && flash_record_count > 0) {
            for (uint16_t i = 0; i < flash_record_count && refresh_record_index < MAX_ROM_RECORDS; i++) {
                records[refresh_record_index] = flash_records[i];
                sd_path_offsets[refresh_record_index] = 0xFFFF;
                refresh_record_index++;
            }
        }

        uint16_t rom_count = (uint16_t)(refresh_record_index - refresh_folder_count);
        if (rom_count > 1) {
            uint16_t system_insert = refresh_folder_count;
            for (uint16_t i = refresh_folder_count; i < refresh_record_index; i++) {
                if (is_system_record(&records[i])) {
                    swap_records(i, system_insert);
                    system_insert++;
                }
            }
            uint16_t system_count = (uint16_t)(system_insert - refresh_folder_count);
            uint16_t non_system_count = (uint16_t)(refresh_record_index - system_insert);
            if (non_system_count > 1) {
                sort_records_range(system_insert, non_system_count);
            }
        }

        full_record_count = refresh_record_index;
        memset(filter_query, 0, sizeof(filter_query));
        apply_filter();
        current_page = 0;
        build_page_buffer(current_page);
        refresh_state = REFRESH_IDLE;
        return true;
    }

    default:
        refresh_state = REFRESH_IDLE;
        return true;
    }
}

static void process_detect_mapper_request(uint16_t filtered_index) {
    ctrl_mapper_value = 0;
    quiesce_mp3_core1_before_sd_work();

    if (!sd_mount_card()) {
        ctrl_cmd_state = 0;
        return;
    }

    if (filtered_index >= total_record_count) {
        ctrl_cmd_state = 0;
        return;
    }

    uint16_t record_index = filtered_indices[filtered_index];
    if (record_index >= full_record_count) {
        ctrl_cmd_state = 0;
        return;
    }

    ROMRecord *rec = &records[record_index];
    uint8_t flags = rec->Mapper & (SOURCE_SD_FLAG | FOLDER_FLAG | MP3_FLAG);

    if (!(flags & SOURCE_SD_FLAG) || (flags & (FOLDER_FLAG | MP3_FLAG)) || sd_path_offsets[record_index] == 0xFFFF) {
        ctrl_mapper_value = mapper_code_from_record_byte(rec->Mapper);
        ctrl_cmd_state = 0;
        return;
    }

    const char *path = sd_path_buffer + sd_path_offsets[record_index];
    const char *filename = basename_from_path(path);

    uint8_t mapper = mapper_number_from_filename(filename);
    if (mapper == 0) {
        mapper = detect_rom_type_from_file(path, (uint32_t)rec->Size);
    }

    ctrl_mapper_value = mapper;
    if (mapper != 0) {
        rec->Mapper = (uint8_t)(flags | mapper);
    } else {
        rec->Mapper = flags;
    }

    ctrl_cmd_state = 0;
}

static void init_pico_chip_id(void) {
    pico_get_unique_board_id_string(pico_chip_id, sizeof(pico_chip_id));
    pico_chip_id[CTRL_CHIP_ID_SIZE - 1u] = '\0';
}

static void ensure_mp3_core1_started(void);

// Find an audio filtered index for auto-advance and manual skip.
// mode: MP3_PLAY_MODE_ALL = sequential wrap, MP3_PLAY_MODE_RANDOM = random pick.
static uint16_t find_mp3_filtered_index(uint16_t current, uint8_t mode, int direction) {
    if (total_record_count == 0) return 0xFFFF;

    if (mode == MP3_PLAY_MODE_RANDOM) {
        uint16_t mp3_count = 0;
        for (uint16_t i = 0; i < total_record_count; i++) {
            uint16_t ri = filtered_indices[i];
            if (ri < full_record_count && (records[ri].Mapper & MP3_FLAG))
                mp3_count++;
        }
        if (mp3_count == 0) return 0xFFFF;

        // Use microsecond timer as entropy for random pick
        uint16_t target = (uint16_t)(time_us_32() % mp3_count);
        uint16_t ord = 0;
        for (uint16_t i = 0; i < total_record_count; i++) {
            uint16_t ri = filtered_indices[i];
            if (ri < full_record_count && (records[ri].Mapper & MP3_FLAG)) {
                if (ord == target) return i;
                ord++;
            }
        }
        return 0xFFFF;
    }

    if (direction < 0) {
        uint16_t start = (current != 0xFFFF && current > 0) ? (uint16_t)(current - 1u) : (uint16_t)(total_record_count - 1u);
        for (uint16_t count = 0; count < total_record_count; count++) {
            uint16_t i = (uint16_t)((start + total_record_count - count) % total_record_count);
            uint16_t ri = filtered_indices[i];
            if (ri < full_record_count && (records[ri].Mapper & MP3_FLAG)) {
                return i;
            }
        }
        return 0xFFFF;
    }

    uint16_t start = (current != 0xFFFF && current + 1 < total_record_count) ? (uint16_t)(current + 1u) : 0;
    for (uint16_t count = 0; count < total_record_count; count++) {
        uint16_t i = (start + count) % total_record_count;
        uint16_t ri = filtered_indices[i];
        if (ri < full_record_count && (records[ri].Mapper & MP3_FLAG)) {
            return i;
        }
    }
    return 0xFFFF;
}

static bool mp3_play_filtered_index(uint16_t filtered_index) {
    if (filtered_index >= total_record_count) {
        return false;
    }
    uint16_t record_index = filtered_indices[filtered_index];
    if (record_index >= full_record_count || !(records[record_index].Mapper & MP3_FLAG) || sd_path_offsets[record_index] == 0xFFFF) {
        return false;
    }
    const char *path = sd_path_buffer + sd_path_offsets[record_index];
    printf("MP3: play filtered=%u path=%s\n", (unsigned)filtered_index, path);
    ensure_mp3_core1_started();
    mp3_select_file(path, (uint32_t)records[record_index].Size);
    mp3_send_cmd(MP3_CMD_PLAY);
    mp3_playing_filtered_index = filtered_index;
    mp3_selected_index = filtered_index;
    return true;
}

// Lazy non-blocking launch of Core 1 + MP3 stack. Called from
// core1_bg_work() the first time the MSX dispatches an MP3 command.
// We deliberately do NOT spin Core 0 waiting for Core 1 to finish
// mp3_init() — Core 0 is servicing the MSX PIO bus and any block
// here freezes the cartridge. The cross-core command queue is a
// small ring buffer so SELECT and PLAY (issued ~10 ms apart) both
// fit while Core 1 is still initialising.
static bool mp3_core1_started = false;

static void hold_msx_wait(void) {
    gpio_init(PIN_WAIT);
    gpio_set_dir(PIN_WAIT, GPIO_OUT);
    gpio_put(PIN_WAIT, 0);
}

static void ensure_mp3_core1_started(void) {
#if EXPLORER_MP3_DISABLED
    // MP3 player disabled: never launch Core 1 from the menu, so the
    // SD card stays single-owner on Core 0 with no risk of cross-core
    // FatFS / I2S / DMA contention.
    return;
#else
    if (mp3_core1_started) return;
    // Keep MP3 stream buffering out of SRAM so MSX-MUSIC can allocate its OPLL state later.
    psram_prepare_mp3_buffer();
    // If a prior File Hunter operation (or ROM launch) quiesced the audio core
    // and handed off the live I2S pool, re-adopt it so the relaunched core
    // reuses the pico_audio_i2s pipeline instead of re-running audio_i2s_setup()
    // (which leaks PIO/IRQ-handler slots on the vendored singleton and is
    // unreliable as a re-setup). claim_rom_audio_handoff_pool() also re-arms the
    // I2S DMA. ROM-launch paths consume the pool themselves before calling here,
    // so this is a no-op for them.
    {
        struct audio_buffer_pool *handoff = claim_rom_audio_handoff_pool();
        if (handoff)
            mp3_adopt_i2s_audio_pool(handoff);
    }
    mp3_core1_started = true;
    multicore_launch_core1(mp3_core1_loop);
#endif
}

#define WAVEGAME_PORT 0x92u

static inline bool __not_in_flash_func(main_psg_handle_io_write)(uint8_t port, uint8_t data);

static void wavegame_clear(void)
{
    wavegame_active = false;
    wavegame_psg_mirror_active = false;
    wavegame_dir[0] = '\0';
    wavegame_defer_next = false;
    wavegame_deferred_valid = false;
    wavegame_deferred_data = 0;
    mp3_wavegame_set_psg_callbacks(NULL, NULL);
}

static void wavegame_prepare_for_rom(uint16_t record_index, bool enabled)
{
    wavegame_clear();
    if (!enabled || record_index >= MAX_ROM_RECORDS || sd_path_offsets[record_index] == 0xFFFF)
        return;

    const char *rom_path = sd_path_buffer + sd_path_offsets[record_index];
    size_t len = strlen(rom_path);
    if (len == 0 || len >= sizeof(wavegame_dir))
        return;

    memcpy(wavegame_dir, rom_path, len + 1);
    char *slash = strrchr(wavegame_dir, '/');
    if (!slash)
        return;
    if (slash == wavegame_dir)
        slash[1] = '\0';
    else
        slash[0] = '\0';
    wavegame_active = true;
    printf("WAVEGAME: active dir=%s\n", wavegame_dir);
}

static bool wavegame_is_playing(void)
{
    if (!mp3_core1_started)
        return false;
    uint8_t status = mp3_get_status();
    return (status & (MP3_STATUS_PLAYING | MP3_STATUS_PAUSED)) != 0;
}

static bool wavegame_execute_command(uint8_t data, bool allow_defer)
{
    if ((data & 0xC0u) == 0x40u)
    {
        ensure_mp3_core1_started();
        mp3_wavegame_play_index(wavegame_dir, (uint8_t)(data & 0x3Fu), false);
        return true;
    }
    if ((data & 0xC0u) == 0x80u)
    {
        ensure_mp3_core1_started();
        mp3_wavegame_play_index(wavegame_dir, (uint8_t)(data & 0x3Fu), true);
        return true;
    }
    if ((data & 0xF0u) == 0x00u)
    {
        ensure_mp3_core1_started();
        mp3_wavegame_fade_out((uint8_t)(data & 0x0Fu));
        return true;
    }

    switch (data)
    {
        case 0xC0u:
            ensure_mp3_core1_started();
            mp3_wavegame_toggle_pause();
            return true;
        case 0xD0u:
            if (allow_defer)
                wavegame_defer_next = true;
            return true;
        case 0xE0u:
            ensure_mp3_core1_started();
            mp3_wavegame_resume_previous();
            return true;
        case 0xF0u:
            ensure_mp3_core1_started();
            mp3_wavegame_play_pause(wavegame_dir);
            return true;
        default:
            return true;
    }
}

static inline bool __not_in_flash_func(wavegame_handle_io_write)(uint8_t port, uint8_t data)
{
    if (!wavegame_active || port != WAVEGAME_PORT)
        return false;

    if (wavegame_defer_next)
    {
        wavegame_defer_next = false;
        wavegame_deferred_data = data;
        wavegame_deferred_valid = true;
        if (!wavegame_is_playing())
        {
            wavegame_deferred_valid = false;
            (void)wavegame_execute_command(wavegame_deferred_data, false);
        }
        return true;
    }

    printf("WAVEGAME: port=92 data=%02x\n", (unsigned)data);
    return wavegame_execute_command(data, true);
}

static inline void __not_in_flash_func(wavegame_service_io)(void)
{
    if (!wavegame_active)
        return;

    uint16_t io_addr;
    uint8_t io_data;
    while (pio_try_get_io_write(&io_addr, &io_data))
    {
        uint8_t port = (uint8_t)(io_addr & 0xFFu);
        if (wavegame_handle_io_write(port, io_data))
            continue;
        if (wavegame_psg_mirror_active)
            (void)main_psg_handle_io_write(port, io_data);
    }

    if (wavegame_deferred_valid && !wavegame_is_playing())
    {
        uint8_t data = wavegame_deferred_data;
        wavegame_deferred_valid = false;
        printf("WAVEGAME: deferred data=%02x\n", (unsigned)data);
        (void)wavegame_execute_command(data, false);
    }
}

static void shutdown_mp3_core1_before_rom_launch(void) {
#if EXPLORER_MP3_DISABLED
    return;
#else
    debug_trace("DBG shutdown_mp3 enter started=%u", mp3_core1_started ? 1u : 0u);
    if (!mp3_core1_started) {
        return;
    }

    debug_trace("DBG shutdown_mp3 request");
    mp3_request_shutdown();
    uint32_t deadline = time_us_32() + 2000000u;
    while (!mp3_core1_has_stopped() && (int32_t)(deadline - time_us_32()) > 0) {
        sleep_us(200);
    }

    debug_trace("DBG shutdown_mp3 stopped=%u", mp3_core1_has_stopped() ? 1u : 0u);
    if (!mp3_core1_has_stopped()) {
        debug_trace("DBG shutdown_mp3 reset/deinit");
        multicore_reset_core1();
        mp3_deinit();
    } else {
        debug_trace("DBG shutdown_mp3 take pool");
        rom_audio_handoff_pool = mp3_take_i2s_audio_pool();
        multicore_reset_core1();
    }
    mp3_core1_started = false;
    debug_trace("DBG shutdown_mp3 done pool=%p", (void *)rom_audio_handoff_pool);
#endif
}

static void force_mp3_core1_handoff_before_rom_launch(void) {
#if EXPLORER_MP3_DISABLED
    return;
#else
    debug_trace("DBG force_mp3 enter started=%u", mp3_core1_started ? 1u : 0u);
    if (!mp3_core1_started) {
        return;
    }

    debug_trace("DBG force_mp3 reset core1");
    multicore_reset_core1();
    debug_trace("DBG force_mp3 take pool");
    rom_audio_handoff_pool = mp3_force_i2s_handoff_from_core0();
    mp3_core1_started = false;
    debug_trace("DBG force_mp3 done pool=%p", (void *)rom_audio_handoff_pool);
#endif
}

static void quiesce_mp3_core1_before_sd_work(void) {
#if EXPLORER_MP3_DISABLED
    return;
#else
    if (!mp3_core1_started) {
        return;
    }

    mp3_pending_cmd = 0;
    mp3_pending_select = false;
    shutdown_mp3_core1_before_rom_launch();
#endif
}

// Background work pump. Runs on Core 0 from the menu loop idle branch
// (no PIO traffic from the MSX). Single-core ownership of the SD card
// avoids FatFS reentrancy issues and removes the freeze observed when
// folder navigation raced with MP3 work on Core 1.
static void fh_save_background_work(void);
static void core1_bg_work(void) {
    if (fh_save_state == FH_SAVE_RUNNING) {
        fh_save_background_work();
        return;
    }

    // Bridge MP3 commands queued by handle_menu_write_explorer() to the
    // mp3.c command queue. Lazy-launch Core 1 the first time an MP3
    // command actually arrives.
    if (mp3_pending_select) {
        uint16_t pending_index = mp3_pending_index;
        mp3_pending_select = false;
        if (pending_index < total_record_count) {
            uint16_t record_index = filtered_indices[pending_index];
            if (record_index < full_record_count) {
                ROMRecord const *rec = &records[record_index];
                if ((rec->Mapper & MP3_FLAG) && (sd_path_offsets[record_index] != 0xFFFF)) {
                    const char *path = sd_path_buffer + sd_path_offsets[record_index];
                    printf("MP3: select path=%s size=%lu\n", path, (unsigned long)rec->Size);
                    ensure_mp3_core1_started();
                    mp3_select_file(path, (uint32_t)rec->Size);
                    mp3_playing_filtered_index = pending_index;
                } else {
                    printf("MP3: select ignored (not audio or no path)\n");
                }
            } else {
                printf("MP3: select index out of range\n");
            }
        } else {
            printf("MP3: select index invalid (total=%u)\n", (unsigned int)total_record_count);
        }
    }
    if (mp3_pending_cmd != 0) {
        uint8_t cmd = mp3_pending_cmd;
        mp3_pending_cmd = 0;
        if (cmd == MP3_CMD_NEXT || cmd == MP3_CMD_PREVIOUS) {
            uint16_t next = find_mp3_filtered_index(mp3_playing_filtered_index, mp3_play_mode,
                                                    (cmd == MP3_CMD_PREVIOUS) ? -1 : 1);
            if (next != 0xFFFF) {
                (void)mp3_play_filtered_index(next);
            }
        } else if (mp3_core1_started || cmd == MP3_CMD_PLAY) {
            ensure_mp3_core1_started();
            mp3_send_cmd(cmd);
        }
    }

    // Auto-advance: when current track ends and mode is ALL or RANDOM,
    // automatically select and play the next track.
    if (mp3_play_mode != MP3_PLAY_MODE_SINGLE) {
        uint8_t st = mp3_get_status();
        if ((st & MP3_STATUS_EOF) && !(st & MP3_STATUS_PLAYING)) {
            uint16_t next = find_mp3_filtered_index(mp3_playing_filtered_index, mp3_play_mode, 1);
            if (next != 0xFFFF) {
                uint16_t ri = filtered_indices[next];
                const char *path = sd_path_buffer + sd_path_offsets[ri];
                printf("MP3: auto-advance to index %u path=%s\n", (unsigned)next, path);
                mp3_auto_play(path, (uint32_t)records[ri].Size);
                mp3_playing_filtered_index = next;
                mp3_selected_index = next;
            }
        }
    }

    // Defer SD-heavy work while MP3 is actively playing to avoid
    // SPI bus contention between directory reads and MP3 file reads.
    if (mp3_get_status() & MP3_STATUS_PLAYING) {
        return;
    }

    // Chunked directory refresh — process one chunk then yield
    if (refresh_state != REFRESH_IDLE) {
        bool done = refresh_records_chunked();
        if (done) {
            refresh_in_progress = false;
            ctrl_cmd_state = 0;
        }
        return;
    }

    if (refresh_requested) {
        refresh_requested = false;
        refresh_in_progress = true;
        refresh_state = REFRESH_INIT;
        return;
    }

    if (detect_mapper_pending && !refresh_in_progress) {
        uint16_t pending_index = detect_mapper_index;
        detect_mapper_pending = false;
        process_detect_mapper_request(pending_index);
    }
}

static bool load_rom_from_sd(uint16_t record_index, uint32_t size) {
    if (!sd_mount_card()) {
        printf("SDLOAD: mount failed\n");
        return false;
    }
    if (record_index >= full_record_count || record_index >= MAX_ROM_RECORDS) {
        printf("SDLOAD: bad record=%u full=%u\n", (unsigned)record_index, (unsigned)full_record_count);
        return false;
    }
    if (sd_path_offsets[record_index] == 0xFFFF) {
        printf("SDLOAD: missing path record=%u\n", (unsigned)record_index);
        return false;
    }

    // SD ROMs are streamed into the 4MB PSRAM region so rom_sram remains
    // available for flash-resident mapper caching. Bring PSRAM up lazily.
    if (!psram_bring_up_once()) {
        printf("SDLOAD: psram bring-up failed\n");
        return false;
    }
    if (size > sd_rom_region.size) {
        printf("SDLOAD: too large size=%lu region=%lu\n", (unsigned long)size, (unsigned long)sd_rom_region.size);
        return false;
    }

    const char *path = sd_path_buffer + sd_path_offsets[record_index];
    printf("SDLOAD: record=%u size=%lu path=%s\n", (unsigned)record_index, (unsigned long)size, path);

    FIL fil;
    FRESULT fr = f_open(&fil, path, FA_READ);
    if (fr != FR_OK) {
        printf("SDLOAD: open failed fr=%d\n", (int)fr);
        return false;
    }

    gpio_init(PIN_WAIT);
    gpio_set_dir(PIN_WAIT, GPIO_OUT);
    gpio_put(PIN_WAIT, 0);

    uint8_t *dst = sd_rom_region.ptr;
    memset(dst, 0, size);

    UINT total = 0;
    while (total < size) {
        UINT to_read = (UINT)((size - total) > 4096 ? 4096 : (size - total));
        UINT br = 0;
        fr = f_read(&fil, dst + total, to_read, &br);
        if (fr != FR_OK || br == 0) {
            printf("SDLOAD: read stopped fr=%d br=%u total=%u target=%lu\n", (int)fr, (unsigned)br, (unsigned)total, (unsigned long)size);
            break;
        }
        total += br;
    }

    f_close(&fil);
    gpio_set_dir(PIN_WAIT, GPIO_IN);

    if (total != size) {
        printf("SDLOAD: short read total=%u target=%lu\n", (unsigned)total, (unsigned long)size);
        return false;
    }
    printf("SDLOAD: loaded %u bytes\n", (unsigned)total);
    return true;
}

// Initialize GPIO pins
static inline void setup_gpio()
{

    for (int i = 0; i <= 23; i++) {
        gpio_init(i);
        gpio_set_input_hysteresis_enabled(i, true);
    }

    for (int i = 0; i <= 15; i++) {
        gpio_set_dir(i, GPIO_IN);
    }

    // Initialize control pins as input
    gpio_init(PIN_RD); gpio_set_dir(PIN_RD, GPIO_IN);    
    gpio_init(PIN_WR); gpio_set_dir(PIN_WR, GPIO_IN); 
    gpio_init(PIN_IORQ); gpio_set_dir(PIN_IORQ, GPIO_IN); 
    gpio_init(PIN_SLTSL); gpio_set_dir(PIN_SLTSL, GPIO_IN); 
    gpio_init(PIN_BUSSDIR); gpio_set_dir(PIN_BUSSDIR, GPIO_IN); 

    gpio_init(I2S_MUTE_PIN);
    gpio_set_dir(I2S_MUTE_PIN, GPIO_OUT);
    gpio_put(I2S_MUTE_PIN, 1);
}

// read_ulong - Read a 4-byte value from the memory area
// This function will read a 4-byte value from the memory area pointed by ptr and return the value as an unsigned long
// Parameters:
//   ptr - Pointer to the memory area to read the value from
// Returns:
//   The 4-byte value as an unsigned long 
unsigned long __no_inline_not_in_flash_func(read_ulong)(const unsigned char *ptr) {
    return (unsigned long)ptr[0] |
           ((unsigned long)ptr[1] << 8) |
           ((unsigned long)ptr[2] << 16) |
           ((unsigned long)ptr[3] << 24);
}

// isEndOfData - Check if the memory area is the end of the data
// This function will check if the memory area pointed by memory is the end of the data. The end of the data is defined by all bytes being 0xFF.
// Parameters:
//   memory - Pointer to the memory area to check
// Returns:
//   1 if the memory area is the end of the data, 0 otherwise
int __no_inline_not_in_flash_func(isEndOfData)(const unsigned char *memory) {
    for (int i = 0; i < ROM_RECORD_SIZE; i++) {
        if (memory[i] != 0xFF) {
            return 0;
        }
    }
    return 1;
}

// -----------------------------------------------------------------------
// External PSRAM (QMI CS1) - hardware init + bump allocator.
// Mirrors the implementation in multirom so the same code paths work
// across the two firmwares. Used for SD-cached ROM storage so that
// rom_sram remains fully available for flash-resident mapper caching.
// -----------------------------------------------------------------------
static inline void __not_in_flash_func(psram_delay_cycles)(uint32_t cycles)
{
    for (volatile uint32_t cycle = 0; cycle < cycles; ++cycle)
    {
        __asm volatile ("nop");
    }
}

static inline void __not_in_flash_func(psram_wait_direct_done)(void)
{
    while ((qmi_hw->direct_csr & QMI_DIRECT_CSR_TXEMPTY_BITS) == 0) { }
    while ((qmi_hw->direct_csr & QMI_DIRECT_CSR_BUSY_BITS) != 0) { }
}

static inline void __not_in_flash_func(psram_send_direct_cmd)(uint8_t cmd, bool quad_width)
{
    qmi_hw->direct_csr |= QMI_DIRECT_CSR_ASSERT_CS1N_BITS;
    if (quad_width)
    {
        qmi_hw->direct_tx = QMI_DIRECT_TX_OE_BITS |
                            (QMI_DIRECT_TX_IWIDTH_VALUE_Q << QMI_DIRECT_TX_IWIDTH_LSB) |
                            cmd;
    }
    else
    {
        qmi_hw->direct_tx = cmd;
    }
    psram_wait_direct_done();
    qmi_hw->direct_csr &= ~QMI_DIRECT_CSR_ASSERT_CS1N_BITS;
    (void)qmi_hw->direct_rx;
}

static bool __no_inline_not_in_flash_func(psram_init)(void)
{
    gpio_set_function(PIN_PSRAM, GPIO_FUNC_XIP_CS1);

    uint32_t irq_state = save_and_disable_interrupts();

    qmi_hw->direct_csr = (30u << QMI_DIRECT_CSR_CLKDIV_LSB) | QMI_DIRECT_CSR_EN_BITS;
    while ((qmi_hw->direct_csr & QMI_DIRECT_CSR_BUSY_BITS) != 0) { }

    // Warm restart path: if PSRAM remained powered it may still be in QPI mode.
    psram_send_direct_cmd(0xF5u, true);
    psram_delay_cycles(128u);

    psram_send_direct_cmd(0x66u, false);
    psram_delay_cycles(128u);
    psram_send_direct_cmd(0x99u, false);
    psram_delay_cycles(50000u);
    psram_send_direct_cmd(0x35u, false);
    psram_delay_cycles(128u);
    // LY68L6400S PSRAM compatibility: Ludovic Avot reported that this chip
    // does not tolerate the optional 0xC0 post-QPI initialization command.
    // psram_send_direct_cmd(0xC0u, false);
    // psram_delay_cycles(128u);

    qmi_hw->direct_csr &= ~(QMI_DIRECT_CSR_ASSERT_CS1N_BITS | QMI_DIRECT_CSR_EN_BITS);

    // PSRAM QMI timing - tuned for 210 MHz system clock (CLKDIV=2 -> ~52.5 MHz).
    qmi_hw->m[1].timing =
        (QMI_M0_TIMING_PAGEBREAK_VALUE_1024 << QMI_M0_TIMING_PAGEBREAK_LSB) |
        (1u << QMI_M0_TIMING_SELECT_HOLD_LSB) |
        (1u << QMI_M0_TIMING_COOLDOWN_LSB) |
        (2u << QMI_M0_TIMING_RXDELAY_LSB) |
        (26u << QMI_M0_TIMING_MAX_SELECT_LSB) |
        (5u << QMI_M0_TIMING_MIN_DESELECT_LSB) |
        (2u << QMI_M0_TIMING_CLKDIV_LSB);
    qmi_hw->m[1].rfmt =
        (QMI_M0_RFMT_PREFIX_WIDTH_VALUE_Q << QMI_M0_RFMT_PREFIX_WIDTH_LSB) |
        (QMI_M0_RFMT_ADDR_WIDTH_VALUE_Q << QMI_M0_RFMT_ADDR_WIDTH_LSB) |
        (QMI_M0_RFMT_SUFFIX_WIDTH_VALUE_Q << QMI_M0_RFMT_SUFFIX_WIDTH_LSB) |
        (QMI_M0_RFMT_DUMMY_WIDTH_VALUE_Q << QMI_M0_RFMT_DUMMY_WIDTH_LSB) |
        (QMI_M0_RFMT_DUMMY_LEN_VALUE_24 << QMI_M0_RFMT_DUMMY_LEN_LSB) |
        (QMI_M0_RFMT_DATA_WIDTH_VALUE_Q << QMI_M0_RFMT_DATA_WIDTH_LSB) |
        (QMI_M0_RFMT_PREFIX_LEN_VALUE_8 << QMI_M0_RFMT_PREFIX_LEN_LSB) |
        (QMI_M0_RFMT_SUFFIX_LEN_VALUE_NONE << QMI_M0_RFMT_SUFFIX_LEN_LSB);
    qmi_hw->m[1].rcmd = (0xEBu << QMI_M0_RCMD_PREFIX_LSB);
    qmi_hw->m[1].wfmt =
        (QMI_M0_WFMT_PREFIX_WIDTH_VALUE_Q << QMI_M0_WFMT_PREFIX_WIDTH_LSB) |
        (QMI_M0_WFMT_ADDR_WIDTH_VALUE_Q << QMI_M0_WFMT_ADDR_WIDTH_LSB) |
        (QMI_M0_WFMT_SUFFIX_WIDTH_VALUE_Q << QMI_M0_WFMT_SUFFIX_WIDTH_LSB) |
        (QMI_M0_WFMT_DUMMY_WIDTH_VALUE_Q << QMI_M0_WFMT_DUMMY_WIDTH_LSB) |
        (QMI_M0_WFMT_DUMMY_LEN_VALUE_NONE << QMI_M0_WFMT_DUMMY_LEN_LSB) |
        (QMI_M0_WFMT_DATA_WIDTH_VALUE_Q << QMI_M0_WFMT_DATA_WIDTH_LSB) |
        (QMI_M0_WFMT_PREFIX_LEN_VALUE_8 << QMI_M0_WFMT_PREFIX_LEN_LSB) |
        (QMI_M0_WFMT_SUFFIX_LEN_VALUE_NONE << QMI_M0_WFMT_SUFFIX_LEN_LSB);
    qmi_hw->m[1].wcmd = (0x38u << QMI_M0_WCMD_PREFIX_LSB);

    xip_ctrl_hw->ctrl |= XIP_CTRL_WRITABLE_M1_BITS;

    restore_interrupts(irq_state);

    // Verify PSRAM via uncached window (bypass XIP cache).
    volatile uint32_t *psram_test = (volatile uint32_t *)0x15000000u;
    psram_test[0] = 0x12345678u;
    return psram_test[0] == 0x12345678u;
}

// -----------------------------------------------------------------------
// PSRAM Memory Manager - bump allocator for 8MB external PSRAM.
// -----------------------------------------------------------------------
static struct {
    uint32_t next_free;
    bool initialised;
} psram_mgr;

static void psram_mem_init(void)
{
    psram_mgr.next_free = 0;
    memset(&sd_rom_region, 0, sizeof(sd_rom_region));
    memset(&rom_cache_region, 0, sizeof(rom_cache_region));
    rom_sram = NULL;
    memset(&mapper_region, 0, sizeof(mapper_region));
    memset(&c2_rom_region, 0, sizeof(c2_rom_region));
    memset(&megaram_region, 0, sizeof(megaram_region));
    memset(&mp3_buffer_region, 0, sizeof(mp3_buffer_region));
    memset(&fh_list_region, 0, sizeof(fh_list_region));
    memset(&fh_download_region, 0, sizeof(fh_download_region));
    fh_download_size = 0;
    memset(fh_download_name, 0, sizeof(fh_download_name));
}

static bool psram_alloc(uint32_t size, psram_region_t *region)
{
    if (psram_mgr.next_free + size > PSRAM_TOTAL_SIZE)
        return false;
    region->offset = psram_mgr.next_free;
    region->size   = size;
    region->ptr    = (uint8_t *)(PSRAM_BASE_ADDR + psram_mgr.next_free);
    psram_mgr.next_free += size;
    return true;
}

// One-time PSRAM bring-up + region carve-out. Idempotent. Returns false if
// the hardware probe fails or any allocation cannot be satisfied.
static bool psram_bring_up_once(void)
{
    if (psram_mgr.initialised) return true;
    if (!psram_init()) return false;
    psram_mem_init();
    // 4MB region for SD-loaded ROMs.
    if (!psram_alloc(SD_ROM_MAX_SIZE, &sd_rom_region)) return false;
    psram_mgr.initialised = true;
    return true;
}

static bool psram_prepare_mapper_region(void)
{
    if (!psram_bring_up_once()) return false;
    if (mapper_region.size == MAPPER_SIZE) return true;
    return psram_alloc(MAPPER_SIZE, &mapper_region);
}

static bool psram_prepare_c2_region(void)
{
    if (!psram_bring_up_once()) return false;
    if (c2_rom_region.size == MAPPER_SIZE) return true;
    return psram_alloc(MAPPER_SIZE, &c2_rom_region);
}

static bool psram_prepare_megaram_region(void)
{
    if (!psram_bring_up_once()) return false;
    if (megaram_region.size == MEGARAM_SIZE) return true;
    return psram_alloc(MEGARAM_SIZE, &megaram_region);
}

static bool psram_prepare_mp3_buffer(void)
{
    if (!psram_bring_up_once()) return false;
    if (mp3_buffer_region.ptr && mp3_buffer_region.size >= MP3_PSRAM_BUFFER_SIZE) return true;
    if (!psram_alloc(MP3_PSRAM_BUFFER_SIZE, &mp3_buffer_region)) return false;
    mp3_set_external_buffer(mp3_buffer_region.ptr, mp3_buffer_region.size);
    return true;
}

static bool psram_prepare_rom_cache(void)
{
    if (!psram_bring_up_once()) return false;
    if (rom_cache_region.size == CACHE_SIZE)
    {
        rom_sram = rom_cache_region.ptr;
        return true;
    }
    if (!psram_alloc(CACHE_SIZE, &rom_cache_region)) return false;
    rom_sram = rom_cache_region.ptr;
    return true;
}

static bool fh_prepare_list_region(void)
{
    if (!psram_bring_up_once()) return false;
    if (fh_list_region.ptr && fh_list_region.size >= FH_HTTP_BUFFER_SIZE) return true;
    return psram_alloc(FH_HTTP_BUFFER_SIZE, &fh_list_region);
}

static inline void __not_in_flash_func(prepare_rom_source)(
    uint32_t offset,
    bool cache_enable,
    uint32_t preferred_size,
    const uint8_t **rom_base_out,
    uint32_t *available_length_out)
{
    const uint8_t *rom_base = rom_data + offset;
    uint32_t available_length = active_rom_size;

    // For SD-loaded ROMs rom_data points at PSRAM (sd_rom_region.ptr) with
    // offset 0; for flash-resident ROMs it points at QSPI flash. In both
    // cases we copy the leading rom_cache_capacity bytes into the PSRAM ROM
    // cache, leaving the tail to be served from the source via XIP.
    if (preferred_size != 0u && (available_length == 0u || available_length > preferred_size))
    {
        available_length = preferred_size;
    }

    if (cache_enable && available_length > 0u && psram_prepare_rom_cache())
    {
        uint32_t cap = rom_cache_capacity;
        if (cap > CACHE_SIZE) cap = CACHE_SIZE;
        uint32_t bytes_to_cache = (available_length > cap) ? cap : available_length;

        gpio_init(PIN_WAIT);
        gpio_set_dir(PIN_WAIT, GPIO_OUT);
        gpio_put(PIN_WAIT, 0);

        // DMA bulk copy from flash XIP to SRAM (matches multirom). A
        // CPU memcpy() can stall or get truncated for large transfers
        // when this function runs in the PSRAM/QMI-active path.
        int dma_chan = dma_claim_unused_channel(true);
        dma_channel_config dma_cfg = dma_channel_get_default_config(dma_chan);
        channel_config_set_transfer_data_size(&dma_cfg, DMA_SIZE_8);
        channel_config_set_read_increment(&dma_cfg, true);
        channel_config_set_write_increment(&dma_cfg, true);
        dma_channel_configure(dma_chan, &dma_cfg,
            rom_sram,
            rom_base,
            bytes_to_cache,
            true);
        dma_channel_wait_for_finish_blocking(dma_chan);
        dma_channel_unclaim(dma_chan);
        gpio_set_dir(PIN_WAIT, GPIO_IN);

        rom_cached_size = bytes_to_cache;
        // If we cached everything, we can just point to SRAM
        if (active_rom_size <= cap)
        {
            rom_base = rom_sram;
        }

        // Per-ROM 50/60Hz: patch the launched game's cartridge INIT so the VDP
        // R9 frequency is set right after the BIOS boot, when the ROM's INIT
        // runs. The menu cannot do this itself because the warm RST 00h reset
        // that boots the ROM re-initializes R9. An 11-byte stub injected into
        // the cached header calls the BIOS WRTVDP routine (0x0047) with B=R9
        // value / C=9, then jumps to the original INIT. Using WRTVDP (as the
        // Carnivore2 boot menu does) writes VDP register 9 *and* updates the
        // BIOS R9 shadow RG9SAV (0xFFE8) on MSX2, so games that reload R9 from
        // the shadow via a BIOS screen call keep the requested refresh mode.
        // This runs as the cartridge INIT with the BIOS in page 0, so the
        // direct 0x0047 call is valid. vdp_freq_launch is zeroed for system
        // ROMs so their loaders are never touched; the menu also zeroes the
        // per-ROM value on MSX1 (no R9), so no MSX1 guard is needed here.
        if (vdp_freq_launch != VDP_FREQ_DEFAULT && bytes_to_cache >= 16u &&
            rom_sram[0] == 'A' && rom_sram[1] == 'B')
        {
            uint16_t orig_init = (uint16_t)rom_sram[2] | ((uint16_t)rom_sram[3] << 8);
            if (orig_init >= 0x4000u && orig_init <= 0xBFFFu)
            {
                uint8_t r9 = (vdp_freq_launch == VDP_FREQ_50HZ) ? 0x02u : 0x00u;
                rom_sram[4] = 0x3Eu; rom_sram[5] = r9;                           // ld a,r9
                rom_sram[6] = 0x47u;                                             // ld b,a
                rom_sram[7] = 0x0Eu; rom_sram[8] = 0x09u;                        // ld c,9
                rom_sram[9] = 0xCDu; rom_sram[10] = 0x47u; rom_sram[11] = 0x00u; // call 0047h (WRTVDP)
                rom_sram[12] = 0xC3u;                                            // jp orig_init
                rom_sram[13] = (uint8_t)(orig_init & 0xFFu);
                rom_sram[14] = (uint8_t)(orig_init >> 8);
                rom_sram[2] = 0x04u; rom_sram[3] = 0x40u;                        // INIT vector -> 0x4004
            }
        }
    }
    else
    {
        rom_cached_size = 0;
    }

    *rom_base_out = rom_base;
    *available_length_out = available_length;
}

static inline void __not_in_flash_func(prepare_sunrise_mapper_rom_source)(
    uint32_t offset,
    bool cache_enable,
    const uint8_t **rom_base_out,
    uint32_t *available_length_out)
{
    const uint8_t *rom_base = rom_data + offset;
    uint32_t available_length = active_rom_size;

    if (cache_enable && available_length > 0u && psram_prepare_rom_cache())
    {
        uint32_t bytes_to_cache = (available_length > CACHE_SIZE)
                                  ? CACHE_SIZE
                                  : available_length;

        int dma_chan = dma_claim_unused_channel(true);
        dma_channel_config dma_cfg = dma_channel_get_default_config(dma_chan);
        channel_config_set_transfer_data_size(&dma_cfg, DMA_SIZE_8);
        channel_config_set_read_increment(&dma_cfg, true);
        channel_config_set_write_increment(&dma_cfg, true);
        dma_channel_configure(dma_chan, &dma_cfg,
            rom_sram,
            rom_base,
            bytes_to_cache,
            true);
        dma_channel_wait_for_finish_blocking(dma_chan);
        dma_channel_unclaim(dma_chan);

        rom_cached_size = bytes_to_cache;
        if (available_length <= CACHE_SIZE)
        {
            rom_base = rom_sram;
        }
    }
    else
    {
        rom_cached_size = 0;
    }

    *rom_base_out = rom_base;
    *available_length_out = available_length;
}
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
