taupter/msx-picoverse-public/2350/software/loadrom.pio/pico/loadrom/loadrom.c

// MSX PICOVERSE PROJECT
// (c) 2026 Cristiano Goncalves
// The Retro Hacker
//
// loadrom.c - PIO-based ROM loader for MSX PICOVERSE project - v2.0
//
// This program loads ROM images using the MSX PICOVERSE project with the RP2350 PIO
// (Programmable I/O) hardware to handle MSX bus timing deterministically.
// The PIO state machines monitor /SLTSL and /RD//WR signals, assert /WAIT to freeze
// the Z80, and exchange address/data with the CPU through FIFOs. This frees the CPU
// from tight bit-banging loops and guarantees timing via the /WAIT mechanism.
//
// You need to concatenate the ROM image to the end of this program binary in order to load it.
// The program will then act as a simple ROM cartridge that responds to memory read requests from the MSX.
//
// This work is licensed under a "Creative Commons Attribution-NonCommercial-ShareAlike 4.0 International
// License". https://creativecommons.org/licenses/by-nc-sa/4.0/

#include <string.h>
#include "pico/stdlib.h"
#include "pico/multicore.h"
#include "hardware/clocks.h"
#include "hardware/dma.h"
#include "hardware/pio.h"
#include "hardware/regs/qmi.h"
#include "hardware/sync.h"
#include "hardware/structs/qmi.h"
#include "hardware/structs/xip_ctrl.h"
#include "loadrom.h"
#include "emu2212.h"
#include "msx_bus.pio.h"
#include "hardware/uart.h"
#include "hardware/gpio.h"
#include "hardware/irq.h"
#include "pico/audio_i2s.h"
#include "sunrise_ide.h"
#include "sunrise_sd.h"
#include "c2_emu.h"

// -----------------------------------------------------------------------
// PIO bus context
// -----------------------------------------------------------------------
typedef struct {
    PIO pio;
    uint sm_read;
    uint sm_write;
    uint offset_read;
    uint offset_write;
} msx_pio_bus_t;

static msx_pio_bus_t msx_bus;
static bool msx_bus_programs_loaded = false;

// I/O bus context (PIO1) for memory mapper port access
typedef struct {
    PIO pio_read;
    PIO pio_write;
    uint sm_io_read;
    uint sm_io_write;
    uint offset_io_read;
    uint offset_io_write;
} msx_pio_io_bus_t;

static msx_pio_io_bus_t msx_io_bus;
static bool msx_io_bus_programs_loaded = false;

// Tracks how many bytes of the ROM are cached in SRAM (0 = no cache)
static uint32_t rom_cached_size = 0;

// Effective SRAM cache capacity (may be reduced by mappers that reserve
// part of the SRAM pool for writable flash sectors, e.g. Manbow2).
static uint32_t rom_cache_capacity = CACHE_SIZE;

// -----------------------------------------------------------------------
// SCC emulation state + I2S audio
// -----------------------------------------------------------------------
#define SCC_VOLUME_SHIFT 2  // Left-shift SCC output for volume boost (4x)
#define SCC_AUDIO_BUFFER_SAMPLES 256

static SCC scc_instance;
static struct audio_buffer_pool *audio_pool;
static bool scc_audio_ready = false;
static int scc_dma_channel = -1;

// -----------------------------------------------------------------------
// Sunrise WiFi memio backend
// -----------------------------------------------------------------------
#define WIFI_MEM_F2_ADDR      0x7F05u
#define WIFI_MEM_CMD_ADDR     0x7F06u
#define WIFI_MEM_DATA_ADDR    0x7F07u
#define WIFI_RX_FIFO_SIZE     2080u
#define WIFI_QUICK_WAIT_US    25000u
#define WIFI_UART_DEFAULT_BAUD 859372u
#define WIFI_STATUS_RX_READY  0x01u
#define WIFI_STATUS_TX_BUSY   0x02u
#define WIFI_STATUS_RX_FULL   0x04u
#define WIFI_STATUS_QUICK_RX  0x08u
#define WIFI_STATUS_UNDERRUN  0x10u
#define WIFI_STATUS_FREE_BITS 0x80u

// Hardware UART1 backs the ESP-01 link on Core2350B GPIO38/39.
// On RP2350B these are UART1 TX/RX on FUNCSEL=11 (GPIO_FUNC_UART_AUX).
// FUNCSEL=2 on these pins maps to UART1 CTS/RTS, NOT data.
#define WIFI_UART_INSTANCE uart1
static uint8_t wifi_rx_fifo[WIFI_RX_FIFO_SIZE];
static volatile uint16_t wifi_rx_head = 0u;
static volatile uint16_t wifi_rx_tail = 0u;
static volatile uint16_t wifi_rx_count = 0u;
static uint8_t wifi_f2_state = 0xFFu;
static bool wifi_uart_ready = false;
static uint32_t wifi_uart_baud = WIFI_UART_DEFAULT_BAUD;
static uint32_t wifi_tx_busy_deadline_us = 0u;
static bool wifi_rx_underrun = false;

static inline void __not_in_flash_func(wifi_reset_fifo)(void)
{
    uint32_t irq_state = save_and_disable_interrupts();
    wifi_rx_head = 0u;
    wifi_rx_tail = 0u;
    wifi_rx_count = 0u;
    wifi_rx_underrun = false;
    restore_interrupts(irq_state);
}

static inline void __not_in_flash_func(wifi_push_rx_byte)(uint8_t data)
{
    // Producer side: called from UART RX IRQ on core0. The pop side
    // disables IRQs while it mutates head/tail/count, so we don't race.
    if (wifi_rx_count >= WIFI_RX_FIFO_SIZE)
    {
        return;
    }

    wifi_rx_fifo[wifi_rx_head] = data;
    wifi_rx_head = (uint16_t)((wifi_rx_head + 1u) % WIFI_RX_FIFO_SIZE);
    ++wifi_rx_count;
}

static inline bool __not_in_flash_func(wifi_pop_rx_byte)(uint8_t *data_out)
{
    uint32_t irq_state = save_and_disable_interrupts();
    if (wifi_rx_count == 0u)
    {
        restore_interrupts(irq_state);
        return false;
    }

    *data_out = wifi_rx_fifo[wifi_rx_tail];
    wifi_rx_tail = (uint16_t)((wifi_rx_tail + 1u) % WIFI_RX_FIFO_SIZE);
    --wifi_rx_count;
    restore_interrupts(irq_state);
    return true;
}

static inline bool __not_in_flash_func(wifi_hw_tx_busy)(void)
{
    return (uart_get_hw(WIFI_UART_INSTANCE)->fr & UART_UARTFR_BUSY_BITS) != 0u;
}

static inline void __not_in_flash_func(wifi_hw_rx_drain)(void)
{
    while (uart_is_readable(WIFI_UART_INSTANCE))
    {
        (void)uart_getc(WIFI_UART_INSTANCE);
    }
}

static inline void __not_in_flash_func(wifi_pio_rx_reset)(void)
{
    // Drain any in-flight bytes; FIFO will refill from the wire.
    wifi_hw_rx_drain();
}

static inline void __not_in_flash_func(wifi_pio_tx_reset)(void)
{
    // Wait for the TX shifter to flush so we don't truncate a frame.
    while (wifi_hw_tx_busy())
    {
    }
    wifi_tx_busy_deadline_us = 0u;
}

static inline void __not_in_flash_func(wifi_service_rx)(void)
{
    if (!wifi_uart_ready)
    {
        return;
    }

    while (wifi_rx_count < WIFI_RX_FIFO_SIZE && uart_is_readable(WIFI_UART_INSTANCE))
    {
        wifi_push_rx_byte((uint8_t)uart_getc(WIFI_UART_INSTANCE));
    }
}

// IRQ handler: drains UART1 RX hardware FIFO into the SW FIFO. Runs on
// core0 (the core that calls wifi_uart_init_once). Must be in RAM so it
// is not blocked by XIP cache misses while the bus loop is busy.
static void __not_in_flash_func(wifi_uart_rx_irq)(void)
{
    while (uart_is_readable(WIFI_UART_INSTANCE))
    {
        uint8_t b = (uint8_t)uart_getc(WIFI_UART_INSTANCE);
        if (wifi_rx_count < WIFI_RX_FIFO_SIZE)
        {
            wifi_rx_fifo[wifi_rx_head] = b;
            wifi_rx_head = (uint16_t)((wifi_rx_head + 1u) % WIFI_RX_FIFO_SIZE);
            ++wifi_rx_count;
        }
    }
}

static inline uint32_t __not_in_flash_func(wifi_uart_frame_time_us)(void)
{
    return (10000000u + (wifi_uart_baud - 1u)) / wifi_uart_baud;
}

static inline void __not_in_flash_func(wifi_uart_init_once)(void)
{
    if (wifi_uart_ready)
    {
        return;
    }

    // Initialise hardware UART1 on GPIO38 (TX) / GPIO39 (RX). Both pins
    // need GPIO_FUNC_UART_AUX (FUNCSEL=11) on RP2350B; the default
    // GPIO_FUNC_UART (FUNCSEL=2) maps to UART1 CTS/RTS on these pins.
    (void)uart_init(WIFI_UART_INSTANCE, wifi_uart_baud);
    gpio_set_function(PIN_ESP_UART_TX, GPIO_FUNC_UART_AUX);
    gpio_set_function(PIN_ESP_UART_RX, GPIO_FUNC_UART_AUX);
    uart_set_format(WIFI_UART_INSTANCE, 8, 1, UART_PARITY_NONE);
    uart_set_hw_flow(WIFI_UART_INSTANCE, false, false);
    uart_set_fifo_enabled(WIFI_UART_INSTANCE, true);

    // Drain any spurious bytes the line may have latched during init.
    wifi_hw_rx_drain();

    wifi_f2_state = 0xFFu;
    wifi_reset_fifo();
    wifi_tx_busy_deadline_us = 0u;
    wifi_uart_ready = true;

    // IRQ-driven RX: at 859372 baud the 32-byte HW FIFO fills in ~370us.
    // Polling from the bus service loop is not reliable when the loop
    // stalls on pio_sm_put_blocking, so route the RX/RT interrupts to a
    // dedicated handler that drains the FIFO immediately. RT (receive
    // timeout) ensures partial bursts don't sit in the FIFO.
    int uart_irq = (WIFI_UART_INSTANCE == uart0) ? UART0_IRQ : UART1_IRQ;
    irq_set_exclusive_handler(uart_irq, wifi_uart_rx_irq);
    irq_set_enabled(uart_irq, true);
    uart_set_irq_enables(WIFI_UART_INSTANCE, true, false);
}

static inline void __not_in_flash_func(wifi_handle_cmd_write)(uint8_t cmd)
{
    wifi_uart_init_once();

    if (cmd == 20u)
    {
        wifi_reset_fifo();
        wifi_pio_tx_reset();
        wifi_pio_rx_reset();
    }
}

static inline uint8_t __not_in_flash_func(wifi_status_read)(void)
{
    wifi_uart_init_once();
    wifi_service_rx();

    uint8_t status = WIFI_STATUS_QUICK_RX | WIFI_STATUS_FREE_BITS;
    if (wifi_rx_count != 0u)
    {
        status |= WIFI_STATUS_RX_READY;
    }
    if (wifi_rx_count >= WIFI_RX_FIFO_SIZE)
    {
        status |= WIFI_STATUS_RX_FULL;
    }
    if (wifi_hw_tx_busy() ||
        !uart_is_writable(WIFI_UART_INSTANCE) ||
        (int32_t)(time_us_32() - wifi_tx_busy_deadline_us) < 0)
    {
        status |= WIFI_STATUS_TX_BUSY;
    }
    if (wifi_rx_underrun)
    {
        status |= WIFI_STATUS_UNDERRUN;
        wifi_rx_underrun = false;
    }

    return status;
}

static inline uint8_t __not_in_flash_func(wifi_data_read)(void)
{
    wifi_uart_init_once();

    uint8_t data;
    wifi_service_rx();
    if (wifi_pop_rx_byte(&data))
    {
        return data;
    }

    uint32_t deadline = time_us_32() + WIFI_QUICK_WAIT_US;
    while ((int32_t)(time_us_32() - deadline) < 0)
    {
        wifi_service_rx();
        if (wifi_pop_rx_byte(&data))
        {
            return data;
        }
    }

    wifi_rx_underrun = true;
    return 0xFFu;
}

static inline bool __not_in_flash_func(wifi_handle_mem_write)(uint16_t addr, uint8_t data)
{
    if (addr == WIFI_MEM_F2_ADDR)
    {
        wifi_f2_state = data;
        return true;
    }
    if (addr == WIFI_MEM_CMD_ADDR)
    {
        wifi_handle_cmd_write(data);
        return true;
    }
    if (addr == WIFI_MEM_DATA_ADDR)
    {
        wifi_uart_init_once();
        uart_putc_raw(WIFI_UART_INSTANCE, (char)data);
        wifi_tx_busy_deadline_us = time_us_32() + wifi_uart_frame_time_us();
        return true;
    }

    return false;
}

static inline uint8_t __not_in_flash_func(wifi_read_rom_byte)(const uint8_t *wifi_rom_base, uint16_t addr)
{
    uint32_t rel = (uint32_t)(addr - 0x4000u);
    if (rel < WIFI_ROM_SIZE)
    {
        return wifi_rom_base[rel];
    }

    return 0xFFu;
}

static inline uint8_t __not_in_flash_func(wifi_handle_mem_read)(const uint8_t *wifi_rom_base, uint16_t addr)
{
    if (addr == WIFI_MEM_F2_ADDR)
    {
        return wifi_f2_state;
    }
    if (addr == WIFI_MEM_CMD_ADDR)
    {
        return wifi_data_read();
    }
    if (addr == WIFI_MEM_DATA_ADDR)
    {
        return wifi_status_read();
    }

    return wifi_read_rom_byte(wifi_rom_base, addr);
}

// -----------------------------------------------------------------------
// External PSRAM mapper backing (QMI CS1)
// -----------------------------------------------------------------------
static inline void __not_in_flash_func(psram_delay_cycles)(uint32_t cycles)
{
    for (volatile uint32_t cycle = 0; cycle < cycles; ++cycle)
    {
        __asm volatile ("nop");
    }
}

static inline void __not_in_flash_func(psram_wait_direct_done)(void)
{
    while ((qmi_hw->direct_csr & QMI_DIRECT_CSR_TXEMPTY_BITS) == 0)
    {
    }
    while ((qmi_hw->direct_csr & QMI_DIRECT_CSR_BUSY_BITS) != 0)
    {
    }
}

static inline void __not_in_flash_func(psram_send_direct_cmd)(uint8_t cmd, bool quad_width)
{
    qmi_hw->direct_csr |= QMI_DIRECT_CSR_ASSERT_CS1N_BITS;
    if (quad_width)
    {
        qmi_hw->direct_tx = QMI_DIRECT_TX_OE_BITS |
                            (QMI_DIRECT_TX_IWIDTH_VALUE_Q << QMI_DIRECT_TX_IWIDTH_LSB) |
                            cmd;
    }
    else
    {
        qmi_hw->direct_tx = cmd;
    }
    psram_wait_direct_done();
    qmi_hw->direct_csr &= ~QMI_DIRECT_CSR_ASSERT_CS1N_BITS;
    (void)qmi_hw->direct_rx;
}

static bool __no_inline_not_in_flash_func(psram_init)(void)
{
    gpio_set_function(PIN_PSRAM, GPIO_FUNC_XIP_CS1);

    uint32_t irq_state = save_and_disable_interrupts();

    qmi_hw->direct_csr = (30u << QMI_DIRECT_CSR_CLKDIV_LSB) | QMI_DIRECT_CSR_EN_BITS;
    while ((qmi_hw->direct_csr & QMI_DIRECT_CSR_BUSY_BITS) != 0)
    {
    }

    // Warm restart path: if PSRAM remained powered it may still be in QPI mode.
    psram_send_direct_cmd(0xF5u, true);
    psram_delay_cycles(128u);

    psram_send_direct_cmd(0x66u, false);
    psram_delay_cycles(128u);
    psram_send_direct_cmd(0x99u, false);
    psram_delay_cycles(50000u);
    psram_send_direct_cmd(0x35u, false);
    psram_delay_cycles(128u);
    psram_send_direct_cmd(0xC0u, false);
    psram_delay_cycles(128u);

    qmi_hw->direct_csr &= ~(QMI_DIRECT_CSR_ASSERT_CS1N_BITS | QMI_DIRECT_CSR_EN_BITS);

    // PSRAM QMI timing — tuned for 210 MHz system clock.
    // CLKDIV=2 → SCK = 52.5 MHz (safe for all APS6404L/IPS6404L grades).
    // SELECT_HOLD=1 → 4.76 ns ≥ 3 ns tCSS.
    // MIN_DESELECT=5 → 23.8 ns ≥ 18 ns tCPH.
    // RXDELAY=2 → sample at 9.52 ns after SCK rise (mid-cycle at CLKDIV=2).
    // Performance comes from the XIP cache (PSRAM_BASE_ADDR = 0x11000000,
    // cached write-through window) rather than raw QSPI throughput.
    qmi_hw->m[1].timing =
        (QMI_M0_TIMING_PAGEBREAK_VALUE_1024 << QMI_M0_TIMING_PAGEBREAK_LSB) |
        (1u << QMI_M0_TIMING_SELECT_HOLD_LSB) |
        (1u << QMI_M0_TIMING_COOLDOWN_LSB) |
        (2u << QMI_M0_TIMING_RXDELAY_LSB) |
        (26u << QMI_M0_TIMING_MAX_SELECT_LSB) |
        (5u << QMI_M0_TIMING_MIN_DESELECT_LSB) |
        (2u << QMI_M0_TIMING_CLKDIV_LSB);
    qmi_hw->m[1].rfmt =
        (QMI_M0_RFMT_PREFIX_WIDTH_VALUE_Q << QMI_M0_RFMT_PREFIX_WIDTH_LSB) |
        (QMI_M0_RFMT_ADDR_WIDTH_VALUE_Q << QMI_M0_RFMT_ADDR_WIDTH_LSB) |
        (QMI_M0_RFMT_SUFFIX_WIDTH_VALUE_Q << QMI_M0_RFMT_SUFFIX_WIDTH_LSB) |
        (QMI_M0_RFMT_DUMMY_WIDTH_VALUE_Q << QMI_M0_RFMT_DUMMY_WIDTH_LSB) |
        (QMI_M0_RFMT_DUMMY_LEN_VALUE_24 << QMI_M0_RFMT_DUMMY_LEN_LSB) |
        (QMI_M0_RFMT_DATA_WIDTH_VALUE_Q << QMI_M0_RFMT_DATA_WIDTH_LSB) |
        (QMI_M0_RFMT_PREFIX_LEN_VALUE_8 << QMI_M0_RFMT_PREFIX_LEN_LSB) |
        (QMI_M0_RFMT_SUFFIX_LEN_VALUE_NONE << QMI_M0_RFMT_SUFFIX_LEN_LSB);
    qmi_hw->m[1].rcmd = (0xEBu << QMI_M0_RCMD_PREFIX_LSB);
    qmi_hw->m[1].wfmt =
        (QMI_M0_WFMT_PREFIX_WIDTH_VALUE_Q << QMI_M0_WFMT_PREFIX_WIDTH_LSB) |
        (QMI_M0_WFMT_ADDR_WIDTH_VALUE_Q << QMI_M0_WFMT_ADDR_WIDTH_LSB) |
        (QMI_M0_WFMT_SUFFIX_WIDTH_VALUE_Q << QMI_M0_WFMT_SUFFIX_WIDTH_LSB) |
        (QMI_M0_WFMT_DUMMY_WIDTH_VALUE_Q << QMI_M0_WFMT_DUMMY_WIDTH_LSB) |
        (QMI_M0_WFMT_DUMMY_LEN_VALUE_NONE << QMI_M0_WFMT_DUMMY_LEN_LSB) |
        (QMI_M0_WFMT_DATA_WIDTH_VALUE_Q << QMI_M0_WFMT_DATA_WIDTH_LSB) |
        (QMI_M0_WFMT_PREFIX_LEN_VALUE_8 << QMI_M0_WFMT_PREFIX_LEN_LSB) |
        (QMI_M0_WFMT_SUFFIX_LEN_VALUE_NONE << QMI_M0_WFMT_SUFFIX_LEN_LSB);
    qmi_hw->m[1].wcmd = (0x38u << QMI_M0_WCMD_PREFIX_LSB);

    xip_ctrl_hw->ctrl |= XIP_CTRL_WRITABLE_M1_BITS;

    restore_interrupts(irq_state);

    // Verify PSRAM is functional via uncached window (bypass XIP cache
    // to guarantee the write reaches the device and the read comes back
    // from the device, not from a stale cache line).
    volatile uint32_t *psram_test = (volatile uint32_t *)0x15000000u;
    psram_test[0] = 0x12345678u;
    return psram_test[0] == 0x12345678u;
}

// -----------------------------------------------------------------------
// PSRAM Memory Manager — bump allocator for 8MB external PSRAM
// -----------------------------------------------------------------------
static psram_region_t mapper_region;
static psram_region_t c2_rom_region;

static struct {
    uint32_t next_free;
} psram_mgr;

static void psram_mem_init(void)
{
    psram_mgr.next_free = 0;
    memset(&mapper_region, 0, sizeof(mapper_region));
    memset(&c2_rom_region, 0, sizeof(c2_rom_region));
}

static bool psram_alloc(uint32_t size, psram_region_t *region)
{
    if (psram_mgr.next_free + size > PSRAM_TOTAL_SIZE)
        return false;
    region->offset = psram_mgr.next_free;
    region->size = size;
    region->ptr = (uint8_t *)(PSRAM_BASE_ADDR + psram_mgr.next_free);
    psram_mgr.next_free += size;
    return true;
}

static void psram_free_all(void)
{
    psram_mgr.next_free = 0;
    memset(&mapper_region, 0, sizeof(mapper_region));
    memset(&c2_rom_region, 0, sizeof(c2_rom_region));
}

// -----------------------------------------------------------------------
// PSRAM region helpers — mapper RAM
// -----------------------------------------------------------------------
static void __not_in_flash_func(mapper_fill_ff)(void)
{
    uint32_t *words = (uint32_t *)mapper_region.ptr;
    for (uint32_t index = 0; index < (mapper_region.size / sizeof(uint32_t)); ++index)
    {
        words[index] = 0xFFFFFFFFu;
    }
}

static inline void __not_in_flash_func(mapper_write_byte)(uint32_t offset, uint8_t data)
{
    mapper_region.ptr[offset] = data;
}

static inline uint8_t __not_in_flash_func(mapper_read_byte)(uint32_t offset)
{
    return mapper_region.ptr[offset];
}

// -----------------------------------------------------------------------
// ROM source preparation (cache to SRAM, flash fallback for large ROMs)
// -----------------------------------------------------------------------
// For ROMs that fit in the 192KB SRAM cache, the entire ROM is copied to
// SRAM and rom_base is redirected there. For ROMs larger than the cache,
// the first 192KB is cached in SRAM and rom_base stays pointing to flash.
// read_rom_byte() transparently serves from SRAM for offsets within the
// cached region and falls back to flash XIP for the rest.
static inline void __not_in_flash_func(prepare_rom_source)(
    uint32_t offset,
    bool cache_enable,
    uint32_t preferred_size,
    const uint8_t **rom_base_out,
    uint32_t *available_length_out)
{
    const uint8_t *rom_base = rom + offset;
    uint32_t available_length = active_rom_size;

    if (preferred_size != 0u && (available_length == 0u || available_length > preferred_size))
    {
        available_length = preferred_size;
    }

    if (cache_enable && available_length > 0u)
    {
        uint32_t bytes_to_cache = (available_length > rom_cache_capacity)
                                  ? rom_cache_capacity
                                  : available_length;

        gpio_init(PIN_WAIT);
        gpio_set_dir(PIN_WAIT, GPIO_OUT);
        gpio_put(PIN_WAIT, 0);

        // DMA bulk copy from flash/PSRAM XIP to SRAM.
        // Byte transfers are used because rom_base may not be 4-byte aligned
        // (ROM data starts at __flash_binary_end + 55-byte header).
        int dma_chan = dma_claim_unused_channel(true);
        dma_channel_config dma_cfg = dma_channel_get_default_config(dma_chan);
        channel_config_set_transfer_data_size(&dma_cfg, DMA_SIZE_8);
        channel_config_set_read_increment(&dma_cfg, true);
        channel_config_set_write_increment(&dma_cfg, true);
        dma_channel_configure(dma_chan, &dma_cfg,
            rom_sram,                        // write address (SRAM)
            rom_base,                        // read address (flash/PSRAM XIP)
            bytes_to_cache,                  // transfer count (bytes)
            true);                           // start immediately
        dma_channel_wait_for_finish_blocking(dma_chan);
        dma_channel_unclaim(dma_chan);
        // WAIT stays asserted; msx_pio_bus_init() will release it
        // atomically when the read SM starts (side-set 1 on first
        // instruction), guaranteeing PIO is ready before the MSX resumes.

        rom_cached_size = bytes_to_cache;

        if (available_length <= rom_cache_capacity)
        {
            // Entire ROM fits in SRAM cache
            rom_base = rom_sram;
        }
    }
    else
    {
        rom_cached_size = 0;
    }

    *rom_base_out = rom_base;
    *available_length_out = available_length;
}

static inline void __not_in_flash_func(prepare_sunrise_mapper_rom_source)(
    uint32_t offset,
    bool cache_enable,
    const uint8_t **rom_base_out,
    uint32_t *available_length_out)
{
    // On RP2350 the mapper RAM lives in external PSRAM, so the internal
    // 256KB SRAM cache can be used for the embedded Nextor ROM as well.
    // The caller has already frozen the MSX bus with /WAIT asserted, so
    // this path must not release /WAIT while the cache DMA is running.
    const uint8_t *rom_base = rom + offset;
    uint32_t available_length = active_rom_size;

    rom_cache_capacity = CACHE_SIZE;

    if (cache_enable && available_length > 0u)
    {
        uint32_t bytes_to_cache = (available_length > rom_cache_capacity)
                                  ? rom_cache_capacity
                                  : available_length;

        int dma_chan = dma_claim_unused_channel(true);
        dma_channel_config dma_cfg = dma_channel_get_default_config(dma_chan);
        channel_config_set_transfer_data_size(&dma_cfg, DMA_SIZE_8);
        channel_config_set_read_increment(&dma_cfg, true);
        channel_config_set_write_increment(&dma_cfg, true);
        dma_channel_configure(dma_chan, &dma_cfg,
            rom_sram,
            rom_base,
            bytes_to_cache,
            true);
        dma_channel_wait_for_finish_blocking(dma_chan);
        dma_channel_unclaim(dma_chan);

        rom_cached_size = bytes_to_cache;

        if (available_length <= rom_cache_capacity)
        {
            rom_base = rom_sram;
        }
    }
    else
    {
        rom_cached_size = 0;
    }

    *rom_base_out = rom_base;
    *available_length_out = available_length;
}

// -----------------------------------------------------------------------
// GPIO initialisation (address, data, control pins)
// -----------------------------------------------------------------------
static inline void setup_gpio(void)
{
    // Address pins A0-A15 as inputs
    for (uint pin = PIN_A0; pin <= PIN_A15; ++pin)
    {
        gpio_init(pin);
        gpio_set_input_hysteresis_enabled(pin, true);
        gpio_set_dir(pin, GPIO_IN);
    }

    // Data pins D0-D7 (will be managed by PIO)
    for (uint pin = PIN_D0; pin <= PIN_D7; ++pin)
    {
        gpio_init(pin);
        gpio_set_input_hysteresis_enabled(pin, true);
    }

    // Control signals as inputs
    gpio_init(PIN_RD);      gpio_set_dir(PIN_RD, GPIO_IN);
    gpio_init(PIN_WR);      gpio_set_dir(PIN_WR, GPIO_IN);
    gpio_init(PIN_IORQ);    gpio_set_dir(PIN_IORQ, GPIO_IN);
    gpio_init(PIN_SLTSL);   gpio_set_dir(PIN_SLTSL, GPIO_IN);
    gpio_init(PIN_BUSSDIR); gpio_set_dir(PIN_BUSSDIR, GPIO_IN);
    gpio_init(PIN_PSRAM);   gpio_set_dir(PIN_PSRAM, GPIO_IN);
}

// -----------------------------------------------------------------------
// PIO bus initialisation
// -----------------------------------------------------------------------
static void msx_pio_bus_init(void)
{
    msx_bus.pio = pio0;
    msx_bus.sm_read  = 0;
    msx_bus.sm_write = 1;

    if (!msx_bus_programs_loaded)
    {
        msx_bus.offset_read  = pio_add_program(msx_bus.pio, &msx_read_responder_program);
        msx_bus.offset_write = pio_add_program(msx_bus.pio, &msx_write_captor_program);
        msx_bus_programs_loaded = true;
    }

    pio_sm_set_enabled(msx_bus.pio, msx_bus.sm_read, false);
    pio_sm_set_enabled(msx_bus.pio, msx_bus.sm_write, false);
    pio_sm_clear_fifos(msx_bus.pio, msx_bus.sm_read);
    pio_sm_clear_fifos(msx_bus.pio, msx_bus.sm_write);
    pio_sm_restart(msx_bus.pio, msx_bus.sm_read);
    pio_sm_restart(msx_bus.pio, msx_bus.sm_write);

    // ----- Read responder SM (SM0) -----
    pio_sm_config cfg_read = msx_read_responder_program_get_default_config(msx_bus.offset_read);
    sm_config_set_in_pins(&cfg_read, PIN_A0);                // in base = GPIO 0
    sm_config_set_in_shift(&cfg_read, false, false, 16);     // shift left, no autopush, 16 bits
    sm_config_set_out_pins(&cfg_read, PIN_D0, 8);            // out base = GPIO 16, 8 pins
    sm_config_set_out_shift(&cfg_read, true, false, 32);     // shift right (LSB first), no autopull
    sm_config_set_sideset_pins(&cfg_read, PIN_WAIT);         // side-set = GPIO 28
    sm_config_set_jmp_pin(&cfg_read, PIN_RD);                // jmp pin = /RD for polling
    sm_config_set_clkdiv(&cfg_read, 1.0f);                   // Run at full system clock
    pio_sm_init(msx_bus.pio, msx_bus.sm_read, msx_bus.offset_read, &cfg_read);

    // ----- Write captor SM (SM1) -----
    pio_sm_config cfg_write = msx_write_captor_program_get_default_config(msx_bus.offset_write);
    sm_config_set_in_pins(&cfg_write, PIN_A0);               // in base = GPIO 0
    sm_config_set_in_shift(&cfg_write, false, false, 32);    // shift left, no autopush, 32 bits
    sm_config_set_fifo_join(&cfg_write, PIO_FIFO_JOIN_RX);   // Join FIFOs for 8-deep RX buffer
    sm_config_set_jmp_pin(&cfg_write, PIN_WR);               // jmp pin = /WR for polling
    sm_config_set_clkdiv(&cfg_write, 1.0f);
    pio_sm_init(msx_bus.pio, msx_bus.sm_write, msx_bus.offset_write, &cfg_write);

    // ----- Pin configuration for PIO -----
    // /WAIT pin: PIO side-set output, initially deasserted (high)
    pio_gpio_init(msx_bus.pio, PIN_WAIT);
    pio_sm_set_consecutive_pindirs(msx_bus.pio, msx_bus.sm_read, PIN_WAIT, 1, true);

    // Data pins: hand over to PIO, initially tri-stated (input)
    for (uint pin = PIN_D0; pin <= PIN_D7; ++pin)
    {
        pio_gpio_init(msx_bus.pio, pin);
    }
    pio_sm_set_consecutive_pindirs(msx_bus.pio, msx_bus.sm_read, PIN_D0, 8, false);
    pio_sm_set_consecutive_pindirs(msx_bus.pio, msx_bus.sm_write, PIN_D0, 8, false);

    // Ensure /WAIT starts high before enabling state machines
    gpio_put(PIN_WAIT, 1);

    // Enable both state machines
    pio_sm_set_enabled(msx_bus.pio, msx_bus.sm_read, true);
    pio_sm_set_enabled(msx_bus.pio, msx_bus.sm_write, true);
}

// -----------------------------------------------------------------------
// PIO I/O bus initialisation (for memory mapper port access on PIO1)
// -----------------------------------------------------------------------
static void msx_pio_io_bus_init(void)
{
    msx_io_bus.pio_read = pio1;
    msx_io_bus.pio_write = pio1;
    msx_io_bus.sm_io_read  = 0;
    msx_io_bus.sm_io_write = 1;

    if (!msx_io_bus_programs_loaded)
    {
        msx_io_bus.offset_io_read = pio_add_program(msx_io_bus.pio_read, &msx_io_read_responder_program);
        msx_io_bus.offset_io_write = pio_add_program(msx_io_bus.pio_write, &msx_io_write_captor_program);
        msx_io_bus_programs_loaded = true;
    }

    pio_sm_set_enabled(msx_io_bus.pio_read, msx_io_bus.sm_io_read, false);
    pio_sm_set_enabled(msx_io_bus.pio_write, msx_io_bus.sm_io_write, false);
    pio_sm_clear_fifos(msx_io_bus.pio_read, msx_io_bus.sm_io_read);
    pio_sm_clear_fifos(msx_io_bus.pio_write, msx_io_bus.sm_io_write);
    pio_sm_restart(msx_io_bus.pio_read, msx_io_bus.sm_io_read);
    pio_sm_restart(msx_io_bus.pio_write, msx_io_bus.sm_io_write);

    pio_sm_config cfg_io_read = msx_io_read_responder_program_get_default_config(msx_io_bus.offset_io_read);
    sm_config_set_in_pins(&cfg_io_read, PIN_A0);
    sm_config_set_in_shift(&cfg_io_read, false, false, 16);
    sm_config_set_out_pins(&cfg_io_read, PIN_D0, 8);
    sm_config_set_out_shift(&cfg_io_read, true, false, 32);
    sm_config_set_jmp_pin(&cfg_io_read, PIN_RD);
    sm_config_set_clkdiv(&cfg_io_read, 1.0f);
    pio_sm_init(msx_io_bus.pio_read, msx_io_bus.sm_io_read, msx_io_bus.offset_io_read, &cfg_io_read);

    pio_sm_config cfg_io_write = msx_io_write_captor_program_get_default_config(msx_io_bus.offset_io_write);
    sm_config_set_in_pins(&cfg_io_write, PIN_A0);
    sm_config_set_in_shift(&cfg_io_write, false, false, 32);
    sm_config_set_fifo_join(&cfg_io_write, PIO_FIFO_JOIN_RX);
    sm_config_set_jmp_pin(&cfg_io_write, PIN_WR);
    sm_config_set_clkdiv(&cfg_io_write, 1.0f);
    pio_sm_init(msx_io_bus.pio_write, msx_io_bus.sm_io_write, msx_io_bus.offset_io_write, &cfg_io_write);

    pio_sm_set_consecutive_pindirs(msx_io_bus.pio_read, msx_io_bus.sm_io_read, PIN_D0, 8, false);

    pio_sm_set_enabled(msx_io_bus.pio_read, msx_io_bus.sm_io_read, true);
    pio_sm_set_enabled(msx_io_bus.pio_write, msx_io_bus.sm_io_write, true);
}

// -----------------------------------------------------------------------
// Token helpers
// -----------------------------------------------------------------------

// Read a byte from the ROM, using SRAM cache when possible, flash otherwise.
static inline uint8_t __not_in_flash_func(read_rom_byte)(const uint8_t *rom_base, uint32_t rel)
{
    return (rel < rom_cached_size) ? rom_sram[rel] : rom_base[rel];
}

// Build a 16-bit token to send back to the read SM via TX FIFO.
//   bits[7:0]  = data byte
//   bits[15:8] = pindirs mask (0xFF = drive bus, 0x00 = tri-state)
static inline uint16_t __not_in_flash_func(pio_build_token)(bool drive, uint8_t data)
{
    uint8_t dir_mask = drive ? 0xFFu : 0x00u;
    return (uint16_t)data | ((uint16_t)dir_mask << 8);
}

// Try to consume a write event from the write captor FIFO.
// Returns false if FIFO is empty.
static inline bool __not_in_flash_func(pio_try_get_write)(uint16_t *addr_out, uint8_t *data_out)
{
    if (pio_sm_is_rx_fifo_empty(msx_bus.pio, msx_bus.sm_write))
        return false;

    uint32_t sample = pio_sm_get(msx_bus.pio, msx_bus.sm_write);
    *addr_out = (uint16_t)(sample & 0xFFFFu);
    *data_out = (uint8_t)((sample >> 16) & 0xFFu);
    return true;
}

// Drain all pending write events, invoking a handler for each.
static inline void __not_in_flash_func(pio_drain_writes)(void (*handler)(uint16_t addr, uint8_t data, void *ctx), void *ctx)
{
    uint16_t addr;
    uint8_t data;
    while (pio_try_get_write(&addr, &data))
    {
        handler(addr, data, ctx);
    }
}

// Try to consume an I/O write event from the I/O write captor FIFO (PIO1).
// Returns false if FIFO is empty.
static inline bool __not_in_flash_func(pio_try_get_io_write)(uint16_t *addr_out, uint8_t *data_out)
{
    if (pio_sm_is_rx_fifo_empty(msx_io_bus.pio_write, msx_io_bus.sm_io_write))
        return false;

    uint32_t sample = pio_sm_get(msx_io_bus.pio_write, msx_io_bus.sm_io_write);
    *addr_out = (uint16_t)(sample & 0xFFFFu);
    *data_out = (uint8_t)((sample >> 16) & 0xFFu);
    return true;
}

// Map an 8-bit mapper register value to a valid mapper page index.
static inline uint8_t __not_in_flash_func(mapper_page_from_reg)(uint8_t reg)
{
    return (uint8_t)(reg % MAPPER_PAGES);
}

// Try to consume an I/O read event from the I/O read responder FIFO (PIO1).
// Returns false if FIFO is empty.
static inline bool __not_in_flash_func(pio_try_get_io_read)(uint16_t *addr_out)
{
    if (pio_sm_is_rx_fifo_empty(msx_io_bus.pio_read, msx_io_bus.sm_io_read))
        return false;

    *addr_out = (uint16_t)pio_sm_get(msx_io_bus.pio_read, msx_io_bus.sm_io_read);
    return true;
}

// -----------------------------------------------------------------------
// Bank switching write handlers (used by mapper ROM types)
// -----------------------------------------------------------------------

typedef struct {
    uint8_t *bank_regs;
} bank8_ctx_t;

typedef struct {
    uint16_t *bank_regs;
} bank16_ctx_t;

static inline void __not_in_flash_func(handle_konamiscc_write)(uint16_t addr, uint8_t data, void *ctx)
{
    uint8_t *regs = ((bank8_ctx_t *)ctx)->bank_regs;
    if      (addr >= 0x5000u && addr <= 0x57FFu) regs[0] = data;
    else if (addr >= 0x7000u && addr <= 0x77FFu) regs[1] = data;
    else if (addr >= 0x9000u && addr <= 0x97FFu) regs[2] = data;
    else if (addr >= 0xB000u && addr <= 0xB7FFu) regs[3] = data;
}

static inline void __not_in_flash_func(handle_konami_write)(uint16_t addr, uint8_t data, void *ctx)
{
    uint8_t *regs = ((bank8_ctx_t *)ctx)->bank_regs;
    if      (addr >= 0x6000u && addr <= 0x67FFu) regs[1] = data;
    else if (addr >= 0x8000u && addr <= 0x87FFu) regs[2] = data;
    else if (addr >= 0xA000u && addr <= 0xA7FFu) regs[3] = data;
}

static inline void __not_in_flash_func(handle_ascii8_write)(uint16_t addr, uint8_t data, void *ctx)
{
    uint8_t *regs = ((bank8_ctx_t *)ctx)->bank_regs;
    if      (addr >= 0x6000u && addr <= 0x67FFu) regs[0] = data;
    else if (addr >= 0x6800u && addr <= 0x6FFFu) regs[1] = data;
    else if (addr >= 0x7000u && addr <= 0x77FFu) regs[2] = data;
    else if (addr >= 0x7800u && addr <= 0x7FFFu) regs[3] = data;
}

static inline void __not_in_flash_func(handle_ascii16_write)(uint16_t addr, uint8_t data, void *ctx)
{
    uint8_t *regs = ((bank8_ctx_t *)ctx)->bank_regs;
    if      (addr >= 0x6000u && addr <= 0x67FFu) regs[0] = data;
    else if (addr >= 0x7000u && addr <= 0x77FFu) regs[1] = data;
}

static inline void __not_in_flash_func(handle_neo8_write)(uint16_t addr, uint8_t data, void *ctx)
{
    uint16_t *regs = ((bank16_ctx_t *)ctx)->bank_regs;
    uint16_t base_addr = addr & 0xF800u;
    uint8_t bank_index = 6;

    switch (base_addr)
    {
        case 0x5000: case 0x1000: case 0x9000: case 0xD000: bank_index = 0; break;
        case 0x5800: case 0x1800: case 0x9800: case 0xD800: bank_index = 1; break;
        case 0x6000: case 0x2000: case 0xA000: case 0xE000: bank_index = 2; break;
        case 0x6800: case 0x2800: case 0xA800: case 0xE800: bank_index = 3; break;
        case 0x7000: case 0x3000: case 0xB000: case 0xF000: bank_index = 4; break;
        case 0x7800: case 0x3800: case 0xB800: case 0xF800: bank_index = 5; break;
    }

    if (bank_index < 6u)
    {
        if (addr & 0x01u)
            regs[bank_index] = (regs[bank_index] & 0x00FFu) | ((uint16_t)data << 8);
        else
            regs[bank_index] = (regs[bank_index] & 0xFF00u) | data;
        regs[bank_index] &= 0x0FFFu;
    }
}

static inline void __not_in_flash_func(handle_neo16_write)(uint16_t addr, uint8_t data, void *ctx)
{
    uint16_t *regs = ((bank16_ctx_t *)ctx)->bank_regs;
    uint16_t base_addr = addr & 0xF800u;
    uint8_t bank_index = 3;

    switch (base_addr)
    {
        case 0x5000: case 0x1000: case 0x9000: case 0xD000: bank_index = 0; break;
        case 0x6000: case 0x2000: case 0xA000: case 0xE000: bank_index = 1; break;
        case 0x7000: case 0x3000: case 0xB000: case 0xF000: bank_index = 2; break;
    }

    if (bank_index < 3u)
    {
        if (addr & 0x01u)
            regs[bank_index] = (regs[bank_index] & 0x00FFu) | ((uint16_t)data << 8);
        else
            regs[bank_index] = (regs[bank_index] & 0xFF00u) | data;
        regs[bank_index] &= 0x0FFFu;
    }
}

// -----------------------------------------------------------------------
// Generic banked ROM loop (8KB banks, 8-bit bank registers)
// -----------------------------------------------------------------------
static void __no_inline_not_in_flash_func(banked8_loop)(
    const uint8_t *rom_base,
    uint32_t available_length,
    uint8_t *bank_regs,
    void (*write_handler)(uint16_t, uint8_t, void *))
{
    bank8_ctx_t ctx = { .bank_regs = bank_regs };

    while (true)
    {
        pio_drain_writes(write_handler, &ctx);

        uint16_t addr = (uint16_t)pio_sm_get_blocking(msx_bus.pio, msx_bus.sm_read);

        pio_drain_writes(write_handler, &ctx);

        bool in_window = (addr >= 0x4000u) && (addr <= 0xBFFFu);
        uint8_t data = 0xFFu;

        if (in_window)
        {
            uint32_t rel = ((uint32_t)bank_regs[(addr - 0x4000u) >> 13] * 0x2000u) + (addr & 0x1FFFu);
            if (available_length == 0u || rel < available_length)
                data = read_rom_byte(rom_base, rel);
        }

        pio_sm_put_blocking(msx_bus.pio, msx_bus.sm_read, pio_build_token(in_window, data));
    }
}

// Forward declarations for functions called from the RAM-target launch dispatch
void __no_inline_not_in_flash_func(loadrom_planar64)(uint32_t offset, bool cache_enable);

void __no_inline_not_in_flash_func(loadrom_plain32)(uint32_t offset, bool cache_enable)
{
    const uint8_t *rom_base;
    uint32_t available_length;
    prepare_rom_source(offset, cache_enable, 32768u, &rom_base, &available_length);

    msx_pio_bus_init();

    while (true)
    {
        uint16_t addr = (uint16_t)pio_sm_get_blocking(msx_bus.pio, msx_bus.sm_read);

        bool in_window = (addr >= 0x4000u) && (addr <= 0xBFFFu);
        uint8_t data = in_window ? rom_base[addr - 0x4000u] : 0xFFu;

        pio_sm_put_blocking(msx_bus.pio, msx_bus.sm_read, pio_build_token(in_window, data));
    }
}

void __no_inline_not_in_flash_func(loadrom_linear48)(uint32_t offset, bool cache_enable)
{
    const uint8_t *rom_base;
    uint32_t available_length;
    prepare_rom_source(offset, cache_enable, 49152u, &rom_base, &available_length);

    msx_pio_bus_init();

    while (true)
    {
        uint16_t addr = (uint16_t)pio_sm_get_blocking(msx_bus.pio, msx_bus.sm_read);

        bool in_window = (addr <= 0xBFFFu);
        uint8_t data = in_window ? rom_base[addr] : 0xFFu;

        pio_sm_put_blocking(msx_bus.pio, msx_bus.sm_read, pio_build_token(in_window, data));
    }
}

void __no_inline_not_in_flash_func(loadrom_konamiscc)(uint32_t offset, bool cache_enable)
{
    uint8_t bank_registers[4] = {0, 1, 2, 3};
    const uint8_t *rom_base;
    uint32_t available_length;
    prepare_rom_source(offset, cache_enable, 0u, &rom_base, &available_length);

    msx_pio_bus_init();
    banked8_loop(rom_base, available_length, bank_registers, handle_konamiscc_write);
}

// -----------------------------------------------------------------------
// Core 1 audio entry: generates SCC samples and pushes to I2S
// -----------------------------------------------------------------------
static void __no_inline_not_in_flash_func(core1_scc_audio)(void)
{
    while (true)
    {
        struct audio_buffer *buffer = take_audio_buffer(audio_pool, true);
        int16_t *samples = (int16_t *)buffer->buffer->bytes;
        for (int i = 0; i < SCC_AUDIO_BUFFER_SAMPLES; i++)
        {
            int16_t raw = SCC_calc(&scc_instance);
            int32_t boosted = (int32_t)raw << SCC_VOLUME_SHIFT;
            if (boosted > 32767) boosted = 32767;
            else if (boosted < -32768) boosted = -32768;
            int16_t s = (int16_t)boosted;
            samples[i * 2]     = s;  // left
            samples[i * 2 + 1] = s;  // right
        }
        buffer->sample_count = SCC_AUDIO_BUFFER_SAMPLES;
        give_audio_buffer(audio_pool, buffer);
    }
}

void __not_in_flash_func(service_scc_audio)(void)
{
    if (!scc_audio_ready || !audio_pool)
        return;

    struct audio_buffer *buffer = take_audio_buffer(audio_pool, false);
    if (!buffer)
        return;

    int16_t *samples = (int16_t *)buffer->buffer->bytes;
    for (int i = 0; i < SCC_AUDIO_BUFFER_SAMPLES; i++)
    {
        int16_t raw = SCC_calc(&scc_instance);
        int32_t boosted = (int32_t)raw << SCC_VOLUME_SHIFT;
        if (boosted > 32767) boosted = 32767;
        else if (boosted < -32768) boosted = -32768;
        int16_t s = (int16_t)boosted;
        samples[i * 2]     = s;
        samples[i * 2 + 1] = s;
    }
    buffer->sample_count = SCC_AUDIO_BUFFER_SAMPLES;
    give_audio_buffer(audio_pool, buffer);
}

// -----------------------------------------------------------------------
// I2S audio initialisation. The mapper/C2 modes keep their I/O responder on
// PIO1, so audio must stay on PIO0 and avoid SM0/SM1 used by the MSX bus.
// -----------------------------------------------------------------------
static void i2s_audio_init(void)
{
    if (scc_audio_ready)
        return;

    // Unmute DAC (active-high mute: low = unmuted)
    gpio_init(I2S_MUTE_PIN);
    gpio_set_dir(I2S_MUTE_PIN, GPIO_OUT);
    gpio_put(I2S_MUTE_PIN, 0);

    static audio_format_t audio_format = {
        .sample_freq = SCC_SAMPLE_RATE,
        .format = AUDIO_BUFFER_FORMAT_PCM_S16,
        .channel_count = 2,
    };

    static struct audio_buffer_format producer_format = {
        .format = &audio_format,
        .sample_stride = 4,  // 2 channels * 2 bytes
    };

    audio_pool = audio_new_producer_pool(&producer_format, 3, SCC_AUDIO_BUFFER_SAMPLES);

    if (scc_dma_channel < 0)
    {
        for (int ch = 0; ch < NUM_DMA_CHANNELS; ++ch)
        {
            if (!dma_channel_is_claimed((uint)ch))
            {
                scc_dma_channel = ch;
                break;
            }
        }
    }
    if (scc_dma_channel < 0)
    {
        audio_pool = NULL;
        return;
    }

    static struct audio_i2s_config i2s_config = {
        .data_pin = I2S_DATA_PIN,
        .clock_pin_base = I2S_BCLK_PIN,
        .dma_channel = 0,
        .pio_sm = 2,
    };

    i2s_config.dma_channel = (uint)scc_dma_channel;

    audio_i2s_setup(&audio_format, &i2s_config);
    audio_i2s_connect(audio_pool);
    audio_i2s_set_enabled(true);
    scc_audio_ready = true;
}

// -----------------------------------------------------------------------
// Konami SCC mapper with SCC sound emulation via I2S
// -----------------------------------------------------------------------
void __no_inline_not_in_flash_func(loadrom_konamiscc_scc)(uint32_t offset, bool cache_enable, uint32_t scc_type)
{
    uint8_t bank_registers[4] = {0, 1, 2, 3};
    const uint8_t *rom_base;
    uint32_t available_length;
    prepare_rom_source(offset, cache_enable, 0u, &rom_base, &available_length);

    // Initialise SCC emulator (static allocation, no malloc)
    memset(&scc_instance, 0, sizeof(SCC));
    scc_instance.clk  = SCC_CLOCK;
    scc_instance.rate = SCC_SAMPLE_RATE;
    SCC_set_quality(&scc_instance, 1);
    scc_instance.type = scc_type;
    SCC_reset(&scc_instance);

    // Start I2S audio subsystem, then launch audio on core 1
    i2s_audio_init();
    multicore_launch_core1(core1_scc_audio);

    msx_pio_bus_init();

    while (true)
    {
        // --- drain pending writes ---
        uint16_t waddr;
        uint8_t  wdata;
        while (pio_try_get_write(&waddr, &wdata))
        {
            if      (waddr >= 0x5000u && waddr <= 0x57FFu) bank_registers[0] = wdata;
            else if (waddr >= 0x7000u && waddr <= 0x77FFu) bank_registers[1] = wdata;
            else if (waddr >= 0x9000u && waddr <= 0x97FFu) bank_registers[2] = wdata;
            else if (waddr >= 0xB000u && waddr <= 0xB7FFu) bank_registers[3] = wdata;

            // Forward to SCC emulator (handles enable + register writes)
            SCC_write(&scc_instance, waddr, wdata);
        }

        // --- handle read request ---
        uint16_t addr = (uint16_t)pio_sm_get_blocking(msx_bus.pio, msx_bus.sm_read);

        // drain writes that arrived while waiting
        while (pio_try_get_write(&waddr, &wdata))
        {
            if      (waddr >= 0x5000u && waddr <= 0x57FFu) bank_registers[0] = wdata;
            else if (waddr >= 0x7000u && waddr <= 0x77FFu) bank_registers[1] = wdata;
            else if (waddr >= 0x9000u && waddr <= 0x97FFu) bank_registers[2] = wdata;
            else if (waddr >= 0xB000u && waddr <= 0xB7FFu) bank_registers[3] = wdata;
            SCC_write(&scc_instance, waddr, wdata);
        }

        bool in_window = (addr >= 0x4000u) && (addr <= 0xBFFFu);
        uint8_t data = 0xFFu;

        if (in_window)
        {
            // Check if address falls in active SCC register read region.
            // Standard SCC: 0x9800-0x98FF (base_adr = 0x9000)
            // Enhanced SCC+: 0xB800-0xB8FF (base_adr = 0xB000) or 0x9800-0x98FF
            bool is_scc_read = false;
            if (scc_instance.active)
            {
                uint32_t scc_reg_start = scc_instance.base_adr + 0x800u;
                if (addr >= scc_reg_start && addr <= (scc_reg_start + 0xFFu))
                    is_scc_read = true;
            }
            // SCC+ mode register at 0xBFFE-0xBFFF
            if (scc_type == SCC_ENHANCED && (addr & 0xFFFEu) == 0xBFFEu)
                is_scc_read = true;

            if (is_scc_read)
            {
                data = (uint8_t)SCC_read(&scc_instance, addr);
            }
            else
            {
                uint32_t rel = ((uint32_t)bank_registers[(addr - 0x4000u) >> 13] * 0x2000u)
                             + (addr & 0x1FFFu);
                if (available_length == 0u || rel < available_length)
                    data = read_rom_byte(rom_base, rel);
            }
        }

        pio_sm_put_blocking(msx_bus.pio, msx_bus.sm_read, pio_build_token(in_window, data));
    }
}

void __no_inline_not_in_flash_func(loadrom_konami)(uint32_t offset, bool cache_enable)
{
    uint8_t bank_registers[4] = {0, 1, 2, 3};
    const uint8_t *rom_base;
    uint32_t available_length;
    prepare_rom_source(offset, cache_enable, 0u, &rom_base, &available_length);

    msx_pio_bus_init();
    banked8_loop(rom_base, available_length, bank_registers, handle_konami_write);
}

void __no_inline_not_in_flash_func(loadrom_ascii8)(uint32_t offset, bool cache_enable)
{
    uint8_t bank_registers[4] = {0, 1, 2, 3};
    const uint8_t *rom_base;
    uint32_t available_length;
    prepare_rom_source(offset, cache_enable, 0u, &rom_base, &available_length);

    msx_pio_bus_init();
    banked8_loop(rom_base, available_length, bank_registers, handle_ascii8_write);
}

void __no_inline_not_in_flash_func(loadrom_ascii16)(uint32_t offset, bool cache_enable)
{
    uint8_t bank_registers[2] = {0, 1};
    const uint8_t *rom_base;
    uint32_t available_length;
    prepare_rom_source(offset, cache_enable, 0u, &rom_base, &available_length);

    msx_pio_bus_init();

    bank8_ctx_t ctx = { .bank_regs = bank_registers };

    while (true)
    {
        pio_drain_writes(handle_ascii16_write, &ctx);

        uint16_t addr = (uint16_t)pio_sm_get_blocking(msx_bus.pio, msx_bus.sm_read);

        pio_drain_writes(handle_ascii16_write, &ctx);

        bool in_window = (addr >= 0x4000u) && (addr <= 0xBFFFu);
        uint8_t data = 0xFFu;

        if (in_window)
        {
            uint8_t bank = (addr >> 15) & 1;
            uint32_t rel = ((uint32_t)bank_registers[bank] << 14) + (addr & 0x3FFFu);
            if (available_length == 0u || rel < available_length)
                data = read_rom_byte(rom_base, rel);
        }

        pio_sm_put_blocking(msx_bus.pio, msx_bus.sm_read, pio_build_token(in_window, data));
    }
}

// -----------------------------------------------------------------------
// Sunrise IDE write handler (cReg mapper at 0x4104 + IDE registers)
// -----------------------------------------------------------------------
typedef struct {
    sunrise_ide_t *ide;
} sunrise_ctx_t;

static inline void __not_in_flash_func(handle_sunrise_write)(uint16_t addr, uint8_t data, void *ctx)
{
    sunrise_ctx_t *sctx = (sunrise_ctx_t *)ctx;

    // IDE register / control writes (0x4104, 0x7C00-0x7DFF, 0x7E00-0x7EFF)
    if (addr >= 0x4000u && addr <= 0x7FFFu)
    {
        sunrise_ide_handle_write(sctx->ide, addr, data);
    }
}

// -----------------------------------------------------------------------
// loadrom_sunrise - Sunrise IDE Nextor ROM with emulated IDE interface
// -----------------------------------------------------------------------
// Uses the Sunrise IDE mapper: a single 16KB ROM window at 0x4000-0x7FFF
// with page selection via the control register at 0x4104 (bits 7:5 = page).
// No ROM at 0x8000-0xBFFF — the MSX provides its own RAM there.
// IDE register overlay when bit 0 of the control register is set:
//   - 0x7C00-0x7DFF = 16-bit data register (low/high byte latch)
//   - 0x7E00-0x7EFF = ATA task-file registers (mirrored every 16 bytes)
//   - 0x7F00-0x7FFF = ROM data (excluded from IDE space)
// ATA commands are translated to USB MSC operations on Core 1.
void __no_inline_not_in_flash_func(loadrom_sunrise)(uint32_t offset, bool cache_enable)
{
    const uint8_t *rom_base;
    uint32_t available_length;
    prepare_rom_source(offset, cache_enable, 0u, &rom_base, &available_length);

    // Initialise Sunrise IDE state
    static sunrise_ide_t ide;
    sunrise_ide_init(&ide);

    // Share IDE context with Core 1 and launch USB host task
    sunrise_usb_set_ide_ctx(&ide);
    multicore_launch_core1(sunrise_usb_task);

    // Initialise PIO bus engine
    msx_pio_bus_init();

    sunrise_ctx_t ctx = { .ide = &ide };

    // Main loop: service PIO read/write events
    // Continuous write draining needed — Sunrise IDE generates heavy
    // write bursts (bank switch + IDE_ON + task-file registers + command)
    // that can overflow the 8-entry PIO FIFO.
    while (true)
    {
        uint16_t addr;

        // Poll: drain write FIFO while waiting for a read event
        while (true)
        {
            pio_drain_writes(handle_sunrise_write, &ctx);
            if (!pio_sm_is_rx_fifo_empty(msx_bus.pio, msx_bus.sm_read))
            {
                addr = (uint16_t)pio_sm_get(msx_bus.pio, msx_bus.sm_read);
                break;
            }
        }

        // Drain any writes that arrived alongside the read
        pio_drain_writes(handle_sunrise_write, &ctx);

        // Sunrise IDE ROM is only at 0x4000-0x7FFF (one 16KB window)
        bool in_window = (addr >= 0x4000u) && (addr <= 0x7FFFu);
        uint8_t data = 0xFFu;

        if (in_window)
        {
            // Check if IDE intercepts this read (0x7C00-0x7EFF when enabled)
            uint8_t ide_data;
            if (sunrise_ide_handle_read(&ide, addr, &ide_data))
            {
                data = ide_data;
            }
            else
            {
                // Sunrise mapper: page selected by ide.segment (cReg bits 7:5)
                uint8_t seg = ide.segment;
                uint32_t rel = ((uint32_t)seg << 14) + (addr & 0x3FFFu);
                if (available_length == 0u || rel < available_length)
                    data = read_rom_byte(rom_base, rel);
            }
        }

        pio_sm_put_blocking(msx_bus.pio, msx_bus.sm_read, pio_build_token(in_window, data));
    }
}

// -----------------------------------------------------------------------
// loadrom_sunrise_mapper - Sunrise IDE Nextor + 1MB Memory Mapper
// -----------------------------------------------------------------------
// Implements expanded slot with two sub-slots:
//   Sub-slot 0: Nextor ROM (Sunrise IDE) — 16KB window at 0x4000-0x7FFF
//   Sub-slot 1: 1MB Memory Mapper RAM — all 4 pages (0x0000-0xFFFF)
//
// The sub-slot register at 0xFFFF controls which sub-slot is selected
// for each 16KB page (bits 1:0 = page 0, bits 3:2 = page 1, etc.).
// Reading 0xFFFF returns the bitwise NOT of the sub-slot register.
//
// Memory mapper page registers (I/O ports FC-FF) select which 16KB page
// of mapper RAM appears in each address range:
//   Port FC → page at 0x0000-0x3FFF
//   Port FD → page at 0x4000-0x7FFF
//   Port FE → page at 0x8000-0xBFFF
//   Port FF → page at 0xC000-0xFFFF
//
// Reset values per BIOS convention: FC=3, FD=2, FE=1, FF=0
//
// The mapper RAM is 1MB = 64 pages of 16KB. Page registers are treated
// as 8-bit values and normalized to 0..63 when accessing RAM.
void __no_inline_not_in_flash_func(loadrom_sunrise_mapper)(uint32_t offset, bool cache_enable)
{
    (void)cache_enable;

    // ---------------------------------------------------------------
    // Phase 1 — Bootstrap: serve a tiny ROM that restarts the MSX.
    //
    // On cold power-on the Pico and MSX start simultaneously.  The MSX2
    // BIOS probes slots very early, and if the Pico is not yet ready
    // the BIOS records the slot as empty/simple.  Releasing WAIT later
    // with an expanded-slot mapper active leaves the BIOS in an
    // inconsistent state, causing a freeze (blue screen on MSX2).
    //
    // To guarantee a clean boot we first serve a minimal ROM whose INIT
    // routine executes JP 0x0000 (cold restart).  Once the restart is
    // detected we freeze the CPU and set up the full mapper before the
    // BIOS probes slots again.
    // ---------------------------------------------------------------

    // Minimal MSX ROM:  AB header with INIT that sets port F4 bit 7
    // (forces cold-boot on MSX2+, showing RAM count) then restarts.
    static const uint8_t bootstrap_rom[] = {
        0x41, 0x42,            // 'AB' ROM header
        0x0A, 0x40,            // INIT = 0x400A
        0x00, 0x00,            // STATEMENT = none
        0x00, 0x00,            // DEVICE = none
        0x00, 0x00,            // TEXT = none
        0xF3,                  // DI
        0xDB, 0xF4,            // IN A, (0xF4)
        0xF6, 0x80,            // OR 0x80       (set bit 7 → cold boot)
        0xD3, 0xF4,            // OUT (0xF4), A
        0xC7                   // RST 0x00      (cold restart)
    };

    // Start PIO memory bus so the MSX can discover the bootstrap ROM.
    msx_pio_bus_init();

    // Serve bootstrap ROM reads until the restart is detected.
    bool restart_detected = false;
    bool init_called = false;

    while (!restart_detected)
    {
        // Drain writes (ignored during bootstrap)
        {
            uint16_t waddr;
            uint8_t wdata;
            while (pio_try_get_write(&waddr, &wdata)) { }
        }

        if (!pio_sm_is_rx_fifo_empty(msx_bus.pio, msx_bus.sm_read))
        {
            uint16_t addr = (uint16_t)pio_sm_get(msx_bus.pio, msx_bus.sm_read);

            if (init_called && addr == 0x0000u)
            {
                pio_sm_put_blocking(msx_bus.pio, msx_bus.sm_read,
                                    pio_build_token(false, 0xFFu));
                restart_detected = true;
            }
            else
            {
                if (addr >= 0x400Au && addr <= 0x4011u)
                    init_called = true;

                bool in_window = (addr >= 0x4000u && addr <= 0x7FFFu);
                uint8_t data = 0xFFu;
                if (in_window)
                {
                    uint32_t rel = addr - 0x4000u;
                    if (rel < sizeof(bootstrap_rom))
                        data = bootstrap_rom[rel];
                }
                pio_sm_put_blocking(msx_bus.pio, msx_bus.sm_read,
                                    pio_build_token(in_window, data));
            }
        }
        else
        {
            // MSX1 path: detect restart on raw address bus
            if (init_called && !gpio_get(PIN_RD) &&
                ((gpio_get_all() & 0xFFFFu) == 0x0000u))
            {
                restart_detected = true;
            }
        }
    }

    // ---------------------------------------------------------------
    // Phase 2 — Initialise the expanded-slot mapper.
    // The MSX just restarted — freeze it before the BIOS probes slots.
    // ---------------------------------------------------------------
    pio_sm_set_enabled(pio0, 0, false);
    pio_sm_set_enabled(pio0, 1, false);
    gpio_init(PIN_WAIT);
    gpio_set_dir(PIN_WAIT, GPIO_OUT);
    gpio_put(PIN_WAIT, 0);            // Assert WAIT — freeze MSX bus

    const uint8_t *rom_base;
    uint32_t available_length;
    prepare_sunrise_mapper_rom_source(offset, cache_enable, &rom_base, &available_length);

    // Initialise Sunrise IDE state
    static sunrise_ide_t ide;
    sunrise_ide_init(&ide);

    // Share IDE context with Core 1 and launch USB host task
    sunrise_usb_set_ide_ctx(&ide);
    multicore_launch_core1(sunrise_usb_task);

    // Initialise mapper page registers (BIOS convention)
    uint8_t mapper_reg[4] = { 3, 2, 1, 0 };  // FC, FD, FE, FF

    // Sub-slot register: bits [1:0]=page0, [3:2]=page1, [5:4]=page2, [7:6]=page3
    // Boot mapping for Nextor MAP_INIT compatibility:
    //   page0 -> sub-slot0
    //   page1 -> sub-slot0 (Sunrise ROM/IDE)
    //   page2 -> sub-slot1 (mapper RAM, probe target at 0x8000)
    //   page3 -> sub-slot0
    // Value: 0b00010000 = 0x10
    uint8_t subslot_reg = 0x10;

    // Clear mapper RAM in external PSRAM
    mapper_fill_ff();

    // Initialise PIO I/O bus FIRST (mapper port handlers must be ready
    // before the memory bus releases WAIT and the BIOS starts probing).
    msx_pio_io_bus_init();

    // Initialise PIO memory bus — this hands PIN_WAIT back to the PIO
    // read SM whose first instruction uses "side 1" (WAIT released),
    // so the MSX resumes execution with everything fully initialised.
    msx_pio_bus_init();

    sunrise_ctx_t ctx = { .ide = &ide };

    // Main loop: service memory reads/writes and I/O reads/writes
    while (true)
    {
        // --- Drain memory writes (Sunrise IDE + mapper RAM + sub-slot) ---
        {
            uint16_t waddr;
            uint8_t wdata;
            while (pio_try_get_write(&waddr, &wdata))
            {
                // Sub-slot register write at 0xFFFF
                if (waddr == 0xFFFFu)
                {
                    subslot_reg = wdata;
                }
                else
                {
                    uint8_t page = (waddr >> 14) & 0x03u;
                    uint8_t active_subslot = (subslot_reg >> (page * 2)) & 0x03u;

                    if (active_subslot == 0)
                    {
                        // Sub-slot 0: Sunrise IDE (0x4000-0x7FFF only)
                        if (waddr >= 0x4000u && waddr <= 0x7FFFu)
                        {
                            sunrise_ide_handle_write(&ide, waddr, wdata);
                        }
                    }
                    else if (active_subslot == 1)
                    {
                        // Sub-slot 1: Memory mapper RAM — write to mapped page
                        uint8_t mapper_page = mapper_page_from_reg(mapper_reg[page]);
                        uint32_t mapper_offset = ((uint32_t)mapper_page << 14) | (waddr & 0x3FFFu);
                        mapper_write_byte(mapper_offset, wdata);
                    }
                    // Sub-slots 2 and 3: unused, writes are ignored
                }
            }
        }

        // --- Drain I/O writes (mapper page registers FC-FF) ---
        {
            uint16_t io_addr;
            uint8_t io_data;
            while (pio_try_get_io_write(&io_addr, &io_data))
            {
                uint8_t port = io_addr & 0xFFu;
                if (port >= 0xFCu && port <= 0xFFu)
                {
                    mapper_reg[port - 0xFCu] = io_data & 0x3Fu;
                }
            }
        }

        // --- Handle I/O reads (mapper page registers FC-FF) ---
        {
            uint16_t io_addr;
            while (pio_try_get_io_read(&io_addr))
            {
                uint8_t port = io_addr & 0xFFu;
                bool in_window = false;
                uint8_t data = 0xFFu;

                if (port >= 0xFCu && port <= 0xFFu)
                {
                    in_window = true;
                    data = (uint8_t)(0xC0u | (mapper_reg[port - 0xFCu] & 0x3Fu));
                }

                pio_sm_put_blocking(msx_io_bus.pio_read, msx_io_bus.sm_io_read, pio_build_token(in_window, data));
            }
        }

        // --- Handle memory reads ---
        if (!pio_sm_is_rx_fifo_empty(msx_bus.pio, msx_bus.sm_read))
        {
            uint16_t addr = (uint16_t)pio_sm_get(msx_bus.pio, msx_bus.sm_read);
            // Always drive the bus when our primary slot is selected (the
            // PIO only queues reads while SLTSL is active for our slot).
            // Real MSX tolerates a floating bus (pull-ups -> 0xFF), but
            // several FPGA cores require an explicit ack on every read,
            // including reads to addresses inside an empty/unmapped
            // sub-slot. Default to 0xFF and override below.
            uint8_t data = 0xFFu;
            bool in_window = true;

            // Sub-slot register read at 0xFFFF: return ~subslot_reg
            if (addr == 0xFFFFu)
            {
                data = ~subslot_reg;
            }
            else
            {
                uint8_t page = (addr >> 14) & 0x03u;
                uint8_t active_subslot = (subslot_reg >> (page * 2)) & 0x03u;

                if (active_subslot == 0)
                {
                    // Sub-slot 0: Nextor ROM (0x4000-0x7FFF only)
                    if (addr >= 0x4000u && addr <= 0x7FFFu)
                    {
                        // Check if IDE intercepts this read
                        uint8_t ide_data;
                        if (sunrise_ide_handle_read(&ide, addr, &ide_data))
                        {
                            data = ide_data;
                        }
                        else
                        {
                            // Sunrise mapper: page selected by ide.segment
                            uint8_t seg = ide.segment;
                            uint32_t rel = ((uint32_t)seg << 14) + (addr & 0x3FFFu);
                            if (available_length == 0u || rel < available_length)
                                data = read_rom_byte(rom_base, rel);
                        }
                    }
                }
                else if (active_subslot == 1)
                {
                    // Sub-slot 1: Memory mapper RAM — all 4 pages
                    uint8_t mapper_page = mapper_page_from_reg(mapper_reg[page]);
                    uint32_t mapper_offset = ((uint32_t)mapper_page << 14) | (addr & 0x3FFFu);
                    data = mapper_read_byte(mapper_offset);
                }
                // Sub-slots 2 and 3: unused — keep default 0xFF (in window)
            }

            pio_sm_put_blocking(msx_bus.pio, msx_bus.sm_read, pio_build_token(in_window, data));
        }
    }
}

// -----------------------------------------------------------------------
// Case 15: Sunrise IDE via microSD card (no mapper)
// -----------------------------------------------------------------------
// Identical to loadrom_sunrise (case 10) but launches the SD backend
// on Core 1 instead of the USB backend.
void __no_inline_not_in_flash_func(loadrom_sunrise_sd)(uint32_t offset, bool cache_enable)
{
    const uint8_t *rom_base;
    uint32_t available_length;
    prepare_rom_source(offset, cache_enable, 0u, &rom_base, &available_length);

    static sunrise_ide_t ide;
    sunrise_ide_init(&ide);

    sunrise_sd_set_ide_ctx(&ide);
    multicore_launch_core1(sunrise_sd_task);

    msx_pio_bus_init();

    sunrise_ctx_t ctx = { .ide = &ide };

    while (true)
    {
        uint16_t addr;
        while (true)
        {
            pio_drain_writes(handle_sunrise_write, &ctx);
            if (!pio_sm_is_rx_fifo_empty(msx_bus.pio, msx_bus.sm_read))
            {
                addr = (uint16_t)pio_sm_get(msx_bus.pio, msx_bus.sm_read);
                break;
            }
        }

        pio_drain_writes(handle_sunrise_write, &ctx);

        bool in_window = (addr >= 0x4000u) && (addr <= 0x7FFFu);
        uint8_t data = 0xFFu;

        if (in_window)
        {
            uint8_t ide_data;
            if (sunrise_ide_handle_read(&ide, addr, &ide_data))
            {
                data = ide_data;
            }
            else
            {
                uint8_t seg = ide.segment;
                uint32_t rel = ((uint32_t)seg << 14) + (addr & 0x3FFFu);
                if (available_length == 0u || rel < available_length)
                    data = read_rom_byte(rom_base, rel);
            }
        }

        pio_sm_put_blocking(msx_bus.pio, msx_bus.sm_read, pio_build_token(in_window, data));
    }
}

// -----------------------------------------------------------------------
// Case 16: Sunrise IDE + 1MB memory mapper via microSD card
// -----------------------------------------------------------------------
// Identical to loadrom_sunrise_mapper (case 11) but launches the SD
// backend on Core 1 instead of the USB backend.
void __no_inline_not_in_flash_func(loadrom_sunrise_mapper_sd)(uint32_t offset, bool cache_enable)
{
    (void)cache_enable;

    // Phase 1 — Bootstrap: minimal ROM that restarts the MSX
    static const uint8_t bootstrap_rom[] = {
        0x41, 0x42,            // 'AB' ROM header
        0x0A, 0x40,            // INIT = 0x400A
        0x00, 0x00,            // STATEMENT = none
        0x00, 0x00,            // DEVICE = none
        0x00, 0x00,            // TEXT = none
        0xF3,                  // DI
        0xDB, 0xF4,            // IN A, (0xF4)
        0xF6, 0x80,            // OR 0x80
        0xD3, 0xF4,            // OUT (0xF4), A
        0xC7                   // RST 0x00
    };

    msx_pio_bus_init();

    bool restart_detected = false;
    bool init_called = false;

    while (!restart_detected)
    {
        { uint16_t waddr; uint8_t wdata; while (pio_try_get_write(&waddr, &wdata)) { } }

        if (!pio_sm_is_rx_fifo_empty(msx_bus.pio, msx_bus.sm_read))
        {
            uint16_t addr = (uint16_t)pio_sm_get(msx_bus.pio, msx_bus.sm_read);
            if (init_called && addr == 0x0000u)
            {
                pio_sm_put_blocking(msx_bus.pio, msx_bus.sm_read, pio_build_token(false, 0xFFu));
                restart_detected = true;
            }
            else
            {
                if (addr >= 0x400Au && addr <= 0x4011u) init_called = true;
                bool in_window = (addr >= 0x4000u && addr <= 0x7FFFu);
                uint8_t data = 0xFFu;
                if (in_window)
                {
                    uint32_t rel = addr - 0x4000u;
                    if (rel < sizeof(bootstrap_rom)) data = bootstrap_rom[rel];
                }
                pio_sm_put_blocking(msx_bus.pio, msx_bus.sm_read, pio_build_token(in_window, data));
            }
        }
        else
        {
            if (init_called && !gpio_get(PIN_RD) && ((gpio_get_all() & 0xFFFFu) == 0x0000u))
                restart_detected = true;
        }
    }

    // Phase 2 — Initialise expanded-slot mapper
    pio_sm_set_enabled(pio0, 0, false);
    pio_sm_set_enabled(pio0, 1, false);
    gpio_init(PIN_WAIT);
    gpio_set_dir(PIN_WAIT, GPIO_OUT);
    gpio_put(PIN_WAIT, 0);

    const uint8_t *rom_base;
    uint32_t available_length;
    prepare_sunrise_mapper_rom_source(offset, cache_enable, &rom_base, &available_length);
    const uint8_t *wifi_rom_base = rom + offset + available_length;

    static sunrise_ide_t ide;
    sunrise_ide_init(&ide);

    sunrise_sd_set_ide_ctx(&ide);
    multicore_launch_core1(sunrise_sd_task);

    // Allocate 1MB mapper RAM from the PSRAM memory manager
    psram_mem_init();
    if (!psram_alloc(MAPPER_SIZE, &mapper_region))
    {
        while (true) { tight_loop_contents(); }
    }

    uint8_t mapper_reg[4] = { 3, 2, 1, 0 };
    uint8_t subslot_reg = 0x10;

    mapper_fill_ff();

    msx_pio_io_bus_init();
    msx_pio_bus_init();

    sunrise_ctx_t ctx = { .ide = &ide };

    while (true)
    {
        // Drain memory writes
        {
            uint16_t waddr; uint8_t wdata;
            while (pio_try_get_write(&waddr, &wdata))
            {
                if (waddr == 0xFFFFu)
                    subslot_reg = wdata;
                else
                {
                    uint8_t page = (waddr >> 14) & 0x03u;
                    uint8_t active_subslot = (subslot_reg >> (page * 2)) & 0x03u;
                    if (active_subslot == 0)
                    {
                        if (waddr >= 0x4000u && waddr <= 0x7FFFu)
                            sunrise_ide_handle_write(&ide, waddr, wdata);
                    }
                    else if (active_subslot == 1)
                    {
                        uint8_t mapper_page = mapper_page_from_reg(mapper_reg[page]);
                        uint32_t mapper_offset = ((uint32_t)mapper_page << 14) | (waddr & 0x3FFFu);
                        mapper_write_byte(mapper_offset, wdata);
                    }
                }
            }
        }

        // Drain I/O writes (mapper page registers FC-FF)
        {
            uint16_t io_addr; uint8_t io_data;
            while (pio_try_get_io_write(&io_addr, &io_data))
            {
                uint8_t port = io_addr & 0xFFu;
                if (port >= 0xFCu && port <= 0xFFu)
                    mapper_reg[port - 0xFCu] = io_data & 0x3Fu;
            }
        }

        // Handle I/O reads (mapper page registers FC-FF)
        {
            uint16_t io_addr;
            while (pio_try_get_io_read(&io_addr))
            {
                uint8_t port = io_addr & 0xFFu;
                bool in_window = false;
                uint8_t data = 0xFFu;
                if (port >= 0xFCu && port <= 0xFFu)
                {
                    in_window = true;
                    data = (uint8_t)(0xC0u | (mapper_reg[port - 0xFCu] & 0x3Fu));
                }
                pio_sm_put_blocking(msx_io_bus.pio_read, msx_io_bus.sm_io_read, pio_build_token(in_window, data));
            }
        }

        // Handle memory reads
        if (!pio_sm_is_rx_fifo_empty(msx_bus.pio, msx_bus.sm_read))
        {
            uint16_t addr = (uint16_t)pio_sm_get(msx_bus.pio, msx_bus.sm_read);
            uint8_t data = 0xFFu;
            bool in_window = false;

            if (addr == 0xFFFFu)
            {
                in_window = true;
                data = ~subslot_reg;
            }
            else
            {
                uint8_t page = (addr >> 14) & 0x03u;
                uint8_t active_subslot = (subslot_reg >> (page * 2)) & 0x03u;
                if (active_subslot == 0)
                {
                    if (addr >= 0x4000u && addr <= 0x7FFFu)
                    {
                        in_window = true;
                        uint8_t ide_data;
                        if (sunrise_ide_handle_read(&ide, addr, &ide_data))
                            data = ide_data;
                        else
                        {
                            uint8_t seg = ide.segment;
                            uint32_t rel = ((uint32_t)seg << 14) + (addr & 0x3FFFu);
                            if (available_length == 0u || rel < available_length)
                                data = read_rom_byte(rom_base, rel);
                        }
                    }
                }
                else if (active_subslot == 1)
                {
                    in_window = true;
                    uint8_t mapper_page = mapper_page_from_reg(mapper_reg[page]);
                    uint32_t mapper_offset = ((uint32_t)mapper_page << 14) | (addr & 0x3FFFu);
                    data = mapper_read_byte(mapper_offset);
                }
                // Sub-slots 2 and 3: unused, return 0xFF (not in window)
            }

            pio_sm_put_blocking(msx_bus.pio, msx_bus.sm_read, pio_build_token(in_window, data));
        }
    }
}

void __no_inline_not_in_flash_func(loadrom_neo8)(uint32_t offset)
{
    uint16_t bank_registers[6] = {0};
    const uint8_t *rom_base;
    uint32_t available_length;
    prepare_rom_source(offset, false, 0u, &rom_base, &available_length);

    msx_pio_bus_init();

    bank16_ctx_t ctx = { .bank_regs = bank_registers };

    while (true)
    {
        pio_drain_writes(handle_neo8_write, &ctx);

        uint16_t addr = (uint16_t)pio_sm_get_blocking(msx_bus.pio, msx_bus.sm_read);

        pio_drain_writes(handle_neo8_write, &ctx);

        bool in_window = (addr <= 0xBFFFu);
        uint8_t data = 0xFFu;

        if (in_window)
        {
            uint8_t bank_index = addr >> 13;
            if (bank_index < 6u)
            {
                uint32_t segment = bank_registers[bank_index] & 0x0FFFu;
                uint32_t rel = (segment << 13) + (addr & 0x1FFFu);
                if (available_length == 0u || rel < available_length)
                    data = read_rom_byte(rom_base, rel);
            }
        }

        pio_sm_put_blocking(msx_bus.pio, msx_bus.sm_read, pio_build_token(in_window, data));
    }
}

void __no_inline_not_in_flash_func(loadrom_neo16)(uint32_t offset)
{
    uint16_t bank_registers[3] = {0};
    const uint8_t *rom_base;
    uint32_t available_length;
    prepare_rom_source(offset, false, 0u, &rom_base, &available_length);

    msx_pio_bus_init();

    bank16_ctx_t ctx = { .bank_regs = bank_registers };

    while (true)
    {
        pio_drain_writes(handle_neo16_write, &ctx);

        uint16_t addr = (uint16_t)pio_sm_get_blocking(msx_bus.pio, msx_bus.sm_read);

        pio_drain_writes(handle_neo16_write, &ctx);

        bool in_window = (addr <= 0xBFFFu);
        uint8_t data = 0xFFu;

        if (in_window)
        {
            uint8_t bank_index = addr >> 14;
            if (bank_index < 3u)
            {
                uint32_t segment = bank_registers[bank_index] & 0x0FFFu;
                uint32_t rel = (segment << 14) + (addr & 0x3FFFu);
                if (available_length == 0u || rel < available_length)
                    data = read_rom_byte(rom_base, rel);
            }
        }

        pio_sm_put_blocking(msx_bus.pio, msx_bus.sm_read, pio_build_token(in_window, data));
    }
}

// -----------------------------------------------------------------------
// loadrom_planar64 - 64KB Planar ROM (no mapper)
// -----------------------------------------------------------------------
// Four 16KB pages covering the full 64KB address space.
void __no_inline_not_in_flash_func(loadrom_planar64)(uint32_t offset, bool cache_enable)
{
    const uint8_t *rom_base;
    uint32_t available_length;
    prepare_rom_source(offset, cache_enable, 65536u, &rom_base, &available_length);

    msx_pio_bus_init();

    while (true)
    {
        uint16_t addr = (uint16_t)pio_sm_get_blocking(msx_bus.pio, msx_bus.sm_read);

        bool in_window = true;
        uint8_t data = 0xFFu;

        if (available_length == 0u || (uint32_t)addr < available_length)
            data = read_rom_byte(rom_base, (uint32_t)addr);

        pio_sm_put_blocking(msx_bus.pio, msx_bus.sm_read, pio_build_token(in_window, data));
    }
}

// -----------------------------------------------------------------------
// Bank cache infrastructure for mapper-aware LRU caching
// -----------------------------------------------------------------------
// Provides a slot-based SRAM cache where each slot holds one bank of ROM
// data.  Used by mappers with large address spaces (ASCII16-X, NEO8/16
// cached variants) to serve all reads from SRAM.  Flash is only accessed
// on cache misses during bank switches.

#define BANK_CACHE_MAX_SLOTS 32   // max slots (256KB / 8KB)
#define BANK_CACHE_MAX_PINS   6   // max simultaneously pinned pages
#define BANK_EMPTY           0xFFFFu

typedef struct {
    uint16_t      slot_bank[BANK_CACHE_MAX_SLOTS]; // bank loaded per slot
    uint8_t       slot_lru[BANK_CACHE_MAX_SLOTS];  // LRU counter (0 = MRU)
    int8_t        page_slot[BANK_CACHE_MAX_PINS];  // slot pinned per page
    const uint8_t *flash_base;
    uint32_t      rom_length;
    uint8_t       num_slots;    // actual slot count
    uint8_t       num_pins;     // active pinned pages
    uint16_t      slot_size;    // bytes per slot (8192 or 16384)
    uint8_t       slot_shift;   // log2(slot_size): 13 or 14
} bank_cache_t;

static inline void __not_in_flash_func(bcache_init)(
    bank_cache_t *c, uint16_t slot_size, uint8_t num_pins,
    const uint8_t *flash_base, uint32_t rom_length)
{
    uint8_t num_slots = (uint8_t)(CACHE_SIZE / slot_size);
    c->num_slots  = num_slots;
    c->num_pins   = num_pins;
    c->slot_size  = slot_size;
    c->slot_shift = (slot_size == 8192u) ? 13 : 14;
    c->flash_base = flash_base;
    c->rom_length = rom_length;
    for (int i = 0; i < BANK_CACHE_MAX_SLOTS; i++)
    {
        c->slot_bank[i] = BANK_EMPTY;
        c->slot_lru[i]  = (uint8_t)i;
    }
    for (int i = 0; i < BANK_CACHE_MAX_PINS; i++)
        c->page_slot[i] = -1;
}

// Promote a slot to MRU.
static inline void __not_in_flash_func(bcache_touch)(bank_cache_t *c, int8_t slot)
{
    uint8_t prev = c->slot_lru[slot];
    if (prev == 0) return;
    uint8_t n = c->num_slots;
    for (uint8_t i = 0; i < n; i++)
        if (c->slot_lru[i] < prev) c->slot_lru[i]++;
    c->slot_lru[slot] = 0;
}

// Find the slot holding a given bank, or -1.
static inline int8_t __not_in_flash_func(bcache_find)(bank_cache_t *c, uint16_t bank)
{
    uint8_t n = c->num_slots;
    for (uint8_t i = 0; i < n; i++)
        if (c->slot_bank[i] == bank) return (int8_t)i;
    return -1;
}

// Pick a victim slot (highest LRU counter, not pinned).
static inline int8_t __not_in_flash_func(bcache_evict)(bank_cache_t *c)
{
    int8_t best = -1;
    uint8_t best_lru = 0;
    uint8_t n = c->num_slots;
    uint8_t np = c->num_pins;
    for (uint8_t i = 0; i < n; i++)
    {
        bool pinned = false;
        for (uint8_t p = 0; p < np; p++)
            if ((int8_t)i == c->page_slot[p]) { pinned = true; break; }
        if (pinned) continue;
        if (best < 0 || c->slot_lru[i] >= best_lru)
        {
            best = (int8_t)i;
            best_lru = c->slot_lru[i];
        }
    }
    return best;
}

// Ensure a bank is resident; returns its slot index.
static inline int8_t __not_in_flash_func(bcache_ensure)(bank_cache_t *c, uint16_t bank)
{
    // Normalize bank number modulo ROM size so out-of-range banks wrap
    // around, matching real hardware mirror behaviour.
    if (c->rom_length > 0u)
    {
        uint16_t total_banks = (uint16_t)(c->rom_length >> c->slot_shift);
        if (total_banks > 0u)
            bank = bank % total_banks;
    }

    int8_t slot = bcache_find(c, bank);
    if (slot >= 0) { bcache_touch(c, slot); return slot; }

    slot = bcache_evict(c);
    uint32_t src_off = (uint32_t)(bank & 0x0FFFu) << c->slot_shift;
    uint8_t *dst = &rom_sram[(uint32_t)slot * c->slot_size];
    uint16_t ss = c->slot_size;

    if (c->rom_length == 0u || src_off < c->rom_length)
    {
        uint32_t n = ss;
        if (c->rom_length > 0u && src_off + n > c->rom_length)
            n = c->rom_length - src_off;
        memcpy(dst, c->flash_base + src_off, n);
        if (n < ss) memset(dst + n, 0xFFu, ss - n);
    }
    else
    {
        memset(dst, 0xFFu, ss);
    }

    c->slot_bank[slot] = bank;
    bcache_touch(c, slot);
    return slot;
}

// Pre-fill the cache with the first N banks of the ROM.
static inline void __not_in_flash_func(bcache_prefill)(bank_cache_t *c)
{
    uint16_t max_banks = c->num_slots;
    if (c->rom_length > 0u)
    {
        uint16_t rom_banks = (uint16_t)((c->rom_length + c->slot_size - 1u) / c->slot_size);
        if (rom_banks < max_banks) max_banks = rom_banks;
    }
    for (uint16_t b = 0; b < max_banks; b++)
        bcache_ensure(c, b);
}

// -----------------------------------------------------------------------
// AMD-compatible flash command emulation for ASCII16-X
// -----------------------------------------------------------------------
// Real ASCII16-X cartridges use AMD/SST-compatible flash chips.  Some
// ROMs detect the cartridge by issuing a flash byte-program command and
// verifying the write.  Others use flash for persistent save data.
//
// The state machine below intercepts the standard AMD unlock + command
// sequences and emulates byte-program and sector-erase by modifying the
// SRAM bank cache directly.

typedef enum {
    FLASH_IDLE = 0,       // Normal read mode
    FLASH_UNLOCK1,        // Received AAh at *AAAh
    FLASH_UNLOCK2,        // Received 55h at *555h
    FLASH_BYTE_PGM,       // Received A0h at *AAAh – next write programs
    FLASH_ERASE_SETUP,    // Received 80h at *AAAh – awaiting second unlock
    FLASH_ERASE_UNLOCK1,  // Received AAh at *AAAh (second unlock cycle)
    FLASH_ERASE_UNLOCK2,  // Received 55h at *555h (second unlock cycle)
} flash_cmd_state_t;

typedef struct {
    uint16_t         bank_regs[2];
    bank_cache_t     cache;
    flash_cmd_state_t flash_state;
} ascii16x_state_t;

// Process a bus write through the AMD flash command state machine.
static inline void __not_in_flash_func(flash_process_write)(
    ascii16x_state_t *st, uint16_t addr, uint8_t data)
{
    uint16_t cmd_addr = addr & 0x0FFFu;

    switch (st->flash_state)
    {
        case FLASH_IDLE:
            if (cmd_addr == 0x0AAAu && data == 0xAAu)
                st->flash_state = FLASH_UNLOCK1;
            else if (data == 0xF0u)
                st->flash_state = FLASH_IDLE;  // Reset to read mode
            break;

        case FLASH_UNLOCK1:
            if (cmd_addr == 0x0555u && data == 0x55u)
                st->flash_state = FLASH_UNLOCK2;
            else
                st->flash_state = FLASH_IDLE;
            break;

        case FLASH_UNLOCK2:
            if (cmd_addr == 0x0AAAu)
            {
                switch (data)
                {
                    case 0xA0u: st->flash_state = FLASH_BYTE_PGM;    break;
                    case 0x80u: st->flash_state = FLASH_ERASE_SETUP;  break;
                    default:    st->flash_state = FLASH_IDLE;         break;
                }
            }
            else
                st->flash_state = FLASH_IDLE;
            break;

        case FLASH_BYTE_PGM:
        {
            // Program one byte: flash can only clear bits (AND-mask).
            uint8_t page_idx = ((addr >> 14) & 0x01u) ? 0u : 1u;
            int8_t slot = st->cache.page_slot[page_idx];
            if (slot >= 0)
            {
                uint32_t off = (uint32_t)slot * st->cache.slot_size
                             + (addr & 0x3FFFu);
                rom_sram[off] &= data;
            }
            st->flash_state = FLASH_IDLE;
            break;
        }

        case FLASH_ERASE_SETUP:
            if (cmd_addr == 0x0AAAu && data == 0xAAu)
                st->flash_state = FLASH_ERASE_UNLOCK1;
            else
                st->flash_state = FLASH_IDLE;
            break;

        case FLASH_ERASE_UNLOCK1:
            if (cmd_addr == 0x0555u && data == 0x55u)
                st->flash_state = FLASH_ERASE_UNLOCK2;
            else
                st->flash_state = FLASH_IDLE;
            break;

        case FLASH_ERASE_UNLOCK2:
            if (data == 0x30u)
            {
                // Sector erase: fill the mapped cache slot with FFh.
                uint8_t page_idx = ((addr >> 14) & 0x01u) ? 0u : 1u;
                int8_t slot = st->cache.page_slot[page_idx];
                if (slot >= 0)
                    memset(&rom_sram[(uint32_t)slot * st->cache.slot_size],
                           0xFFu, st->cache.slot_size);
            }
            st->flash_state = FLASH_IDLE;
            break;
    }
}

// Cached ASCII16-X write handler.
static inline void __not_in_flash_func(handle_ascii16x_write_cached)(uint16_t addr, uint8_t data, void *ctx)
{
    ascii16x_state_t *st = (ascii16x_state_t *)ctx;

    // Feed every write to the flash command state machine.
    flash_process_write(st, addr, data);

    // Bank register processing.
    uint8_t high_nibble = (uint8_t)((addr >> 8) & 0x0Fu);
    uint16_t bank = ((uint16_t)high_nibble << 8) | data;
    uint8_t page;

    switch (addr & 0xF000u)
    {
        case 0x2000u: case 0x6000u: case 0xA000u: case 0xE000u: page = 0; break;
        case 0x3000u: case 0x7000u: case 0xB000u: case 0xF000u: page = 1; break;
        default: return;
    }

    st->bank_regs[page] = bank;
    st->cache.page_slot[page] = bcache_ensure(&st->cache, bank);
}

// -----------------------------------------------------------------------
// loadrom_ascii16x - ASCII16-X mapper
// -----------------------------------------------------------------------
// Two 16KB banks mirrored to all four 16KB address quadrants:
//   page 1 bank at 4000-7FFF and C000-FFFF
//   page 2 bank at 0000-3FFF and 8000-BFFF
//
// Bank register mirrors:
//   page 1: 2000-2FFF, 6000-6FFF, A000-AFFF, E000-EFFF
//   page 2: 3000-3FFF, 7000-7FFF, B000-BFFF, F000-FFFF
//
// Bank number is 12-bit:
//   bits 0-7 from data bus (D0-D7)
//   bits 8-11 from address lines A8-A11
//
// Uses a mapper-aware LRU cache so every read is served from SRAM.
// Flash is only accessed during bank-switch cache misses.
void __no_inline_not_in_flash_func(loadrom_ascii16x)(uint32_t offset, bool cache_enable)
{
    (void)cache_enable;

    ascii16x_state_t state;
    memset(&state, 0, sizeof(state));

    bcache_init(&state.cache, 16384u, 2, rom + offset, active_rom_size);
    bcache_prefill(&state.cache);

    // Both pages start at bank 0 after reset
    state.cache.page_slot[0] = bcache_find(&state.cache, 0);
    state.cache.page_slot[1] = state.cache.page_slot[0];

    msx_pio_bus_init();

    while (true)
    {
        pio_drain_writes(handle_ascii16x_write_cached, &state);

        uint16_t addr = (uint16_t)pio_sm_get_blocking(msx_bus.pio, msx_bus.sm_read);

        pio_drain_writes(handle_ascii16x_write_cached, &state);

        // ASCII16-X mirrors ROM across all 4 quadrants.
        // Bit 14 selects the page: 1 = page 1 (regs[0]), 0 = page 2 (regs[1]).
        uint8_t data = 0xFFu;
        uint8_t page_idx = ((addr >> 14) & 0x01u) ? 0u : 1u;
        int8_t slot = state.cache.page_slot[page_idx];

        if (slot >= 0)
            data = rom_sram[(uint32_t)slot * state.cache.slot_size + (addr & 0x3FFFu)];

        pio_sm_put_blocking(msx_bus.pio, msx_bus.sm_read, pio_build_token(true, data));
    }
}

// -----------------------------------------------------------------------
// Manbow2 mapper — Konami SCC banking + AMD AM29F040B flash emulation
// -----------------------------------------------------------------------
// The Manbow2 cartridge uses standard Konami SCC bank switching (4×8KB
// windows at 0x4000-0xBFFF) backed by an AMD AM29F040B 512KB flash chip.
// The last 64KB sector (0x70000-0x7FFFF) is writable and used for save
// data.  All writes in the 0x4000-0xBFFF window pass through both the
// bank-switch decoder and the flash command state machine.
//
// Flash protocol (simplified — only the commands the game actually uses):
//   Program byte:  AA→[x555] 55→[x2AA] A0→[x555] data→[target]
//   Sector erase:  AA→[x555] 55→[x2AA] 80→[x555] AA→[x555] 55→[x2AA] 30→[sector]
//   Auto-select:   AA→[x555] 55→[x2AA] 90→[x555]
//   Reset:         F0→[any]
//
// Save data is backed by SRAM (volatile — lost on power off).  The last
// 64KB of the SRAM pool is reserved for the writable sector.

// Flash state machine states
enum manbow2_flash_state {
    MBW2_READ = 0,    // Normal read mode
    MBW2_CMD1,        // Received AA at x555, waiting for 55 at x2AA
    MBW2_CMD2,        // Received 55 at x2AA, waiting for command byte at x555
    MBW2_AUTOSELECT,  // Auto-select / ID mode
    MBW2_PROGRAM,     // Waiting for single data byte to program
    MBW2_ERASE_CMD1,  // Received 80, waiting for AA at x555
    MBW2_ERASE_CMD2,  // Received AA, waiting for 55 at x2AA
    MBW2_ERASE_CMD3   // Received 55, waiting for 30 + sector address
};

// Context for the Manbow2 mapper write handler and main loop
typedef struct {
    uint8_t bank_regs[4];         // Bank registers (Konami SCC style)
    enum manbow2_flash_state state;
    uint8_t *writable_sram;       // Pointer to 64KB SRAM backing the writable sector
    uint32_t writable_offset;     // First flash byte offset of writable sector (0x70000)
    uint32_t writable_size;       // Size of writable sector (0x10000 = 64KB)
    uint32_t rom_size_mask;       // ROM size - 1 (for bank wrapping)
} manbow2_ctx_t;

// Manbow2 write handler — processes both bank switching and flash commands.
// Every write in 0x4000-0xBFFF is routed here.
static inline void __not_in_flash_func(handle_manbow2_write)(uint16_t addr, uint8_t data, void *ctx)
{
    manbow2_ctx_t *mb = (manbow2_ctx_t *)ctx;

    if (addr < 0x4000u || addr > 0xBFFFu)
        return;

    uint8_t page = (uint8_t)((addr - 0x4000u) >> 13);

    // --- Flash command state machine ---
    // Compute the absolute flash address BEFORE updating the bank register.
    // This matches openMSX: flash.write(addr, value) uses the OLD bank,
    // then setRom(page, value) updates it afterward.
    uint32_t flash_addr = (uint32_t)mb->bank_regs[page] * 0x2000u + (addr & 0x1FFFu);

    // --- Bank switching (Konami SCC style) ---
    // Writes where (addr & 0x1800) == 0x1000 within each 8KB page select banks.
    // Updated AFTER flash_addr is computed (matches real hardware ordering).
    if ((addr & 0x1800u) == 0x1000u)
    {
        mb->bank_regs[page] = data & 0x3Fu;  // mask to 64 blocks (512KB / 8KB)
    }

    // Reset command (F0) from any state
    if (data == 0xF0u)
    {
        mb->state = MBW2_READ;
        return;
    }

    switch (mb->state)
    {
        case MBW2_READ:
            if ((flash_addr & 0x7FFu) == 0x555u && data == 0xAAu)
                mb->state = MBW2_CMD1;
            break;

        case MBW2_CMD1:
            if ((flash_addr & 0x7FFu) == 0x2AAu && data == 0x55u)
                mb->state = MBW2_CMD2;
            else
                mb->state = MBW2_READ;
            break;

        case MBW2_CMD2:
            if (data == 0xA0u)
                mb->state = MBW2_PROGRAM;
            else if (data == 0x90u)
                mb->state = MBW2_AUTOSELECT;
            else if (data == 0x80u)
                mb->state = MBW2_ERASE_CMD1;
            else
                mb->state = MBW2_READ;
            break;

        case MBW2_PROGRAM:
        {
            // Program a single byte: flash can only clear bits (AND with existing data).
            // Only the writable sector accepts programming.
            if (flash_addr >= mb->writable_offset &&
                flash_addr < mb->writable_offset + mb->writable_size)
            {
                uint32_t sram_off = flash_addr - mb->writable_offset;
                mb->writable_sram[sram_off] &= data;  // Flash program = AND
            }
            mb->state = MBW2_READ;
            break;
        }

        case MBW2_ERASE_CMD1:
            if ((flash_addr & 0x7FFu) == 0x555u && data == 0xAAu)
                mb->state = MBW2_ERASE_CMD2;
            else
                mb->state = MBW2_READ;
            break;

        case MBW2_ERASE_CMD2:
            if ((flash_addr & 0x7FFu) == 0x2AAu && data == 0x55u)
                mb->state = MBW2_ERASE_CMD3;
            else
                mb->state = MBW2_READ;
            break;

        case MBW2_ERASE_CMD3:
            if (data == 0x30u)
            {
                // Erase the sector containing flash_addr, if writable.
                if (flash_addr >= mb->writable_offset &&
                    flash_addr < mb->writable_offset + mb->writable_size)
                {
                    memset(mb->writable_sram, 0xFF, mb->writable_size);
                }
            }
            mb->state = MBW2_READ;
            break;

        case MBW2_AUTOSELECT:
            // Only F0 (handled above) exits auto-select mode.
            // Any other write is ignored while in this state.
            break;
    }
}

// -----------------------------------------------------------------------
// loadrom_manbow2 - Manbow2 (Konami SCC + AMD flash) mapper
// -----------------------------------------------------------------------
// 8KB banks: 4000-5FFF, 6000-7FFF, 8000-9FFF, A000-BFFF
// Same bank select addresses as Konami SCC.
// Flash sector 7 (last 64KB of 512KB ROM) is writable via SRAM.
void __no_inline_not_in_flash_func(loadrom_manbow2)(uint32_t offset, bool cache_enable)
{
    const uint8_t *rom_base;
    uint32_t available_length;

    // Reserve the last 64KB of the SRAM pool for the writable flash sector.
    // This leaves the rest for the ROM cache.
    static const uint32_t WRITABLE_SECTOR_SIZE  = 0x10000u;  // 64KB
    static const uint32_t WRITABLE_SECTOR_OFFSET = 0x70000u; // Last sector of 512KB
    uint32_t reduced_cache = CACHE_SIZE - WRITABLE_SECTOR_SIZE;

    // Temporarily reduce cache capacity so prepare_rom_source only uses
    // the first portion of SRAM, leaving 64KB for the writable sector.
    rom_cache_capacity = reduced_cache;
    prepare_rom_source(offset, cache_enable, 0u, &rom_base, &available_length);

    // Set up the writable SRAM area (last 64KB of rom_sram)
    uint8_t *writable_sram = &rom_sram[reduced_cache];

    // Initialise writable sector with ROM content (the original save data area).
    // If the ROM is large enough to contain sector 7, copy it; otherwise fill 0xFF.
    if (available_length >= WRITABLE_SECTOR_OFFSET + WRITABLE_SECTOR_SIZE)
    {
        // rom_base may point to flash XIP (ROM > cache).  For the writable
        // sector we must always read from flash, not the SRAM cache, because
        // the cache only covers the first portion of the ROM.
        const uint8_t *flash_rom = rom + offset;
        memcpy(writable_sram, flash_rom + WRITABLE_SECTOR_OFFSET, WRITABLE_SECTOR_SIZE);
    }
    else if (available_length > WRITABLE_SECTOR_OFFSET)
    {
        const uint8_t *flash_rom = rom + offset;
        uint32_t partial = available_length - WRITABLE_SECTOR_OFFSET;
        memcpy(writable_sram, flash_rom + WRITABLE_SECTOR_OFFSET, partial);
        memset(writable_sram + partial, 0xFF, WRITABLE_SECTOR_SIZE - partial);
    }
    else
    {
        memset(writable_sram, 0xFF, WRITABLE_SECTOR_SIZE);
    }

    // Initialize Manbow2 context
    manbow2_ctx_t mb = {
        .bank_regs = {0, 1, 2, 3},
        .state = MBW2_READ,
        .writable_sram = writable_sram,
        .writable_offset = WRITABLE_SECTOR_OFFSET,
        .writable_size = WRITABLE_SECTOR_SIZE,
        .rom_size_mask = 0
    };

    msx_pio_bus_init();

    // Main loop: service PIO read/write events.
    // Unlike the generic banked8_loop, this loop continuously drains the
    // write FIFO even while waiting for reads.  Manbow2 generates heavy
    // write traffic (flash data written through 0x5000-0x57FF etc.) that
    // can overflow the 8-entry PIO FIFO if writes are only drained around
    // read events.  Lost bank-switch writes cause the Z80 to read from
    // the wrong bank, crashing the game.  Same pattern as loadrom_sunrise.
    while (true)
    {
        uint16_t addr;

        // Poll: drain write FIFO continuously while waiting for a read
        while (true)
        {
            uint16_t waddr;
            uint8_t wdata;
            while (pio_try_get_write(&waddr, &wdata))
            {
                handle_manbow2_write(waddr, wdata, &mb);
            }
            if (!pio_sm_is_rx_fifo_empty(msx_bus.pio, msx_bus.sm_read))
            {
                addr = (uint16_t)pio_sm_get(msx_bus.pio, msx_bus.sm_read);
                break;
            }
        }

        // Drain any writes that arrived alongside the read
        {
            uint16_t waddr;
            uint8_t wdata;
            while (pio_try_get_write(&waddr, &wdata))
            {
                handle_manbow2_write(waddr, wdata, &mb);
            }
        }

        bool in_window = (addr >= 0x4000u) && (addr <= 0xBFFFu);
        uint8_t data = 0xFFu;

        if (in_window)
        {
            uint8_t page = (uint8_t)((addr - 0x4000u) >> 13);
            uint32_t rel = (uint32_t)mb.bank_regs[page] * 0x2000u + (addr & 0x1FFFu);

            if (mb.state == MBW2_AUTOSELECT)
            {
                // AMD auto-select: manufacturer ID at offset 0, device ID at offset 1
                // Sector protection at offset 2, extra code at offset 3
                uint32_t id_addr = rel & 0x03u;
                if (id_addr == 0x00u)
                    data = 0x01u;  // AMD manufacturer ID
                else if (id_addr == 0x01u)
                    data = 0xA4u;  // AM29F040B device ID
                else if (id_addr == 0x02u)
                {
                    // Sector write-protect status: 0 = writable, 1 = protected
                    // Only sector 7 (0x70000-0x7FFFF) is writable
                    data = (rel >= mb.writable_offset && rel < mb.writable_offset + mb.writable_size)
                           ? 0x00u : 0x01u;
                }
                else
                    data = 0x00u;
            }
            else
            {
                // Normal read: check writable sector first, then ROM
                if (rel >= mb.writable_offset &&
                    rel < mb.writable_offset + mb.writable_size)
                {
                    data = writable_sram[rel - mb.writable_offset];
                }
                else if (available_length == 0u || rel < available_length)
                {
                    data = read_rom_byte(rom_base, rel);
                }
            }
        }

        pio_sm_put_blocking(msx_bus.pio, msx_bus.sm_read, pio_build_token(in_window, data));
    }
}

// -----------------------------------------------------------------------
// loadrom_manbow2_scc - Manbow2 mapper with SCC/SCC+ sound emulation
// -----------------------------------------------------------------------
// Combines Manbow2 flash emulation (AMD AM29F040B) with SCC audio output
// via emu2212 + I2S on Core 1.  All writes pass through both the Manbow2
// flash/bank state machine AND the SCC emulator.  Reads check the SCC
// register window first, then autoselect, writable sector, and ROM.
void __no_inline_not_in_flash_func(loadrom_manbow2_scc)(uint32_t offset, bool cache_enable, uint32_t scc_type)
{
    const uint8_t *rom_base;
    uint32_t available_length;

    static const uint32_t WRITABLE_SECTOR_SIZE  = 0x10000u;
    static const uint32_t WRITABLE_SECTOR_OFFSET = 0x70000u;
    uint32_t reduced_cache = CACHE_SIZE - WRITABLE_SECTOR_SIZE;

    rom_cache_capacity = reduced_cache;
    prepare_rom_source(offset, cache_enable, 0u, &rom_base, &available_length);

    uint8_t *writable_sram = &rom_sram[reduced_cache];

    if (available_length >= WRITABLE_SECTOR_OFFSET + WRITABLE_SECTOR_SIZE)
    {
        const uint8_t *flash_rom = rom + offset;
        memcpy(writable_sram, flash_rom + WRITABLE_SECTOR_OFFSET, WRITABLE_SECTOR_SIZE);
    }
    else if (available_length > WRITABLE_SECTOR_OFFSET)
    {
        const uint8_t *flash_rom = rom + offset;
        uint32_t partial = available_length - WRITABLE_SECTOR_OFFSET;
        memcpy(writable_sram, flash_rom + WRITABLE_SECTOR_OFFSET, partial);
        memset(writable_sram + partial, 0xFF, WRITABLE_SECTOR_SIZE - partial);
    }
    else
    {
        memset(writable_sram, 0xFF, WRITABLE_SECTOR_SIZE);
    }

    manbow2_ctx_t mb = {
        .bank_regs = {0, 1, 2, 3},
        .state = MBW2_READ,
        .writable_sram = writable_sram,
        .writable_offset = WRITABLE_SECTOR_OFFSET,
        .writable_size = WRITABLE_SECTOR_SIZE,
        .rom_size_mask = 0
    };

    // Initialise SCC emulator
    memset(&scc_instance, 0, sizeof(SCC));
    scc_instance.clk  = SCC_CLOCK;
    scc_instance.rate = SCC_SAMPLE_RATE;
    SCC_set_quality(&scc_instance, 1);
    scc_instance.type = scc_type;
    SCC_reset(&scc_instance);

    // Start I2S audio subsystem, then launch audio on Core 1
    i2s_audio_init();
    multicore_launch_core1(core1_scc_audio);

    msx_pio_bus_init();

    while (true)
    {
        uint16_t addr;

        // Poll: drain write FIFO continuously while waiting for a read
        while (true)
        {
            uint16_t waddr;
            uint8_t wdata;
            while (pio_try_get_write(&waddr, &wdata))
            {
                handle_manbow2_write(waddr, wdata, &mb);
                SCC_write(&scc_instance, waddr, wdata);
            }
            if (!pio_sm_is_rx_fifo_empty(msx_bus.pio, msx_bus.sm_read))
            {
                addr = (uint16_t)pio_sm_get(msx_bus.pio, msx_bus.sm_read);
                break;
            }
        }

        // Drain any writes that arrived alongside the read
        {
            uint16_t waddr;
            uint8_t wdata;
            while (pio_try_get_write(&waddr, &wdata))
            {
                handle_manbow2_write(waddr, wdata, &mb);
                SCC_write(&scc_instance, waddr, wdata);
            }
        }

        bool in_window = (addr >= 0x4000u) && (addr <= 0xBFFFu);
        uint8_t data = 0xFFu;

        if (in_window)
        {
            // Check SCC register read region first
            bool is_scc_read = false;
            if (scc_instance.active)
            {
                uint32_t scc_reg_start = scc_instance.base_adr + 0x800u;
                if (addr >= scc_reg_start && addr <= (scc_reg_start + 0xFFu))
                    is_scc_read = true;
            }
            if (scc_type == SCC_ENHANCED && (addr & 0xFFFEu) == 0xBFFEu)
                is_scc_read = true;

            if (is_scc_read)
            {
                data = (uint8_t)SCC_read(&scc_instance, addr);
            }
            else
            {
                uint8_t page = (uint8_t)((addr - 0x4000u) >> 13);
                uint32_t rel = (uint32_t)mb.bank_regs[page] * 0x2000u + (addr & 0x1FFFu);

                if (mb.state == MBW2_AUTOSELECT)
                {
                    uint32_t id_addr = rel & 0x03u;
                    if (id_addr == 0x00u)
                        data = 0x01u;
                    else if (id_addr == 0x01u)
                        data = 0xA4u;
                    else if (id_addr == 0x02u)
                    {
                        data = (rel >= mb.writable_offset && rel < mb.writable_offset + mb.writable_size)
                               ? 0x00u : 0x01u;
                    }
                    else
                        data = 0x00u;
                }
                else
                {
                    if (rel >= mb.writable_offset &&
                        rel < mb.writable_offset + mb.writable_size)
                    {
                        data = writable_sram[rel - mb.writable_offset];
                    }
                    else if (available_length == 0u || rel < available_length)
                    {
                        data = read_rom_byte(rom_base, rel);
                    }
                }
            }
        }

        pio_sm_put_blocking(msx_bus.pio, msx_bus.sm_read, pio_build_token(in_window, data));
    }
}

// -----------------------------------------------------------------------
// Cases 17/18: Sunrise IDE + 1MB memory mapper + Carnivore2 RAM emulation
// -----------------------------------------------------------------------
// Targets Nextor's SROM /D15 path. Structurally identical to case 16
// (sunrise_mapper_sd) / case 11 (sunrise_mapper_usb): bootstrap warm-
// restart, then expanded-slot main loop with Nextor on sub-slot 0,
// 1 MB mapper RAM on sub-slot 1. On top of that the main loop:
//   * decodes I/O writes/reads on port 0xF0 + PFXN for SROM detection
//   * decodes memory accesses in the 64-byte Carnivore2 register window
//     (default 0x4F80-0x4FBF) and the four programmable bank windows,
//     routing reads/writes to a separate 1 MB PSRAM region (c2_rom_region)
//     that backs the emulated Carnivore2 RAM.
// Writes only touch c2 RAM when the owning bank has R*Mult[5]=1 (RAM select)
// and R*Mult[4]=1 (write enable). This mirrors the VHDL bank decode exactly
// enough for SROM to upload and launch a ROM image.

typedef void (*c2_core1_task_t)(void);
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
