taupter/msx-picoverse-public/2350/software/explorer.pio/msx/src/screen_rom.c

#include <string.h>
#include "menu.h"
#include "menu_state.h"
#include "menu_ui.h"
#include "menu_input.h"
#include "screen_rom.h"

static void send_detect_mapper(unsigned int index);
static unsigned char send_set_mapper(unsigned int index, unsigned char mapper);
static unsigned char send_load_options(unsigned int index, unsigned char *audio_profile, unsigned char *psg_enabled, unsigned char *mapper, unsigned char *sd_partition, unsigned char *audio_volume);
static void send_save_options(unsigned int index, unsigned char audio_profile, unsigned char psg_enabled, unsigned char mapper, unsigned char sd_partition, unsigned char audio_volume);
static void wait_for_ctrl_cmd_clear(void);
static unsigned char read_mapper_value(void);
static unsigned char read_ack_value(void);
static void render_rom_screen(const ROMRecord *record);
static void render_rom_prefixed_line(unsigned char row, const char *prefix, const char *text, int selected);
static void render_rom_mapper_line(const char *mapper_text, int selected);
static void render_rom_audio_line(const char *audio_text, int selected);
static void render_rom_volume_line(unsigned char audio_volume, int selected);
static void render_rom_psg_line(unsigned char psg_enabled, int selected);
static void render_rom_partition_line(unsigned char row, unsigned char sd_partition, int selected);
static void render_rom_wifi_line(unsigned char row, unsigned char wifi_enabled, int selected);
static void render_rom_action_line(unsigned char row, int selected);
static void render_rom_options_block(const ROMRecord *record, int waiting_mapper, unsigned char audio_profile, unsigned char psg_enabled, unsigned char wifi_enabled, unsigned char allow_mapper_override, unsigned char allow_wifi_support, int selection);
static void render_rom_footer_line(unsigned char mode);
static void show_mp3_screen(unsigned int index);
static void render_mp3_screen(const ROMRecord *record);
static void render_mp3_counter_line(void);
static void render_mp3_footer_line(void);
static void send_mp3_select(unsigned int index);
static unsigned int read_mp3_elapsed(void);
static unsigned int read_mp3_selected_index(void);
static ROMRecord *load_mp3_detail_record(unsigned int index);
static unsigned char footer_mode_for_selection(int selection, unsigned char allow_mapper_override, int psg_selection, int partition_selection, int wifi_selection);
static void build_mapper_text(const ROMRecord *record, int waiting_mapper, char *out, size_t out_size);
static void build_audio_text(const ROMRecord *record, unsigned char audio_profile, char *out, size_t out_size);
static unsigned char sanitize_audio_profile(const ROMRecord *record, unsigned char audio_profile);
static unsigned char next_audio_profile(const ROMRecord *record, unsigned char audio_profile, int dir);
static void apply_detected_mapper(ROMRecord *record);
static unsigned char current_wavegame_rom = 0;

#define MP3_COUNTER_POLL_JIFFIES 5
#define MP3_COUNTER_FORCE_JIFFIES 50
#define ROM_FOOTER_DEFAULT 0
#define ROM_FOOTER_MAPPER  1
#define ROM_FOOTER_AUDIO   2
#define ROM_FOOTER_PSG     3
#define ROM_FOOTER_WIFI    4
#define ROM_FOOTER_RUN     5
#define ROM_FOOTER_SD      6

static unsigned char sd_partition_count = 0;
static unsigned char sd_partition_mask = 0;
static unsigned char rom_sd_partition = 0;
static unsigned char rom_audio_volume = AUDIO_VOLUME_DEFAULT;
static unsigned char rom_allow_sd_partition = 0;

static void write_index_query(unsigned int index) {
    Poke(CTRL_QUERY_BASE + 0, (unsigned char)(index & 0xFFu));
    Poke(CTRL_QUERY_BASE + 1, (unsigned char)((index >> 8) & 0xFFu));
}

static unsigned char record_is_system_rom(const ROMRecord *record) {
    unsigned char mapper_code = record_mapper_code(record->Mapper);
    return mapper_code == 9 || (mapper_code >= 10 && mapper_code <= 11) || (mapper_code >= 15 && mapper_code <= 21);
}

static unsigned char record_is_wifi_capable_system_rom(const ROMRecord *record) {
    unsigned char mapper_code = record_mapper_code(record->Mapper);
    return (mapper_code >= 10 && mapper_code <= 11) || (mapper_code >= 15 && mapper_code <= 16);
}

static unsigned char record_is_sunrise_system_rom(const ROMRecord *record) {
    unsigned char mapper_code = record_mapper_code(record->Mapper);
    return (mapper_code >= 10 && mapper_code <= 11) || (mapper_code >= 15 && mapper_code <= 18);
}

static unsigned char record_is_sunrise_sd_system_rom(const ROMRecord *record) {
    unsigned char mapper_code = record_mapper_code(record->Mapper);
    return mapper_code >= 15 && mapper_code <= 19 && mapper_code != 18;
}

static unsigned char record_is_sunrise_mapper_system_rom(const ROMRecord *record) {
    unsigned char mapper_code = record_mapper_code(record->Mapper);
    return mapper_code == 11 || (mapper_code >= 16 && mapper_code <= 21);
}

static unsigned char record_supports_scc_audio(const ROMRecord *record) {
    unsigned char mapper_code = record_mapper_code(record->Mapper);
    return mapper_code == 3 || mapper_code == 14;
}

static unsigned char record_supports_external_scc_audio(const ROMRecord *record) {
    return !record_is_folder(record) && (!record_is_system_rom(record) || record_is_sunrise_system_rom(record));
}

static unsigned char record_supports_dual_psg(const ROMRecord *record) {
    return record_supports_external_scc_audio(record) && !record_supports_scc_audio(record);
}

static unsigned char record_supports_msx_music(const ROMRecord *record) {
    /* Base support shared with YM2151/SFG. YM2413/FM-PAC (MSX-MUSIC) additionally
       excludes the Sunrise 1MB-mapper options in audio_profile_is_supported(). */
    return record_supports_external_scc_audio(record);
}

static void send_detect_mapper(unsigned int index) {
    write_index_query(index);
    for (unsigned int i = 2; i < CTRL_QUERY_SIZE; i++) {
        Poke(CTRL_QUERY_BASE + i, 0);
    }
    Poke(CTRL_CMD, CMD_DETECT_MAPPER);
}

static void wait_for_ctrl_cmd_clear(void) {
    for (unsigned int wait = 0; wait < 200; wait++) {
        if (Peek(CTRL_CMD) == 0) {
            break;
        }
        delay_ms(5);
    }
}

static unsigned char send_set_mapper(unsigned int index, unsigned char mapper) {
    write_index_query(index);
    Poke(CTRL_QUERY_BASE + 2, mapper);
    for (unsigned int i = 3; i < CTRL_QUERY_SIZE; i++) {
        Poke(CTRL_QUERY_BASE + i, 0);
    }
    Poke(CTRL_CMD, CMD_SET_MAPPER);
    wait_for_ctrl_cmd_clear();
    return read_ack_value();
}

static unsigned char send_load_options(unsigned int index, unsigned char *audio_profile, unsigned char *psg_enabled, unsigned char *mapper, unsigned char *sd_partition, unsigned char *audio_volume) {
    write_index_query(index);
    for (unsigned int i = 2; i < CTRL_QUERY_SIZE; i++) {
        Poke(CTRL_QUERY_BASE + i, 0);
    }
    Poke(CTRL_CMD, CMD_LOAD_OPTIONS);
    wait_for_ctrl_cmd_clear();
    current_wavegame_rom = Peek(CTRL_WAVEGAME_ROM) ? 1 : 0;
    if (!read_ack_value()) {
        return 0;
    }
    *audio_profile = Peek(CTRL_AUDIO);
    *psg_enabled = Peek(CTRL_PSG_EMULATION) ? 1 : 0;
    *mapper = Peek(CTRL_MAPPER);
    *sd_partition = Peek(CTRL_SD_PARTITION);
    *audio_volume = Peek(CTRL_AUDIO_VOLUME);
    sd_partition_count = Peek(CTRL_SD_PARTITION_INFO_BASE);
    sd_partition_mask = Peek(CTRL_SD_PARTITION_INFO_BASE + 1);
    return 1;
}

static void send_save_options(unsigned int index, unsigned char audio_profile, unsigned char psg_enabled, unsigned char mapper, unsigned char sd_partition, unsigned char audio_volume) {
    write_index_query(index);
    Poke(CTRL_QUERY_BASE + 2, audio_profile);
    Poke(CTRL_QUERY_BASE + 3, psg_enabled ? 1 : 0);
    Poke(CTRL_QUERY_BASE + 4, mapper);
    Poke(CTRL_QUERY_BASE + 5, sd_partition);
    Poke(CTRL_QUERY_BASE + 6, audio_volume);
    for (unsigned int i = 7; i < CTRL_QUERY_SIZE; i++) {
        Poke(CTRL_QUERY_BASE + i, 0);
    }
    Poke(CTRL_CMD, CMD_SAVE_OPTIONS);
    wait_for_ctrl_cmd_clear();
}

static unsigned char read_mapper_value(void) {
    return *((unsigned char *)CTRL_MAPPER);
}

static unsigned char read_ack_value(void) {
    return *((unsigned char *)CTRL_ACK);
}

static void apply_detected_mapper(ROMRecord *record) {
    unsigned char mapper = read_mapper_value();
    if (mapper != 0) {
        record->Mapper = (record->Mapper & (SOURCE_SD_FLAG | FOLDER_FLAG)) | mapper;
    } else {
        record->Mapper = (record->Mapper & (SOURCE_SD_FLAG | FOLDER_FLAG));
    }
}

void quick_run_rom(unsigned int index) {
    ROMRecord *record = &records[index % FILES_PER_PAGE];
    write_index_query(index);
    Poke(CTRL_CMD, CMD_PREPARE_QUICK_RUN);
    while (Peek(CTRL_CMD) != 0) {
        delay_ms(10);
    }
    apply_detected_mapper(record);
    loadGame((int)index);
}

static void render_rom_screen(const ROMRecord *record) {
    menu_ui_render_detail_frame();

    {
        char name[MAX_FILE_NAME_LENGTH + 1];
        const char *source = (record->Mapper & SOURCE_SD_FLAG) ? "SD" : "FL";
        unsigned long size_kb = record->Size / 1024u;

        trim_name_to_buffer(record->Name, name, use_80_columns ? 71 : 29);

        Locate(0, 3);
        if (use_80_columns) {
            printf("    ROM: %-71.71s", name);
        } else {
            printf("    ROM: %-29.29s", name);
        }

        Locate(0, 4);
        printf("   Size: %lu KB", size_kb);
        Locate(0, 5);
        printf(" Source: %s", source);
        Locate(0, 6);
        printf(" ");
    }
}

void show_rom_screen(unsigned int index) {
    ROMRecord *record = &records[index % FILES_PER_PAGE];
    unsigned char waiting_mapper = 0;
    unsigned char audio_profile = AUDIO_PROFILE_NONE;
    unsigned char psg_enabled = 1;
    unsigned char saved_mapper = 0;
    unsigned char sd_partition = 0;
    unsigned char options_loaded = 0;
    unsigned char allow_mapper_override = !record_is_system_rom(record);
    unsigned char allow_wifi_support = record_is_wifi_capable_system_rom(record);
    unsigned char allow_sd_partition = record_is_sunrise_sd_system_rom(record);
    unsigned char allow_psg = !record_is_sunrise_mapper_system_rom(record);
    unsigned char wifi_enabled = 0;
    int volume_selection = 2;
    int psg_selection = 3;
    int partition_selection = allow_sd_partition ? 4 : -1;
    int wifi_selection = allow_wifi_support ? (allow_sd_partition ? 5 : 4) : -1;
    int action_selection = 4 + (allow_sd_partition ? 1 : 0) + (allow_wifi_support ? 1 : 0);
    int selection = action_selection;

    rom_allow_sd_partition = allow_sd_partition;
    rom_audio_volume = AUDIO_VOLUME_DEFAULT;

    if (record_is_mp3(record)) {
        show_mp3_screen(index);
        return;
    }

    render_rom_screen(record);

    if ((record->Mapper & SOURCE_SD_FLAG) && !record_is_folder(record)) {
        unsigned char mapper_code = record_mapper_code(record->Mapper);
        if (mapper_code == 0) {
            wait_for_ctrl_cmd_clear();
            send_detect_mapper(index);
            waiting_mapper = 1;
        } else if (record_supports_scc_audio(record)) {
            audio_profile = AUDIO_PROFILE_SCC;
        }
    } else {
        if (record_supports_scc_audio(record)) {
            audio_profile = AUDIO_PROFILE_SCC;
        }
    }

    if (!waiting_mapper) {
        options_loaded = send_load_options(index, &audio_profile, &psg_enabled, &saved_mapper, &sd_partition, &rom_audio_volume);
        if (options_loaded && saved_mapper != 0 && allow_mapper_override) {
                record->Mapper = (record->Mapper & (SOURCE_SD_FLAG | FOLDER_FLAG)) | saved_mapper;
        }
    }
    audio_profile = sanitize_audio_profile(record, audio_profile);
    if (!allow_psg) {
        psg_enabled = 0; // PSG Mirror is disabled on Nextor + 1MB mapper (unstable)
    }

    rom_sd_partition = sd_partition;
    render_rom_options_block(record, waiting_mapper, audio_profile, psg_enabled, wifi_enabled, allow_mapper_override, allow_wifi_support, selection);

    while (1) {
        if (bios_chsns()) {
            char key = (char)bios_chget();
            if (key == MENU_KEY_F4_CONFIG) {
                launch_wifi_config();
                return;
            }
            if (key == 'h' || key == 'H') {
                helpMenu();
                render_rom_screen(record);
                render_rom_options_block(record, waiting_mapper, audio_profile, psg_enabled, wifi_enabled, allow_mapper_override, allow_wifi_support, selection);
            }
            if (key == 27) {
                break;
            }
            if (key == 13 || key == 32) {
                if (!waiting_mapper && selection == action_selection) {
                    audio_profile = sanitize_audio_profile(record, audio_profile);
                    Poke(CTRL_AUDIO, audio_profile);
                    Poke(CTRL_PSG_EMULATION, psg_enabled);
                    Poke(CTRL_WIFI_SUPPORT, allow_wifi_support ? wifi_enabled : 0);
                    Poke(CTRL_SD_PARTITION, allow_sd_partition ? sd_partition : 0);
                    Poke(CTRL_AUDIO_VOLUME, rom_audio_volume);
                    send_save_options(index, audio_profile, psg_enabled, record_mapper_code(record->Mapper), allow_sd_partition ? sd_partition : 0, rom_audio_volume);
                    loadGame((int)index);
                    return;
                }
            }
            if (key == 30 || key == 31) {
                int delta = (key == 30) ? -1 : 1;
                int next = selection + delta;
                if (next < 0) {
                    next = 0;
                } else if (next > action_selection) {
                    next = action_selection;
                }
                if (selection != next) {
                    selection = next;
                    render_rom_options_block(record, waiting_mapper, audio_profile, psg_enabled, wifi_enabled, allow_mapper_override, allow_wifi_support, selection);
                }
            }
            if ((key == 28 || key == 29) && selection == 0 && !waiting_mapper && allow_mapper_override) {
                static const unsigned char mapper_cycle[] = {1,2,3,4,5,6,7,8,9,12,13,14};
                const unsigned int mapper_count = (unsigned int)(sizeof(mapper_cycle) / sizeof(mapper_cycle[0]));
                unsigned char mapper_code = record_mapper_code(record->Mapper);
                int dir = (key == 28) ? 1 : -1;
                int found = -1;
                for (unsigned int i = 0; i < mapper_count; i++) {
                    if (mapper_cycle[i] == mapper_code) {
                        found = (int)i;
                        break;
                    }
                }
                int next_index = 0;
                if (found < 0) {
                    next_index = (dir > 0) ? 0 : (int)(mapper_count - 1);
                } else {
                    next_index = found + dir;
                    if (next_index < 0) {
                        next_index = (int)(mapper_count - 1);
                    } else if ((unsigned int)next_index >= mapper_count) {
                        next_index = 0;
                    }
                }
                unsigned char next_mapper = mapper_cycle[next_index];
                if (send_set_mapper(index, next_mapper)) {
                    record->Mapper = (record->Mapper & (SOURCE_SD_FLAG | FOLDER_FLAG)) | next_mapper;
                    audio_profile = sanitize_audio_profile(record, audio_profile);
                    render_rom_options_block(record, waiting_mapper, audio_profile, psg_enabled, wifi_enabled, allow_mapper_override, allow_wifi_support, selection);
                }
            }
            if ((key == 28 || key == 29) && selection == 1) {
                int dir = (key == 28) ? 1 : -1;
                audio_profile = next_audio_profile(record, audio_profile, dir);
                render_rom_options_block(record, waiting_mapper, audio_profile, psg_enabled, wifi_enabled, allow_mapper_override, allow_wifi_support, selection);
            }
            if ((key == 28 || key == 29) && selection == volume_selection) {
                if (key == 28) {
                    if (rom_audio_volume < AUDIO_VOLUME_MAX) rom_audio_volume += AUDIO_VOLUME_STEP;
                } else {
                    if (rom_audio_volume >= AUDIO_VOLUME_STEP) rom_audio_volume -= AUDIO_VOLUME_STEP;
                }
                render_rom_options_block(record, waiting_mapper, audio_profile, psg_enabled, wifi_enabled, allow_mapper_override, allow_wifi_support, selection);
            }
            if ((key == 28 || key == 29) && selection == psg_selection && allow_psg) {
                psg_enabled = psg_enabled ? 0 : 1;
                render_rom_options_block(record, waiting_mapper, audio_profile, psg_enabled, wifi_enabled, allow_mapper_override, allow_wifi_support, selection);
            }
            if ((key == 28 || key == 29) && allow_sd_partition && selection == partition_selection && sd_partition_count) {
                int dir = (key == 28) ? 1 : -1;
                unsigned char next_part = sd_partition;
                for (unsigned char i = 0; i < 4; i++) {
                    next_part = (unsigned char)(next_part + dir);
                    if (next_part < 1) {
                        next_part = 4;
                    } else if (next_part > 4) {
                        next_part = 1;
                    }
                    if (sd_partition_mask & (1 << (next_part - 1))) {
                        break;
                    }
                }
                sd_partition = next_part;
                rom_sd_partition = sd_partition;
                Poke(CTRL_SD_PARTITION, sd_partition);
                render_rom_options_block(record, waiting_mapper, audio_profile, psg_enabled, wifi_enabled, allow_mapper_override, allow_wifi_support, selection);
            }
            if ((key == 28 || key == 29) && allow_wifi_support && selection == wifi_selection) {
                wifi_enabled = wifi_enabled ? 0 : 1;
                render_rom_options_block(record, waiting_mapper, audio_profile, psg_enabled, wifi_enabled, allow_mapper_override, allow_wifi_support, selection);
            }
            if (key == 'C' || key == 'c') {
                if (menu_ui_try_toggle_columns()) {
                    render_rom_screen(record);
                    render_rom_options_block(record, waiting_mapper, audio_profile, psg_enabled, wifi_enabled, allow_mapper_override, allow_wifi_support, selection);
                }
            }
        }

        if (waiting_mapper && Peek(CTRL_CMD) == 0) {
            apply_detected_mapper(record);
            if (audio_profile == AUDIO_PROFILE_NONE && record_supports_scc_audio(record)) {
                audio_profile = AUDIO_PROFILE_SCC;
            } else {
                audio_profile = sanitize_audio_profile(record, audio_profile);
            }
            if (!options_loaded) {
                options_loaded = send_load_options(index, &audio_profile, &psg_enabled, &saved_mapper, &sd_partition, &rom_audio_volume);
                if (options_loaded && saved_mapper != 0 && allow_mapper_override) {
                    record->Mapper = (record->Mapper & (SOURCE_SD_FLAG | FOLDER_FLAG)) | saved_mapper;
                }
            }
            audio_profile = sanitize_audio_profile(record, audio_profile);
            waiting_mapper = 0;
            rom_sd_partition = sd_partition;
            render_rom_options_block(record, waiting_mapper, audio_profile, psg_enabled, wifi_enabled, allow_mapper_override, allow_wifi_support, selection);
        }

        delay_ms(10);
    }

    frame_rendered = 0;
    displayMenu();
}

static void render_rom_prefixed_line(unsigned char row, const char *prefix, const char *text, int selected) {
    char line[80];
    size_t prefix_len = strlen(prefix);
    size_t out_len = 0;
    if (prefix_len >= sizeof(line)) {
        prefix_len = sizeof(line) - 1;
    }
    memcpy(line, prefix, prefix_len);
    out_len = prefix_len;
    line[out_len] = '\0';

    if (text && out_len < (sizeof(line) - 1)) {
        size_t remaining = sizeof(line) - 1 - out_len;
        size_t text_len = strlen(text);
        if (text_len > remaining) {
            text_len = remaining;
        }
        memcpy(line + out_len, text, text_len);
        out_len += text_len;
        line[out_len] = '\0';
    }

    menu_ui_render_selectable_line(row, line, selected);
}

static void render_rom_mapper_line(const char *mapper_text, int selected) {
    render_rom_prefixed_line(7, "    Mapper: ", mapper_text, selected);
}

static void render_rom_audio_line(const char *audio_text, int selected) {
    render_rom_prefixed_line(8, "     Audio: ", audio_text, selected);
}

static void render_rom_volume_line(unsigned char audio_volume, int selected) {
    char line[80];
    sprintf(line, "    Volume: %u%%", audio_volume);
    menu_ui_render_selectable_line(9, line, selected);
}

static void render_rom_psg_line(unsigned char psg_enabled, int selected) {
    render_rom_prefixed_line(10, "PSG Mirror: ", psg_enabled ? "Yes" : "No", selected);
}

static void render_rom_partition_line(unsigned char row, unsigned char sd_partition, int selected) {
    char label[31];
    unsigned char i;
    (void)sd_partition;
    for (i = 0; i < sizeof(label) - 1; i++) {
        label[i] = (char)Peek(CTRL_SD_PARTITION_INFO_BASE + 2 + i);
        if (!label[i]) {
            break;
        }
    }
    label[sizeof(label) - 1] = '\0';
    render_rom_prefixed_line(row, "   SD Part: ", label, selected);
}

static void render_rom_wifi_line(unsigned char row, unsigned char wifi_enabled, int selected) {
    render_rom_prefixed_line(row, "      Wifi: ", wifi_enabled ? "Yes" : "No", selected);
}
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
